commaai/neo/interface boards/gm/case.stl

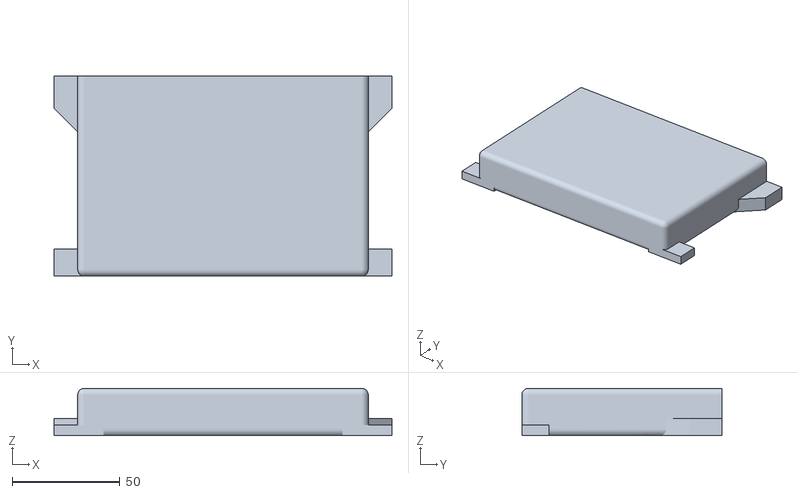
[picture p27: CAD file, 2019-02-15]
interface boards/gm/case.stl
157.0 x 93.0 x 22.0
