commaai/neo/pedal/case/pedal_connector.stl

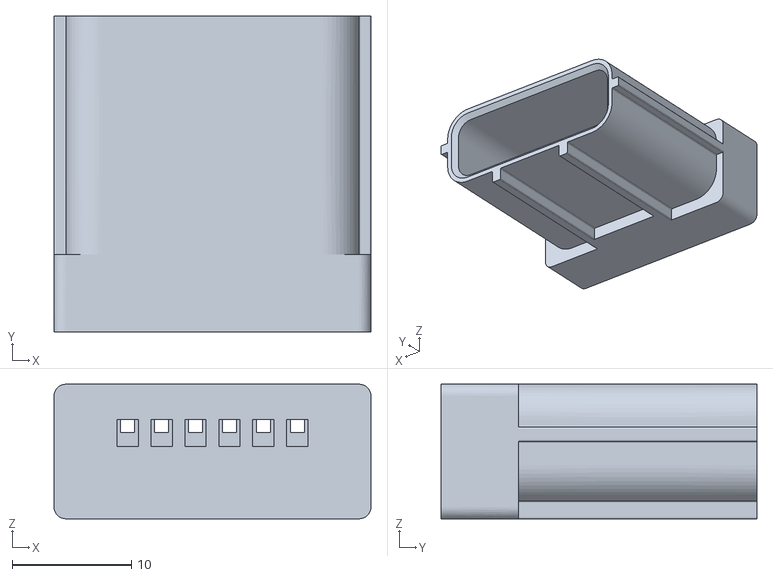
[picture p28: CAD file, 2018-03-29]
pedal/case/pedal_connector.stl
26.6 x 26.5 x 11.3
