commaai/neo/body/universal_C3_C3X_hat_frame.stl

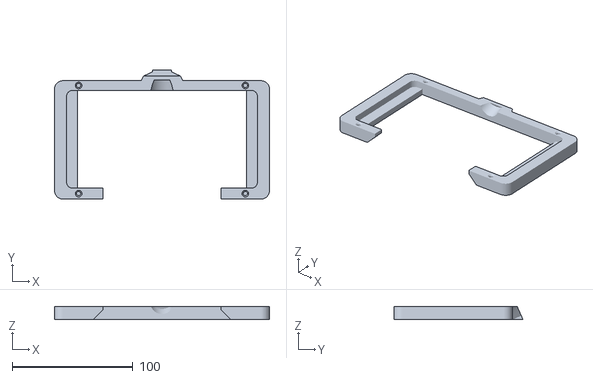
[picture p29: CAD file, 2023-12-14]
body/universal_C3_C3X_hat_frame.stl
178.0 x 106.9 x 11.0
