commaai/neo/case/comma2/comma2_mount.stl

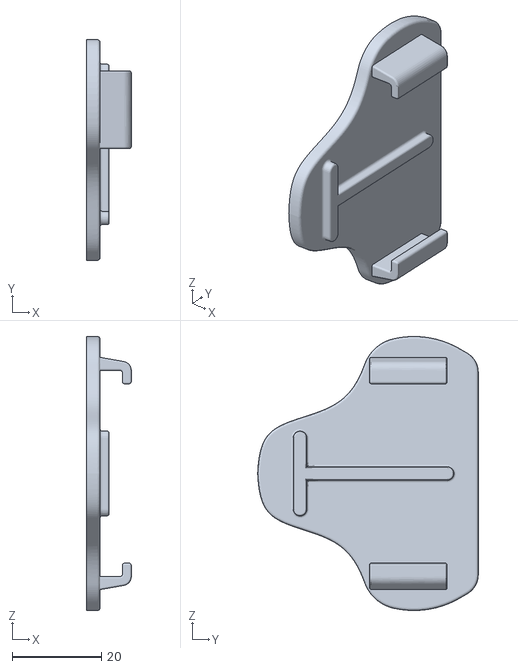
[picture p30: CAD file, 2020-01-23]
case/comma2/comma2_mount.stl
10.0 x 49.5 x 61.5
