commaai/neo/case/comma3/comma3_mount.stl

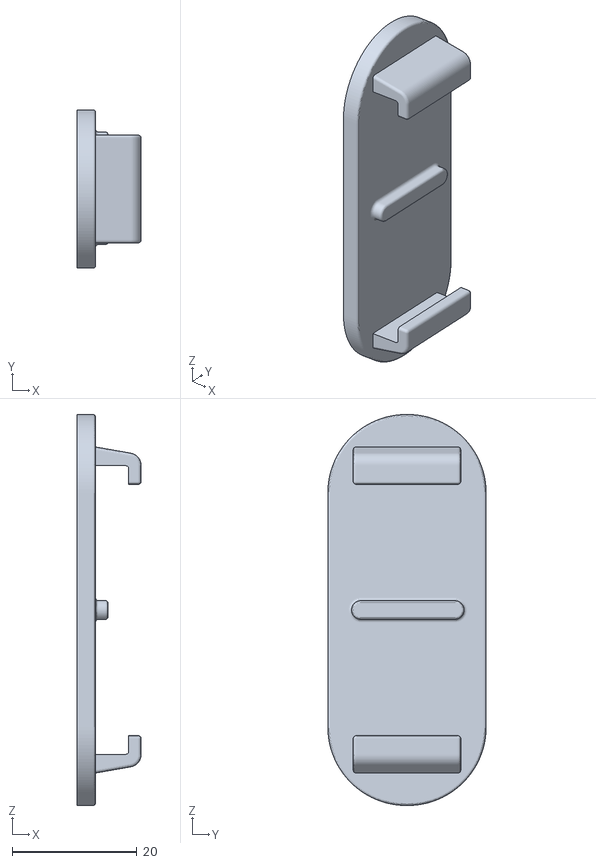
[picture p31: CAD file, 2021-10-15]
case/comma3/comma3_mount.stl
10.3 x 25.4 x 62.6
