commaai/neo/case/comma3X/3X_mount_8deg.stl

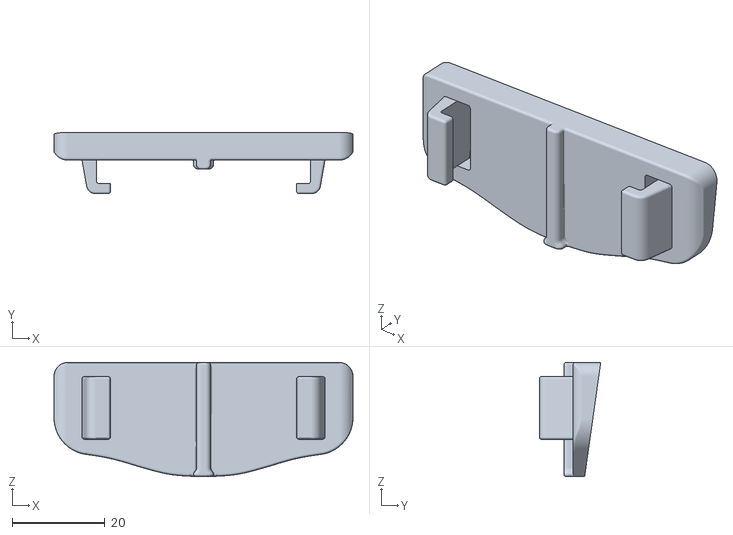
[picture p32: CAD file, 2023-07-31]
case/comma3X/3X_mount_8deg.stl
64.6 x 13.3 x 24.7
