commaai/neo/case/eon/30deg.stl

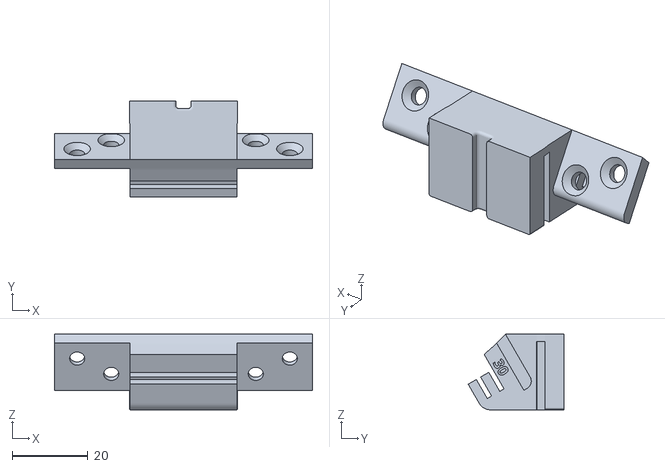
[picture p33: CAD file, 2018-02-07]
case/eon/30deg.stl
68.2 x 25.3 x 20.0
