commaai/neo/case/goproslide.stl

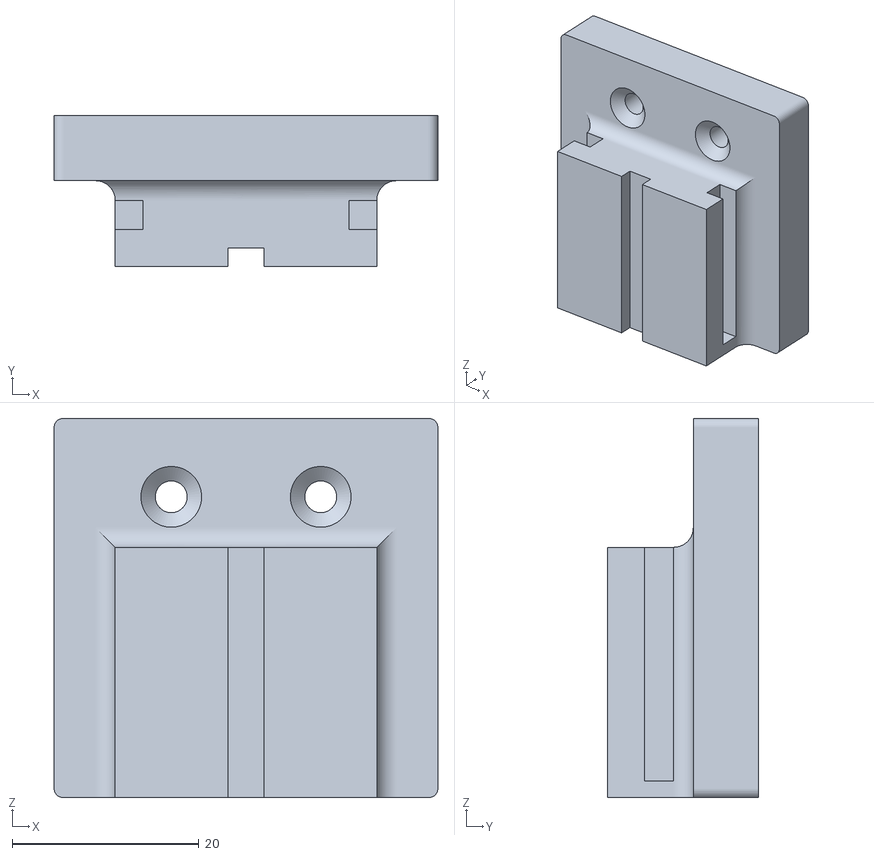
[picture p34: CAD file, 2017-01-27]
case/goproslide.stl
41.1 x 16.2 x 40.6
