commaai/neo/giraffe/fca/Giraffe_right.stl

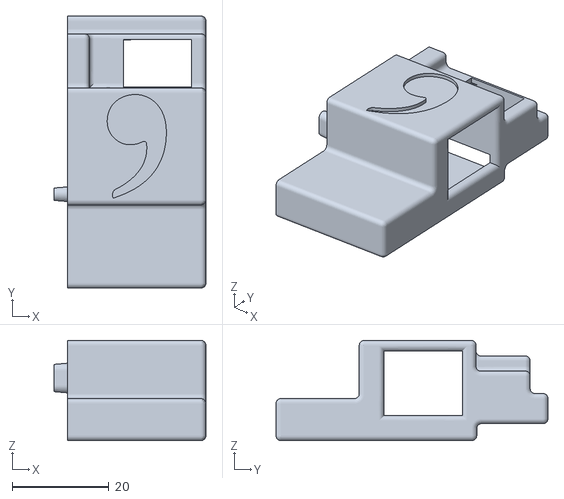
[picture p35: CAD file, 2019-02-05]
giraffe/fca/Giraffe_right.stl
31.4 x 56.2 x 20.7
