commaai/neo/giraffe/ford/mechanical/giraffe_ford_top.stl

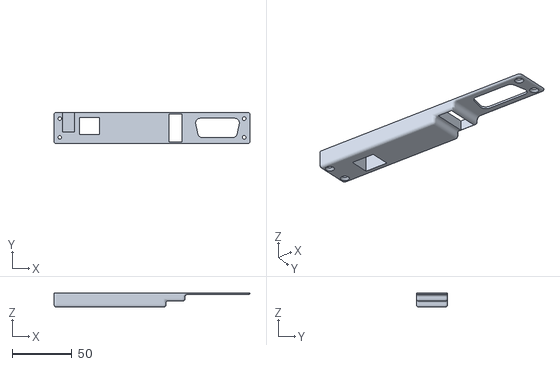
[picture p36: CAD file, 2018-09-11]
giraffe/ford/mechanical/giraffe_ford_top.stl
164.5 x 26.4 x 11.9
