commaai/neo/giraffe/honda/bosch/bosch_female_connector.stl

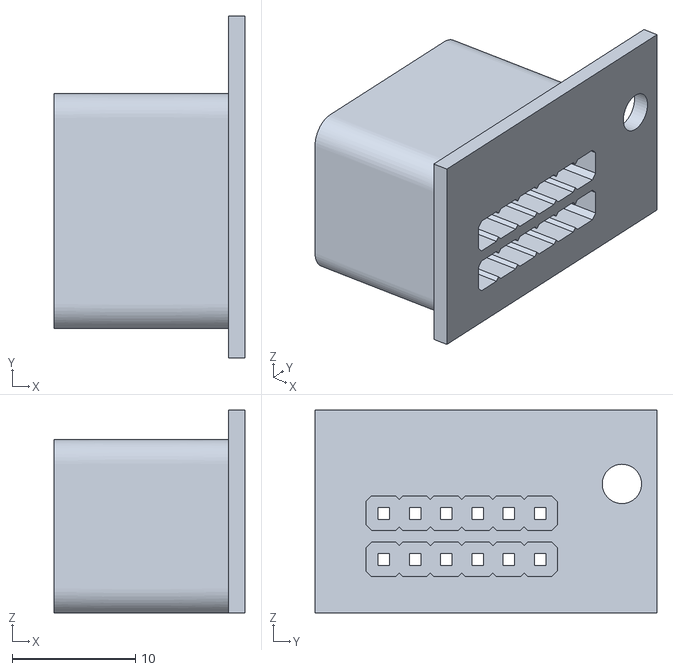
[picture p37: CAD file, 2018-08-07]
giraffe/honda/bosch/bosch_female_connector.stl
15.5 x 27.8 x 16.5
