commaai/neo/giraffe/subaru/PIP_left.stl

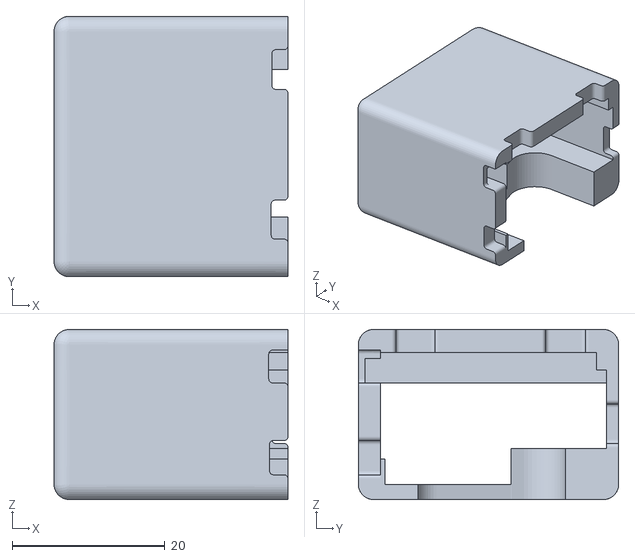
[picture p38: CAD file, 2019-04-23]
giraffe/subaru/PIP_left.stl
30.6 x 34.1 x 22.3
