commaai/neo/grey/antenna_mount_28deg.stl

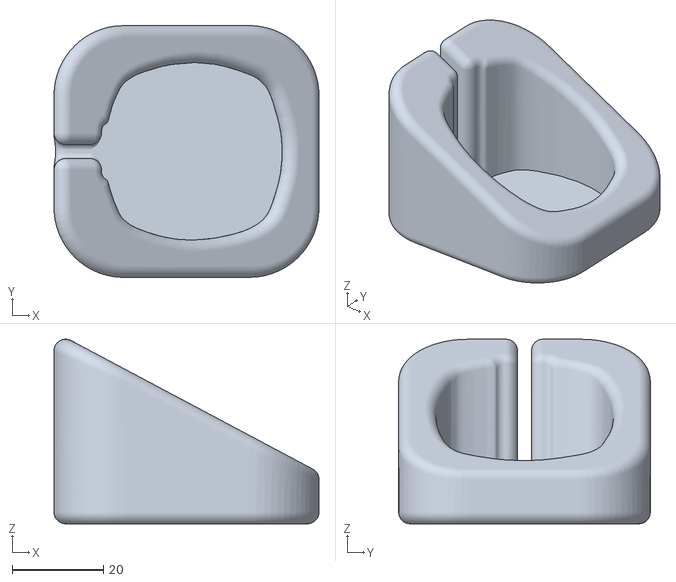
[picture p39: CAD file, 2018-09-11]
grey/antenna_mount_28deg.stl
58.0 x 55.1 x 40.4
