commaai/neo/interface boards/gm/connectors.stl

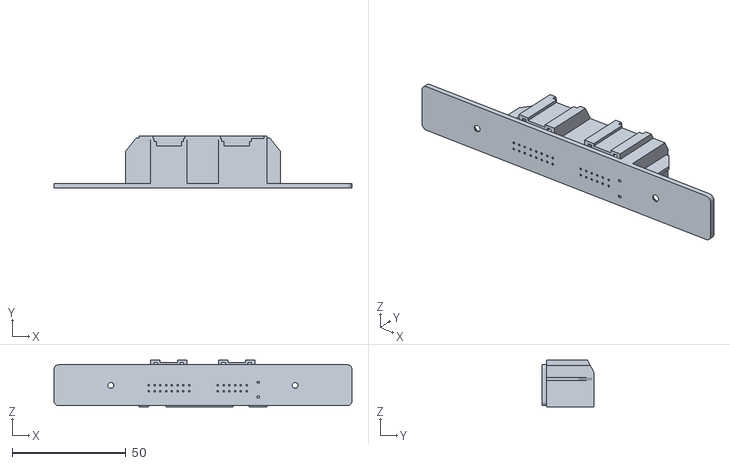
[picture p40: CAD file, 2019-02-15]
interface boards/gm/connectors.stl
131.0 x 23.0 x 20.5
