commaai/neo/pedal/case/comma.stl

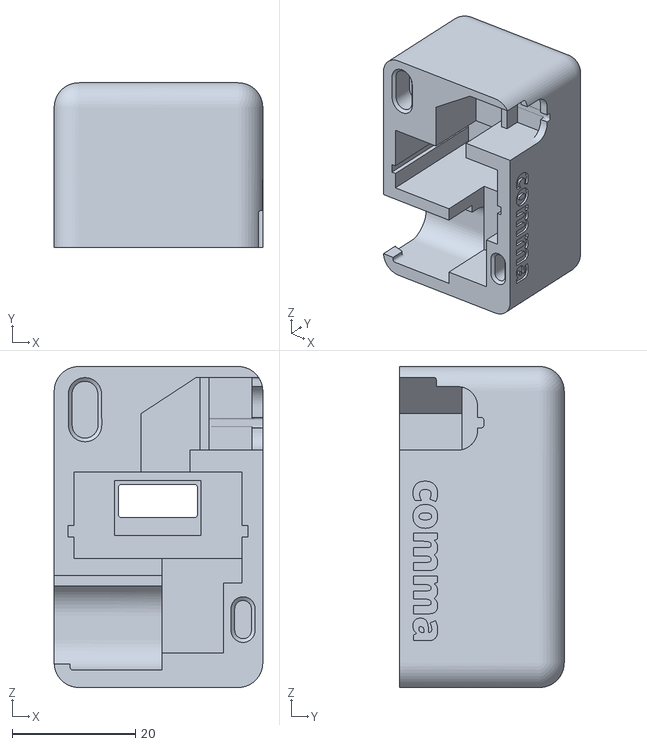
[picture p41: CAD file, 2018-03-29]
pedal/case/comma.stl
33.8 x 26.6 x 52.0
