commaai/neo/body/wheeled_stand.stl

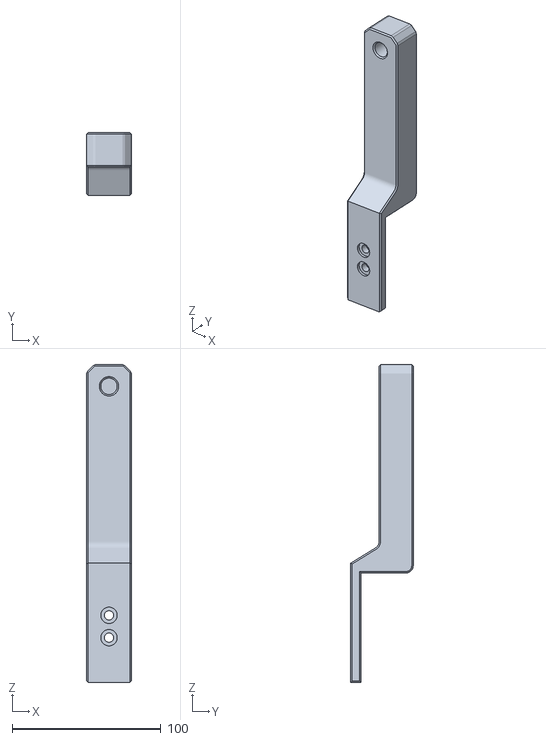
[picture p42: CAD file, 2023-12-14]
body/wheeled_stand.stl
30.0 x 42.0 x 213.5
