commaai/neo/case/cover.stl

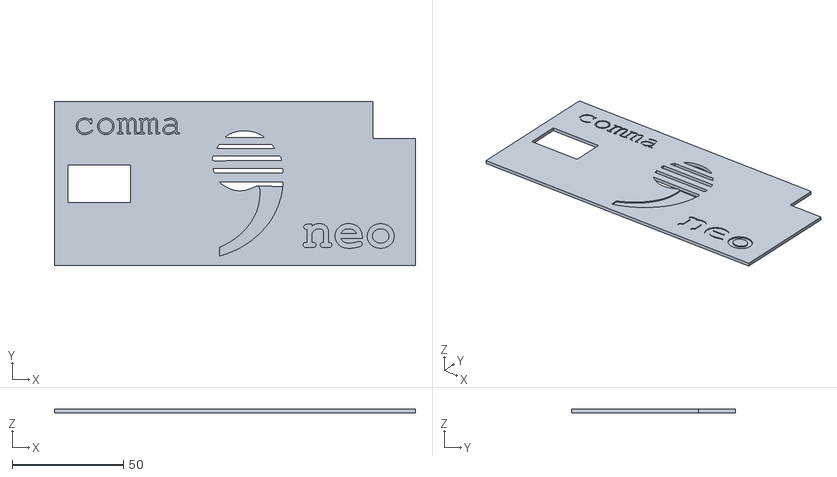
[picture p43: CAD file, 2016-11-30]
case/cover.stl
162.5 x 73.9 x 1.60
