commaai/neo/case/eon/24deg.stl

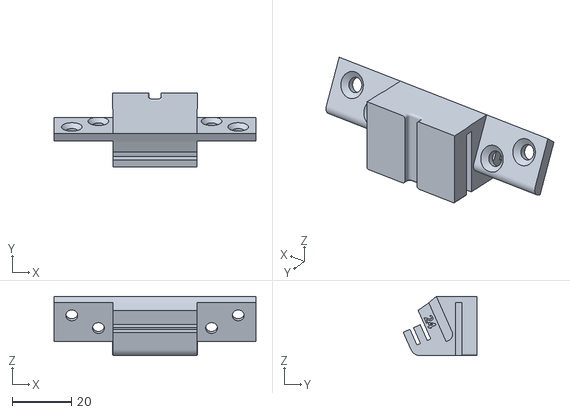
[picture p44: CAD file, 2018-02-07]
case/eon/24deg.stl
68.2 x 24.8 x 20.0
