commaai/neo/giraffe/ford/mechanical/giraffe_ford_bottom.stl

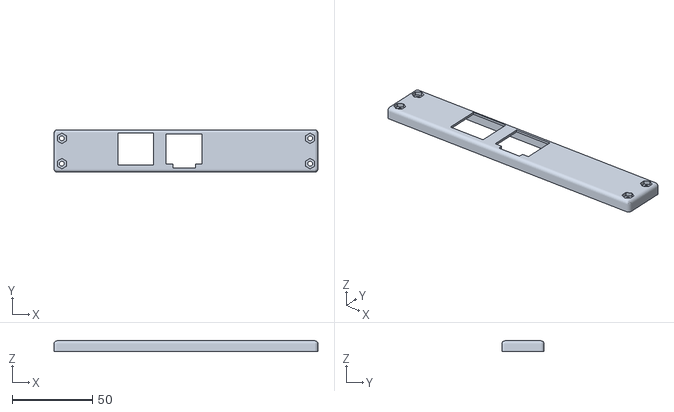
[picture p45: CAD file, 2018-09-11]
giraffe/ford/mechanical/giraffe_ford_bottom.stl
164.5 x 26.4 x 6.57
