commaai/neo/giraffe/honda/bosch/bosch_male.stl

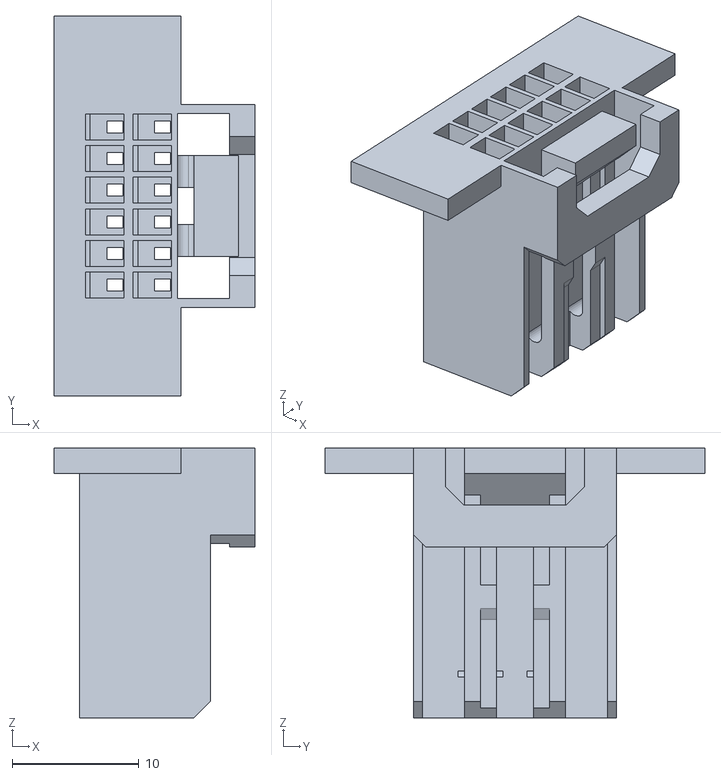
[picture p46: CAD file, 2018-08-07]
giraffe/honda/bosch/bosch_male.stl
15.9 x 30.0 x 21.3
