commaai/neo/grey/antenna_mount.stl

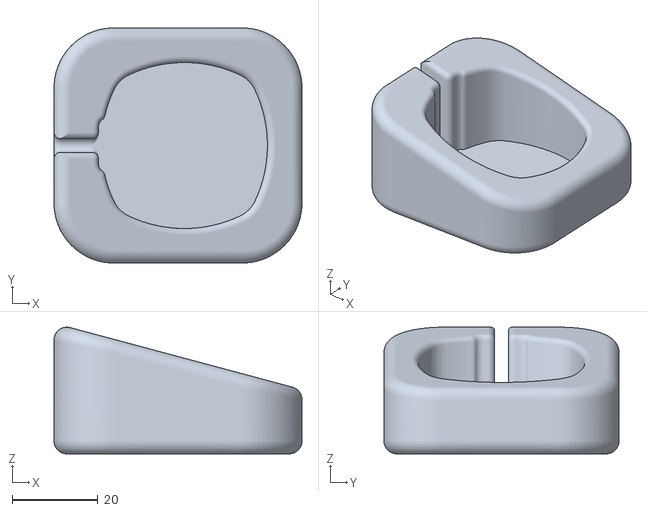
[picture p47: CAD file, 2018-03-01]
grey/antenna_mount.stl
58.0 x 55.0 x 29.6
