commaai/neo/pedal/case/pedal.stl

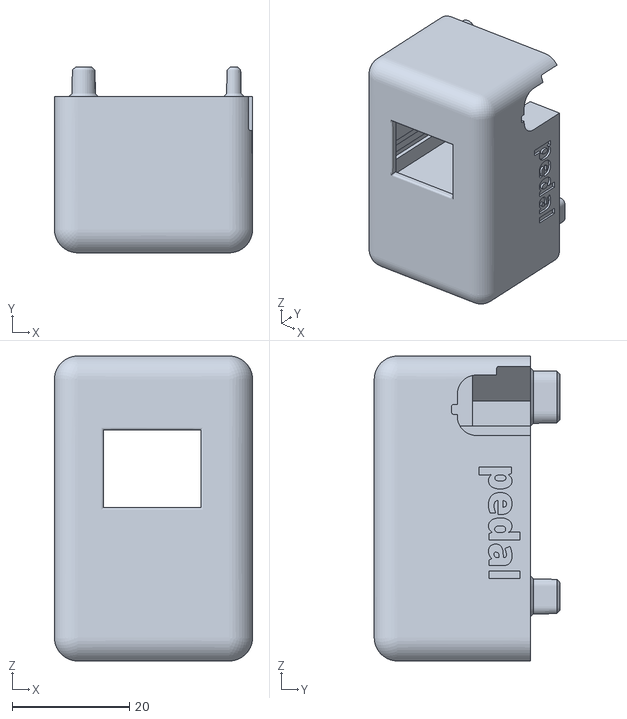
[picture p48: CAD file, 2018-03-29]
pedal/case/pedal.stl
33.8 x 31.7 x 52.0
