commaai/neo/body/C3_stand.stl

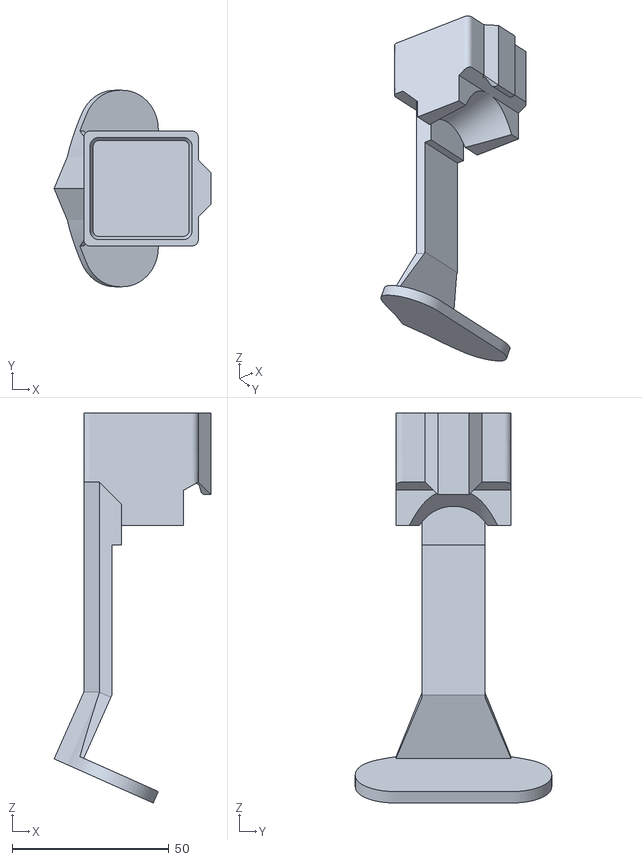
[picture p49: CAD file, 2022-05-08]
body/C3_stand.stl
50.0 x 62.6 x 124.2
