commaai/neo/case/mount.stl

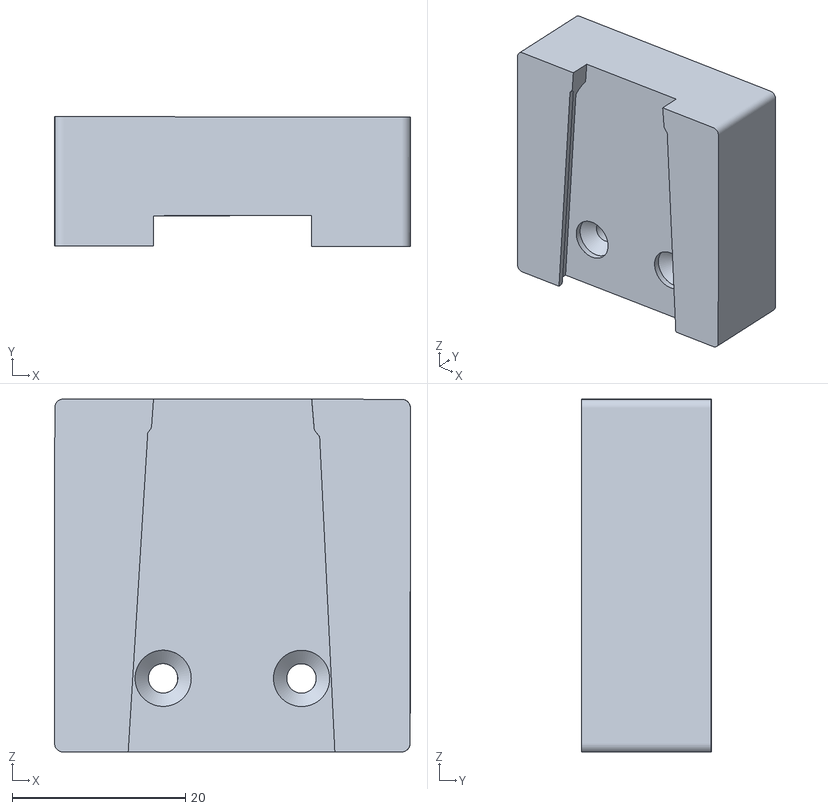
[picture p50: CAD file, 2016-11-30]
case/mount.stl
41.2 x 15.0 x 40.8
