commaai/neo/giraffe/honda/bosch/bosch_front.stl

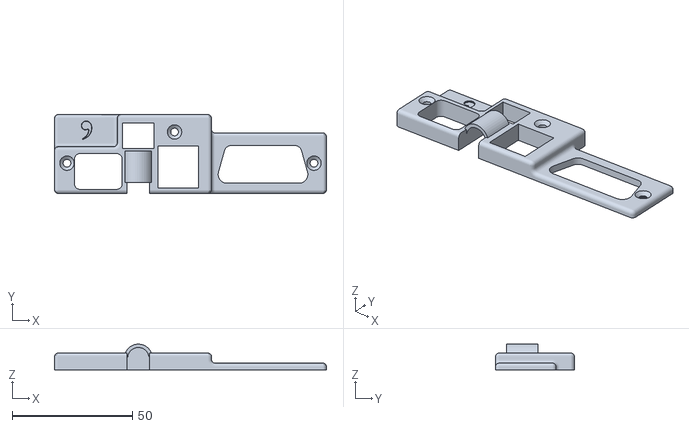
[picture p51: CAD file, 2018-08-07]
giraffe/honda/bosch/bosch_front.stl
113.0 x 32.7 x 10.7
