commaai/neo/case/bottom.stl

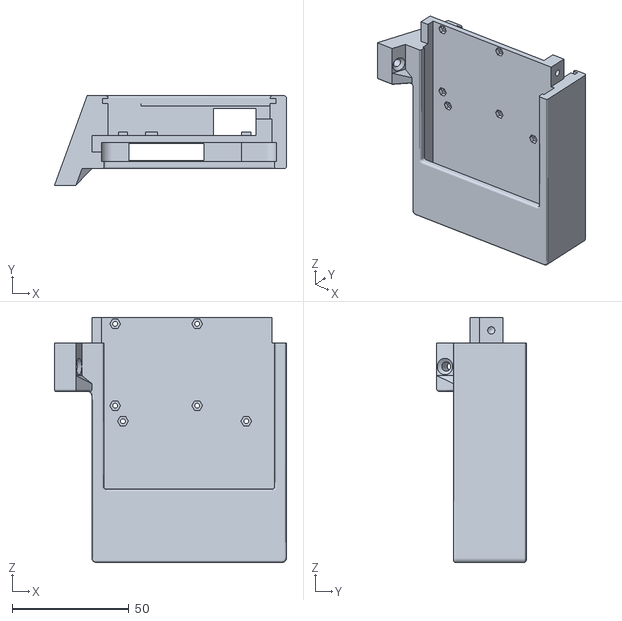
[picture p52: CAD file, 2016-11-30]
case/bottom.stl
99.3 x 38.3 x 104.9
