commaai/neo/case/top.stl

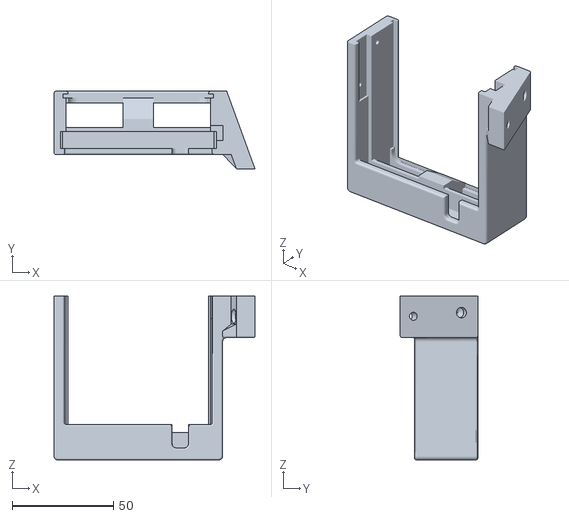
[picture p53: CAD file, 2016-11-30]
case/top.stl
99.3 x 38.3 x 81.0
