commaai/neo/car_harness/v3/GM_Harness.pdf

## TO CAR

## TO CAMERA

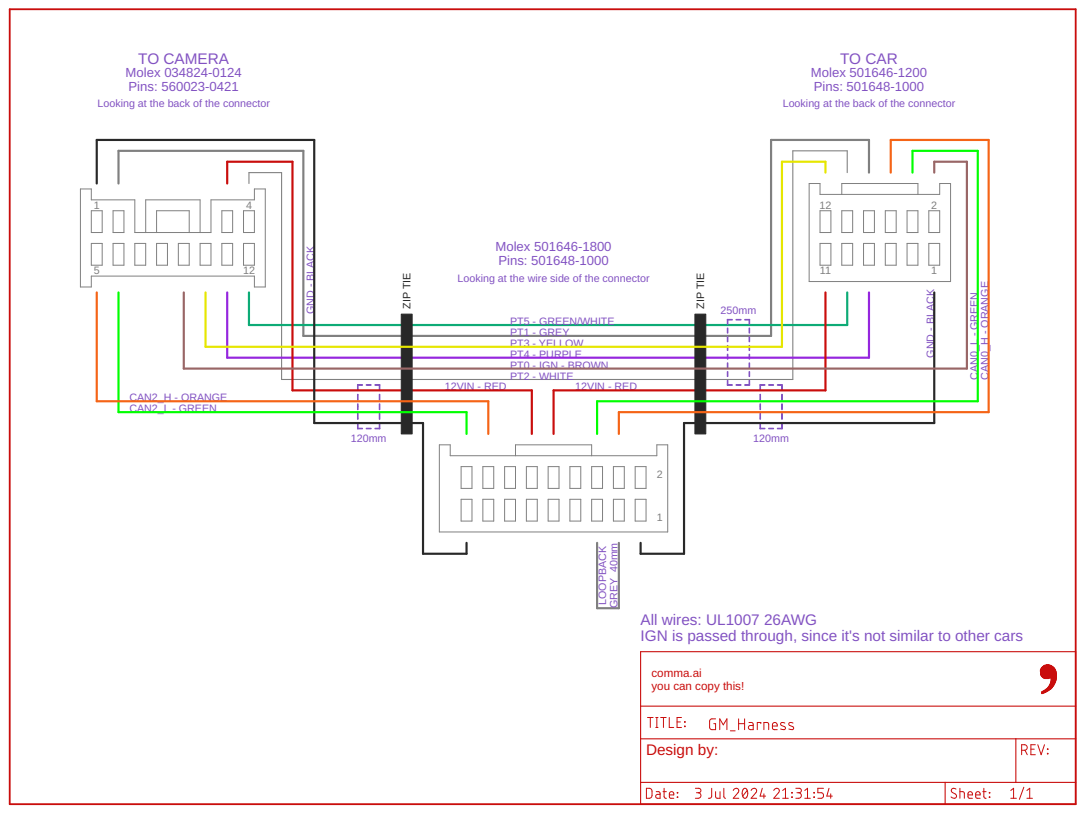
[picture p73: page 1]
Design by:; OPBACK GREY 40m; PT3 - YELLOW; CAN0_H - ORANGE; Molex 501646-1800 Pins: 501648-1000; PT1 - GREY; PT5 - GREEN/WHITE; 12VIN - RED; CAN2_H - ORANGE CAN2_L - GREEN; GND - BLACK; ZIP TIE

Molex 034824-0124
Pins: 560023-0421
Looking at the back of the connector

Looking at the back of the connector Molex 501646-1200
Pins: 501648-1000

Looking at the wire side of the connector

GND - BLACK CAN0_L - GREEN

PT4 - PURPLE
PT0 - IGN - BROWN
PT2 - WHITE

All wires: UL1007 26AWG
IGN is passed through, since it's not similar to other cars

comma.ai
you can copy this!
