commaai/neo/car_harness/v3/Honda_Bosch_A_Harness.pdf

## TO CAMERA

## TO CAR

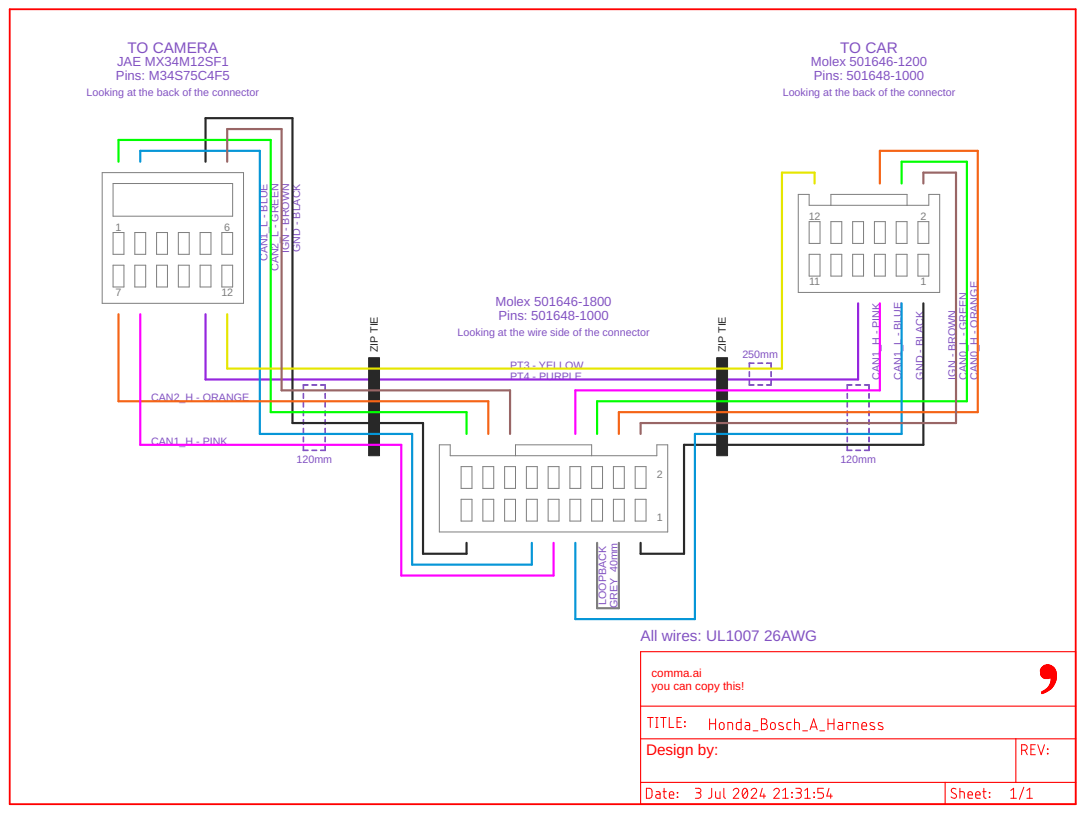
[picture p74: page 1]
Design by:; OPBACK GREY 40m; All wires: UL1007 26AWG; PT4 - PURPLE; PT3 - YELLOW; CAN2_H - ORANGE; CAN1_H - PINK; CAN1_L - BLUE; IGN - BRO; CAN1_L - BLUE CAN0_H - ORANGE; Molex 501646-1800 Pins: 501648-1000; ZIP TIE

JAE MX34M12SF1
Pins: M34S75C4F5
Looking at the back of the connector

Looking at the back of the connector Molex 501646-1200
Pins: 501648-1000

GND - BLACK CAN2_L - GREEN

GND - BLACK CAN0_L - GREEN

Looking at the wire side of the connector

comma.ai
you can copy this!
