commaai/neo/car_harness/v3/Honda_Bosch_B_Harness.pdf

## TO CAMERA

## TO CAR

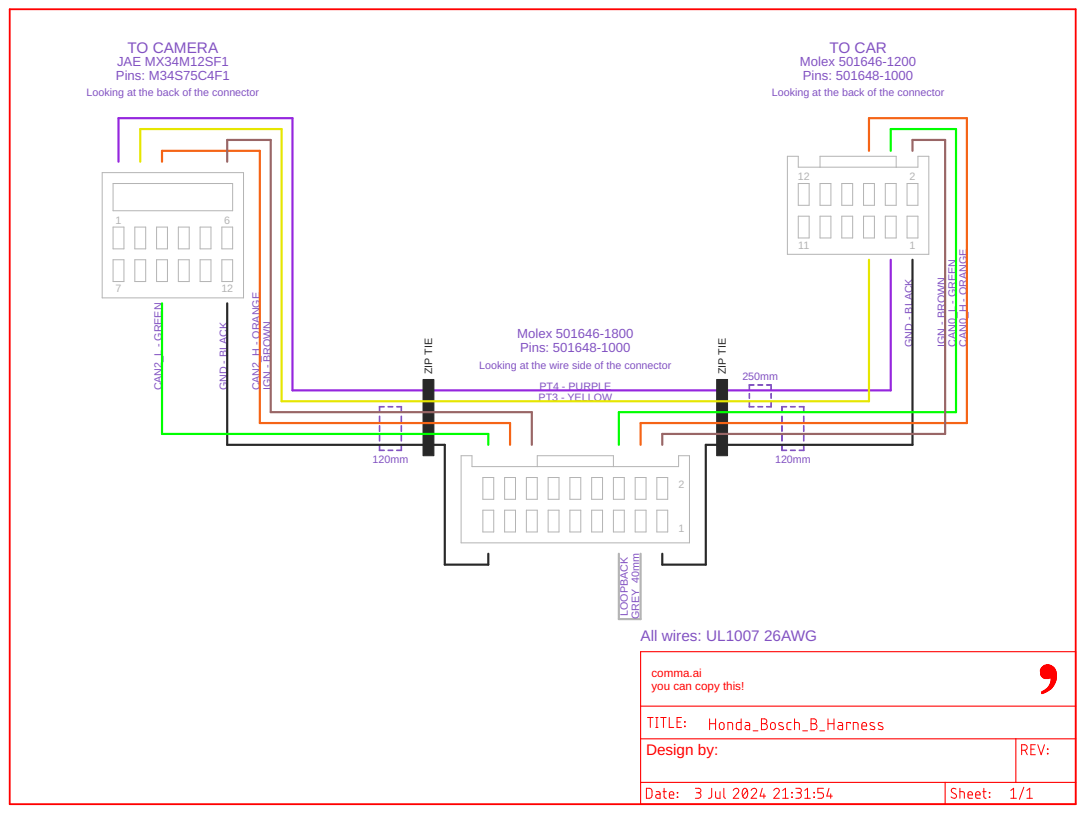
[picture p75: page 1]
Design by:; IGN - BRO; CAN2_L - GREEN; PT3 - YELLOW; PT4 - PURPLE; CAN0_H - ORANGE; Molex 501646-1800 Pins: 501648-1000; OPBACK GREY 40m; JAE MX34M12SF1 Pins: M34S75C4F1; Looking at the back of the connector; Looking at the back of the connector Molex 501646-1200; Pins: 501648-1000; All wires: UL1007 26AWG; ZIP TIE

GND - BLACK CAN0_L - GREEN

WN GND - BLACK CAN2_H - ORANGE

Looking at the wire side of the connector

comma.ai
you can copy this!
