commaai/neo/car_harness/v3/Honda_Nidec_Harness.pdf

## TO CAMERA

## TO CAR

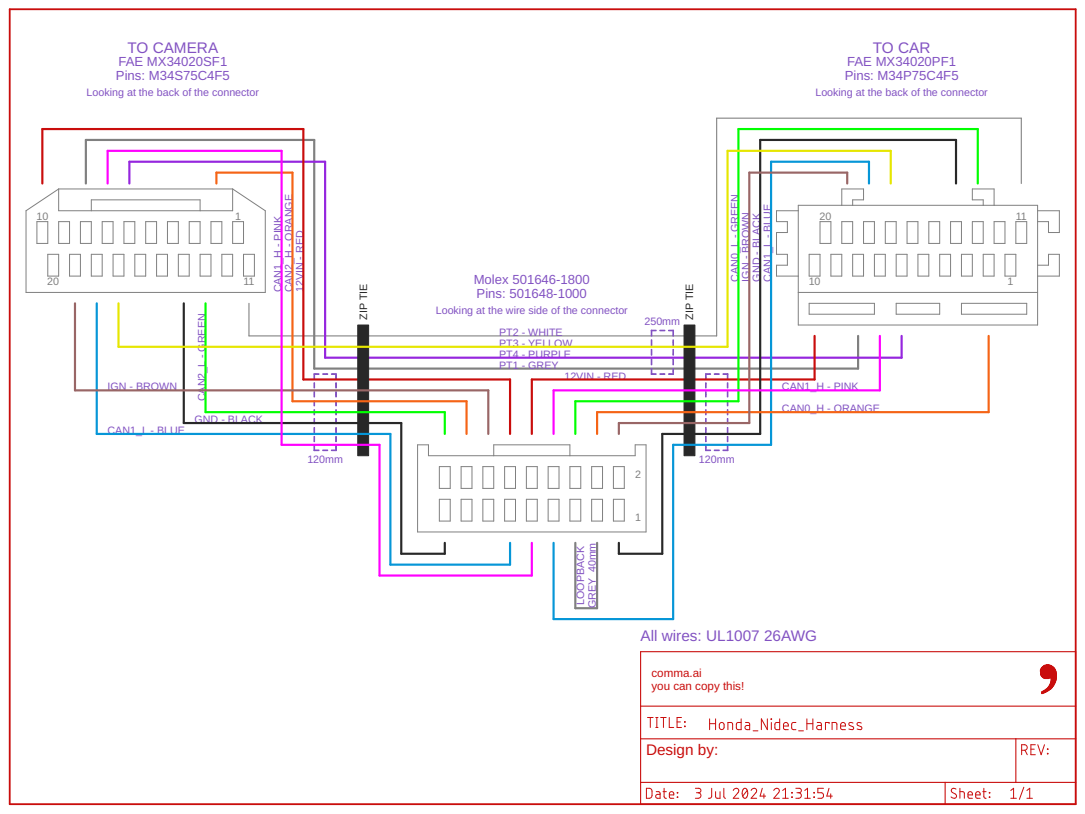
[picture p77: page 1]
Design by:; All wires: UL1007 26AWG; OPBACK GREY 40m; PT4 - PURPLE; PT3 - YELLOW; PT1 - GREY; PT2 - WHITE; Molex 501646-1800 Pins: 501648-1000; FAE MX34020SF1 Pins: M34S75C4F5; Looking at the back of the connector; Looking at the back of the connector FAE MX34020PF1; Pins: M34P75C4F5; CAN1_L - BLUE; CAN2_H - ORANGE CAN1_H - PINK; IGN - BROWN; CAN1_L - BLUE CAN0_H - ORANGE; CAN1_H - PINK; IGN - BRO; 12VIN - RED; ZIP TIE

GND - BLACK CAN0_L - GREEN

Looking at the wire side of the connector

GND - BLACK CAN²_L ⁻ GREEN

comma.ai
you can copy this!
