commaai/neo/car_harness/v3/Hyundai_A_Harness.pdf

TO CAMERA | TO CAR

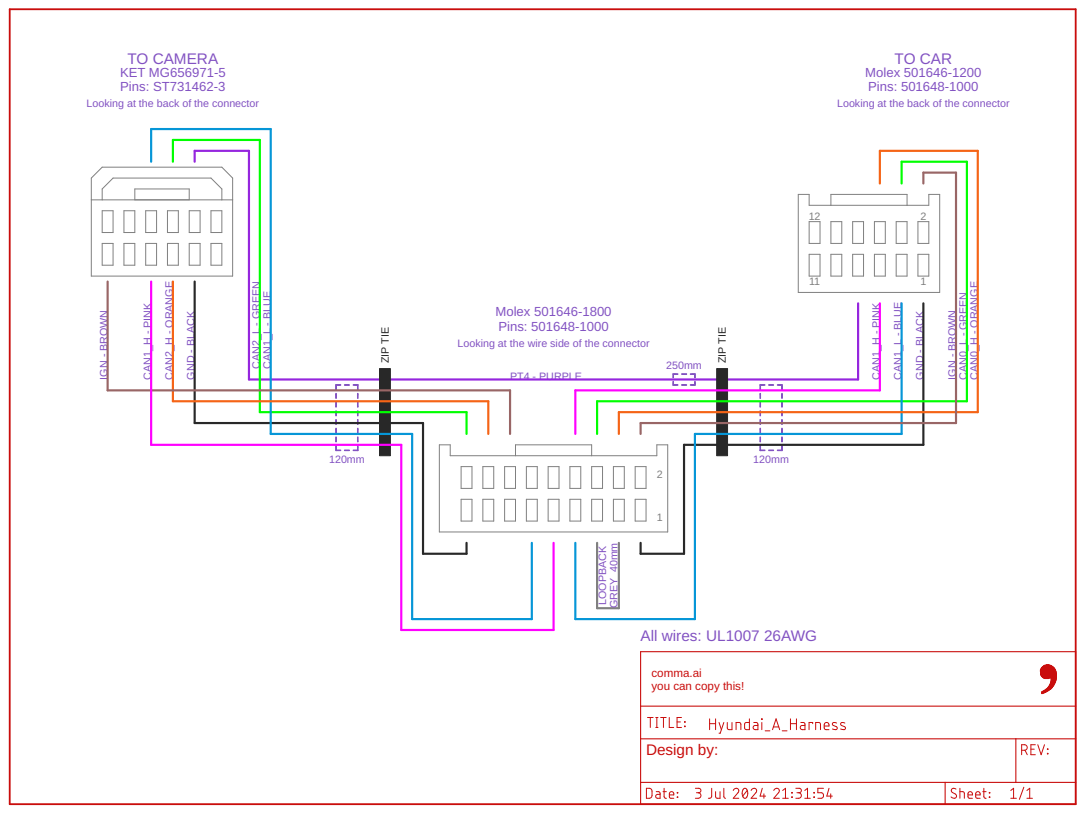
[picture p78: page 1]
Design by:; OPBACK GREY 40m; All wires: UL1007 26AWG; CAN1_L - BLUE CAN0_H - ORANGE; CAN1_H - PINK; IGN - BRO; Molex 501646-1800; Pins: 501648-1000; CAN1_L - BLUE; CAN2_L - GREEN; CAN2_H - ORANGE; PT4 - PURPLE; ZIP TIE

KET MG656971-5
Pins: ST731462-3
Looking at the back of the connector

Looking at the back of the connector Molex 501646-1200
Pins: 501648-1000

GND - BLACK CAN0_L - GREEN

CAN1_H - PINK GND - BLACK

Looking at the wire side of the connector

comma.ai
you can copy this!
