commaai/neo/car_harness/v3/Hyundai_C_Harness.pdf

TO CAMERA | TO CAR

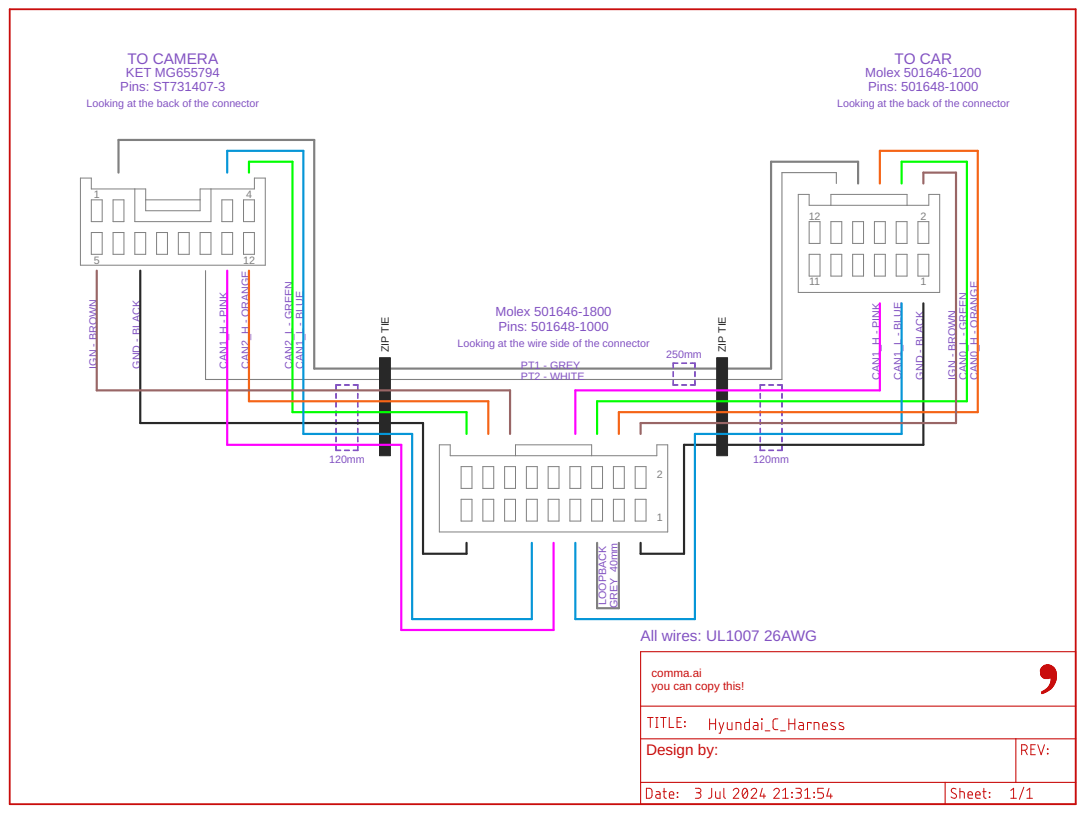
[picture p79: page 1]
Design by:; OPBACK GREY 40m; All wires: UL1007 26AWG; CAN1_L - BLUE CAN0_H - ORANGE; CAN1_H - PINK; IGN - BRO; Molex 501646-1800; Pins: 501648-1000; CAN1_L - BLUE; GND - BLACK; CAN2_L - GREEN; CAN2_H - ORANGE; PT1 - GREY; PT2 - WHITE; ZIP TIE

KET MG655794
Pins: ST731407-3
Looking at the back of the connector

Looking at the back of the connector Molex 501646-1200
Pins: 501648-1000

GND - BLACK CAN0_L - GREEN

Looking at the wire side of the connector

comma.ai
you can copy this!
