commaai/neo/car_harness/v3/Hyundai_J_Harness.pdf

TO CAMERA | TO CAR

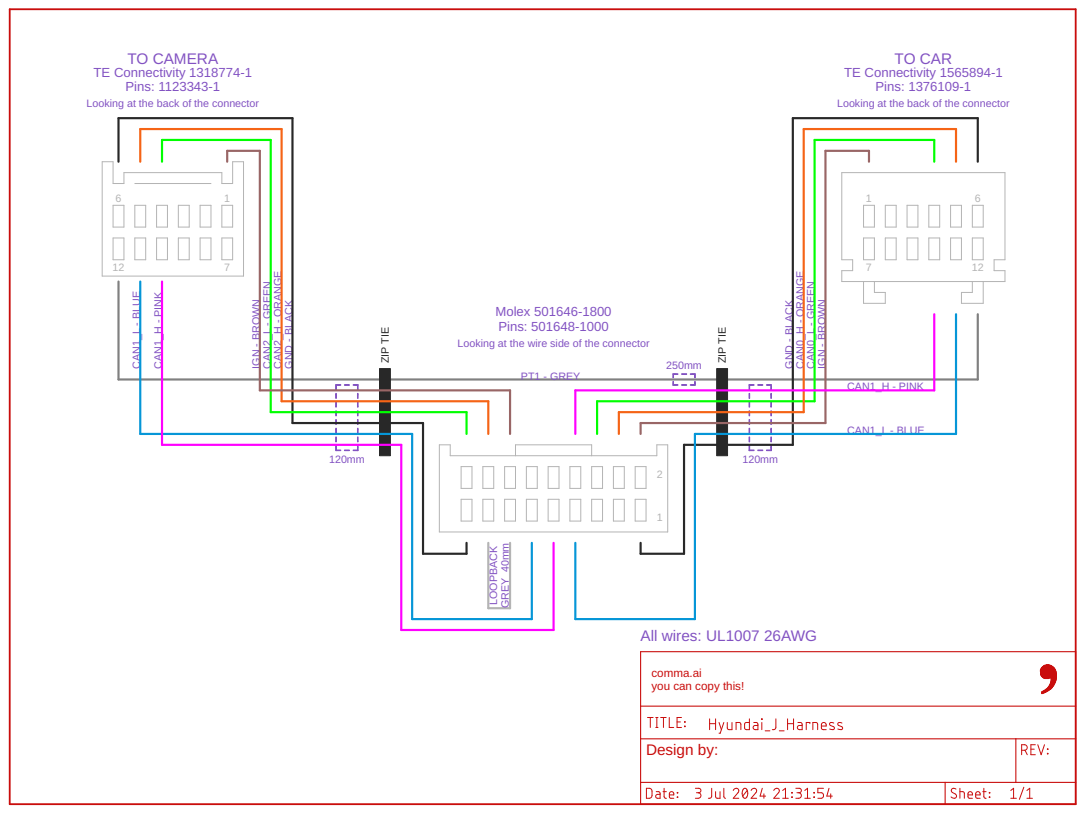
[picture p80: page 1]
Design by:; OPBACK GREY 40m; All wires: UL1007 26AWG; CAN1_L - BLUE; CAN0_H - ORANGE CAN1_H - PINK; IGN - BRO; Molex 501646-1800 Pins: 501648-1000; CAN1_L - BLUE CAN1_H - PINK; GND - BLACK; CAN2_L - GREEN; CAN2_H - ORANGE; PT1 - GREY; TE Connectivity 1318774-1 Pins: 1123343-1; TE Connectivity 1565894-1 Pins: 1376109-1; ZIP TIE

Looking at the back of the connector

GND - BLACK CAN0_L - GREEN

Looking at the wire side of the connector

comma.ai
you can copy this!
