commaai/neo/car_harness/v3/Mazda_Harness.pdf

## TO CAR

## TO CAMERA

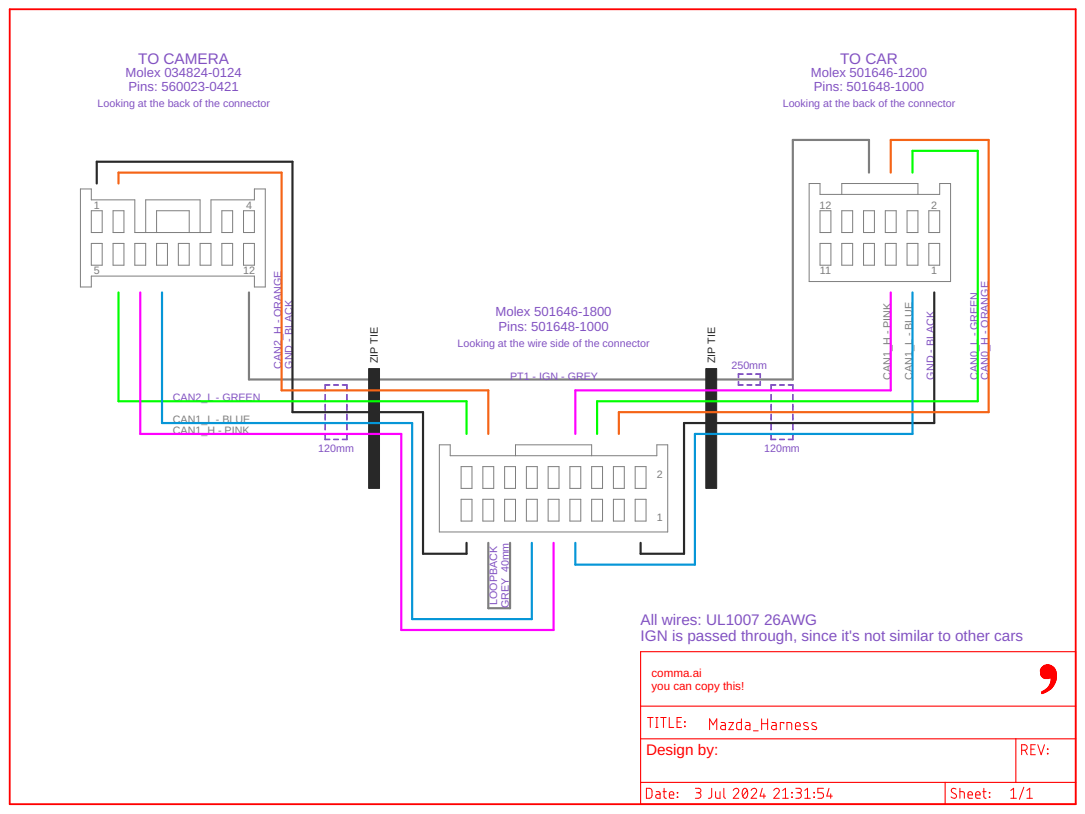
[picture p82: page 1]
CAN1_H - PINK; CAN1_L - BLUE; CAN¹_H ⁻ PINK; CAN¹_L ⁻ BLUE; Design by:; OPBACK GREY 40m; CAN0_H - ORANGE; Molex 501646-1800 Pins: 501648-1000; PT1 - IGN - GREY; CAN2_H - ORANGE; CAN2_L - GREEN; GND - BLACK; ZIP TIE

Molex 034824-0124
Pins: 560023-0421
Looking at the back of the connector

Looking at the back of the connector Molex 501646-1200
Pins: 501648-1000

GND - BLACK CAN0_L - GREEN

Looking at the wire side of the connector

All wires: UL1007 26AWG
IGN is passed through, since it's not similar to other cars

comma.ai
you can copy this!
