commaai/neo/car_harness/v3/Nissan_A_Harness.pdf

## TO ADAS UNIT

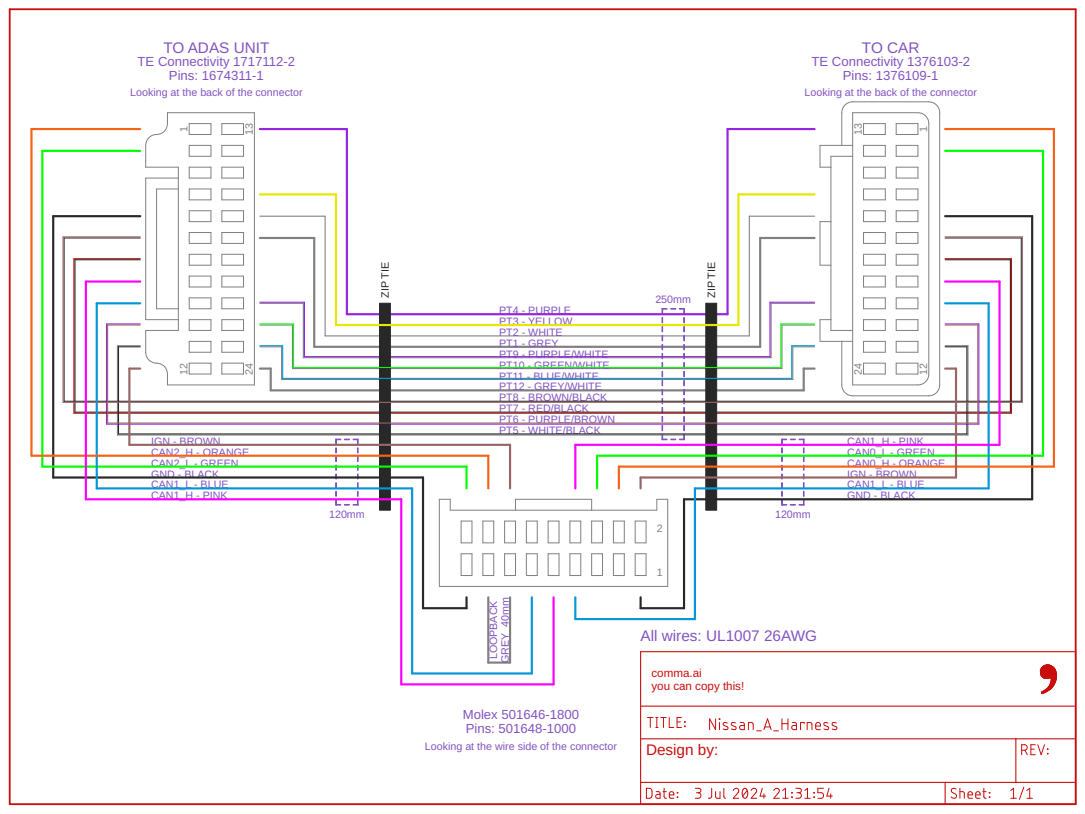
[picture p83: page 1]
Design by:; OPBACK GREY 40m; All wires: UL1007 26AWG; Molex 501646-1800 Pins: 501648-1000; PT4 - PURPLE; TE Connectivity 1717112-2 Pins: 1674311-1; Looking at the back of the connector; TO CAR; PT3 - YELLOW PT2 - WHITE PT1 - GREY PT9 - PURPLE/WHITE PT10 - GREEN/WHITE PT11 - BLUE/WHITE PT12 - GREY/WHITE PT8 - BROWN/BLACK; GND - BLACK; CAN0_L - GREEN; CAN1_L - BLUE; CAN0_H - ORANGE; CAN1_H - PINK; IGN - BROWN; CAN1_L - BLUE CAN1_H - PINK; CAN2_L - GREEN; CAN2_H - ORANGE; ZIP TIE

Looking at the back of the connector TE Connectivity 1376103-2
Pins: 1376109-1

PT7 - RED/BLACK
PT6 - PURPLE/BROWN
PT5 - WHITE/BLACK

comma.ai
you can copy this!

Looking at the wire side of the connector
