commaai/neo/car_harness/v3/Subaru_A_Harness.pdf

## TO CAMERA

## TO CAR

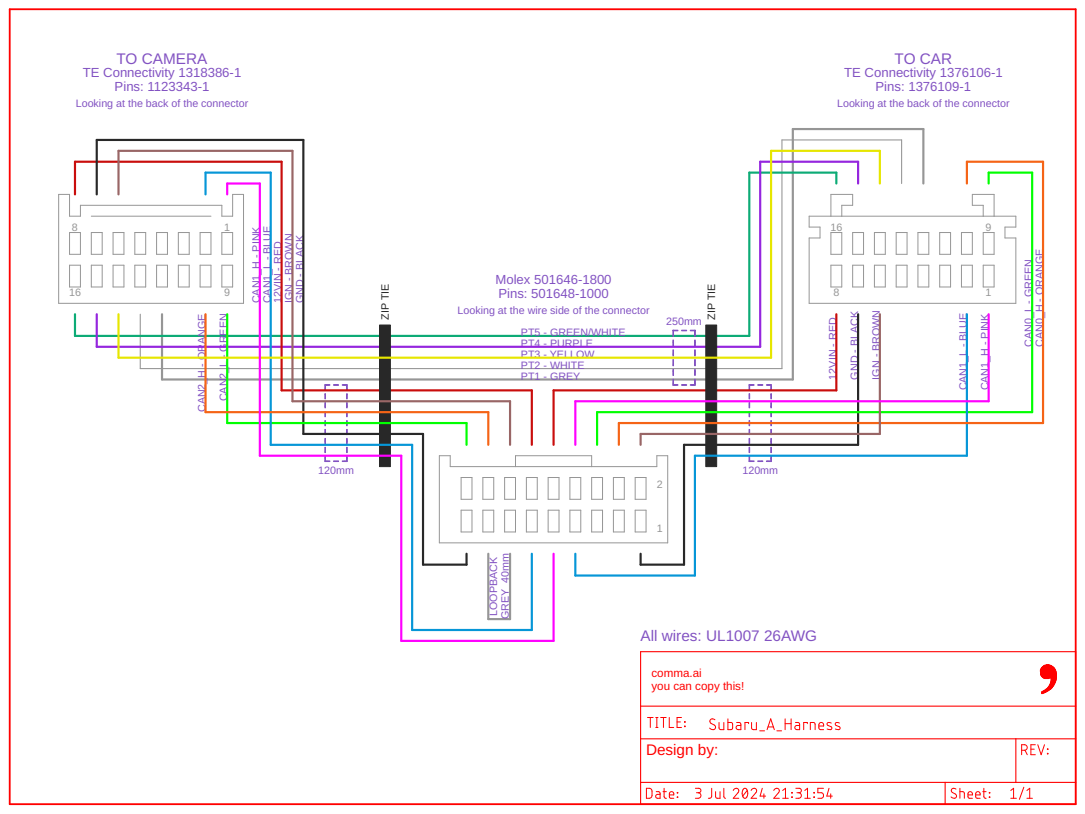
[picture p84: page 1]
Design by:; All wires: UL1007 26AWG; OPBACK GREY 40m; TE Connectivity 1318386-1 Pins: 1123343-1; Molex 501646-1800 Pins: 501648-1000; PT5 - GREEN/WHITE CAN²_H ⁻ ORANGE; CAN¹_H ⁻ PINK; IGN - BRO; CAN2_L - GREEN; CAN1_L - BLUE 12VIN - RED; CAN1_H - PINK; CAN1_L - BLUE; 12VIN - RED; CAN0_L - GREEN; CAN0_H - ORANGE; ZIP TIE

Looking at the back of the connector TE Connectivity 1376106-1
Pins: 1376109-1

Looking at the back of the connector

WN GND - BLACK

Looking at the wire side of the connector

PT4 - PURPLE
PT3 - YELLOW
PT2 - WHITE
PT1 - GREY

comma.ai
you can copy this!
