commaai/neo/car_harness/v3/Subaru_D_Harness.pdf

## TO CAMERA

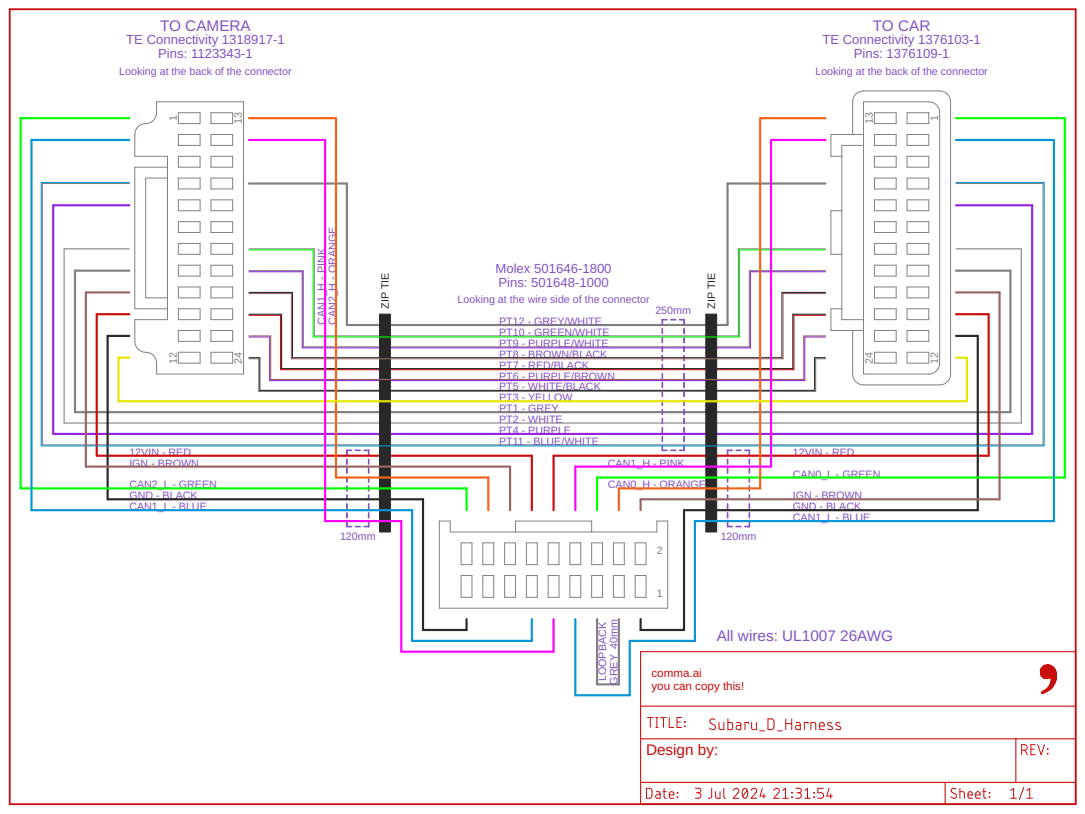
[picture p87: page 1]
Design by:; OPBACK GREY 40m; All wires: UL1007 26AWG; Molex 501646-1800 Pins: 501648-1000; TE Connectivity 1318917-1 Pins: 1123343-1; Looking at the back of the connector; TO CAR; PT9 - PURPLE/WHITE; PT10 - GREEN/WHITE; PT8 - BROWN/BLACK; GND - BLACK; CAN0_L - GREEN; CAN1_L - BLUE; CAN1_H - PINK; IGN - BROWN; CAN2_H - ORANGE; PT12 - GREY/WHITE; ZIP TIE

Looking at the back of the connector TE Connectivity 1376103-1
Pins: 1376109-1

Looking at the wire side of the connector

PT7 - RED/BLACK
PT6 - PURPLE/BROWN
PT5 - WHITE/BLACK
PT3 - YELLOW
PT1 - GREY
PT2 - WHITE
PT4 - PURPLE
PT11 - BLUE/WHITE

12VIN - RED | | 12VIN - RED

CAN2_L - GREEN
GND - BLACK

CAN0_H - ORANGE

comma.ai
you can copy this!
