commaai/neo/car_harness/v3/Template_Harness.pdf

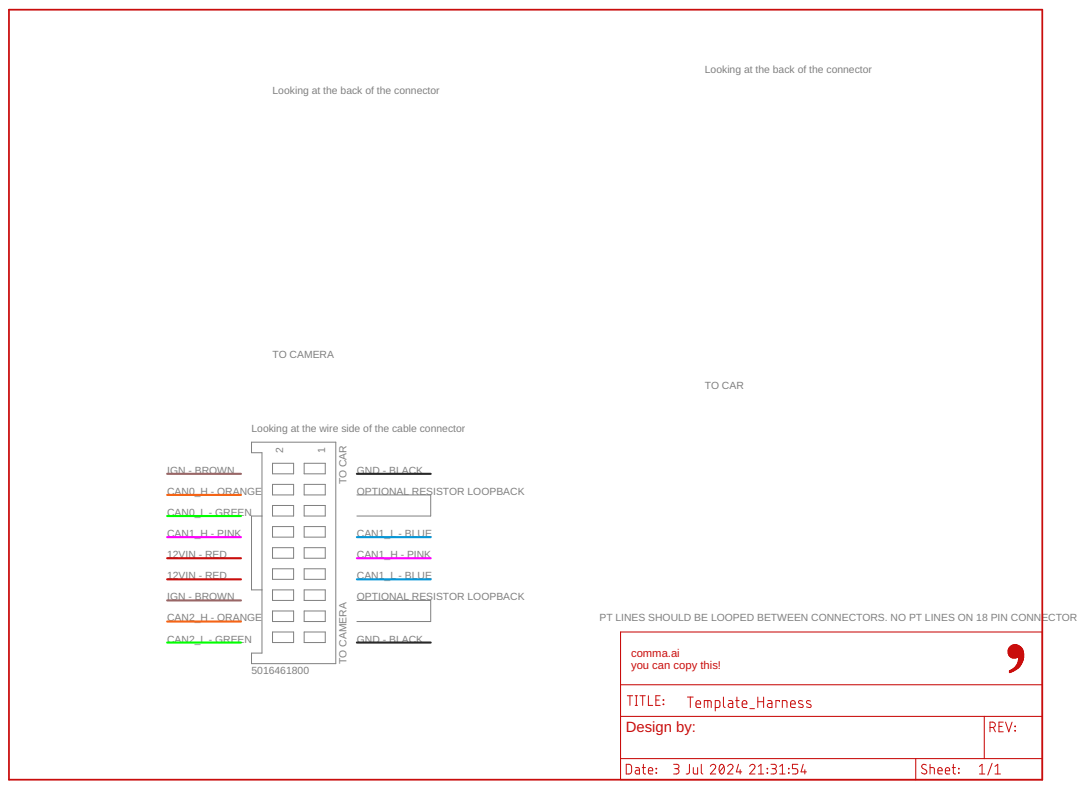
[picture p88: page 1]
Looking at the back of the connector; TO CAMERA; TO CAR; GND - BLACK; IGN - BROWN; CAN1_L - BLUE; CAN0_L - GREEN; CAN2_L - GREEN; CAN0_H - ORANGE; CAN2_H - ORANGE; CAN1_H - PINK; 12VIN - RED; Design by:

Looking at the wire side of the cable connector

MERA TO CAR OPTIONAL RESISTOR LOOPBACK
GND - BLACK

CAN1_L - BLUE
OPTIONAL RESISTOR LOOPBACK

PT LINES SHOULD BE LOOPED BETWEEN CONNECTORS. NO PT LINES ON 18 PIN CONNECTOR

comma.ai
you can copy this!
