commaai/neo/car_harness/v3/Tesla_AP2+.pdf

# LATERAL CONTROL HARNESS CONNECTOR

## Intercepting the Chassis bus

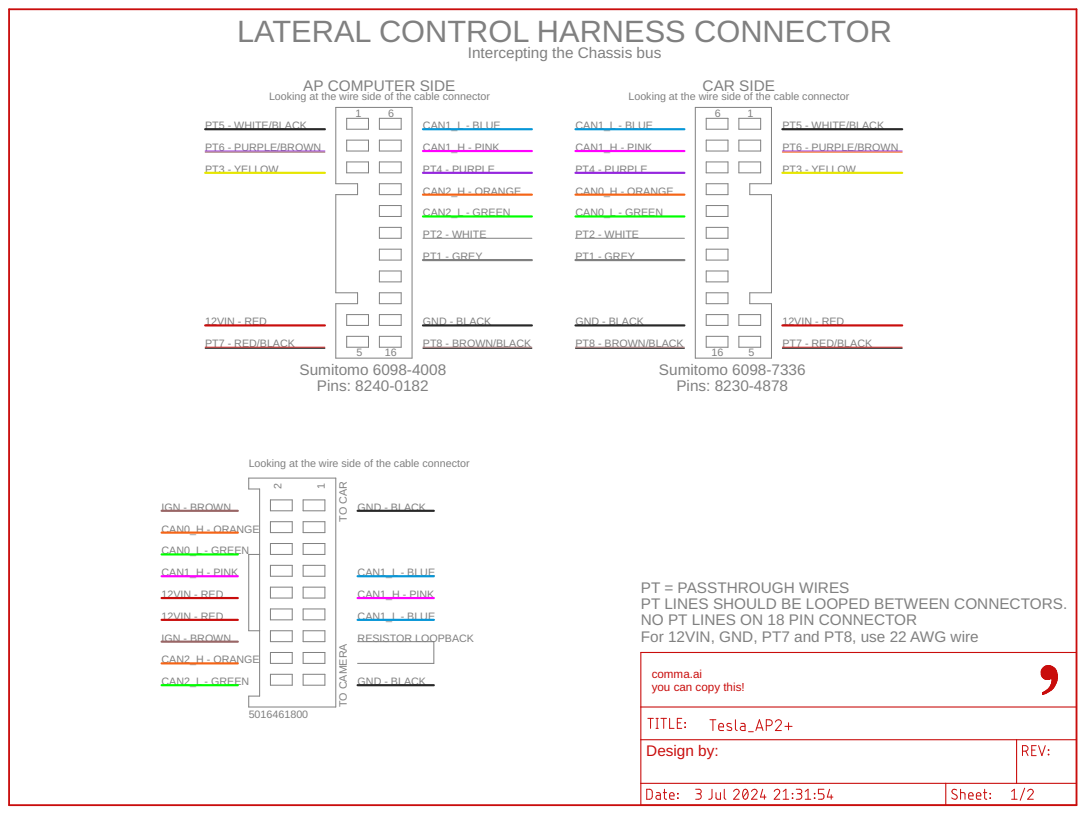
[picture p89: page 1]
Sumitomo 6098-4008 Pins: 8240-0182; Sumitomo 6098-7336 Pins: 8230-4878; 12VIN - RED; GND - BLACK; CAN1_H - PINK; CAN1_L - BLUE; CAN2_H - ORANGE; CAN2_L - GREEN; CAN0_L - GREEN; CAN0_H - ORANGE; PT3 - YELLOW; PT4 - PURPLE; PT1 - GREY; PT2 - WHITE; PT5 - WHITE/BLACK; PT6 - PURPLE/BROWN; PT7 - RED/BLACK; PT8 - BROWN/BLACK; IGN - BROWN; RESISTOR LOOPBACK; Design by:

Looking at the wire side of the cable connector AP COMPUTER SIDE

Looking at the wire side of the cable connector CAR SIDE

Looking at the wire side of the cable connector

MERA TO CAR
GND - BLACK

PT = PASSTHROUGH WIRES
PT LINES SHOULD BE LOOPED BETWEEN CONNECTORS. NO PT LINES ON 18 PIN CONNECTOR
For 12VIN, GND, PT7 and PT8, use 22 AWG wire

comma.ai
you can copy this!

# LONGITUDINAL CONTROL HARNESS CONNECTOR

## Intercepting the Powertrain bus

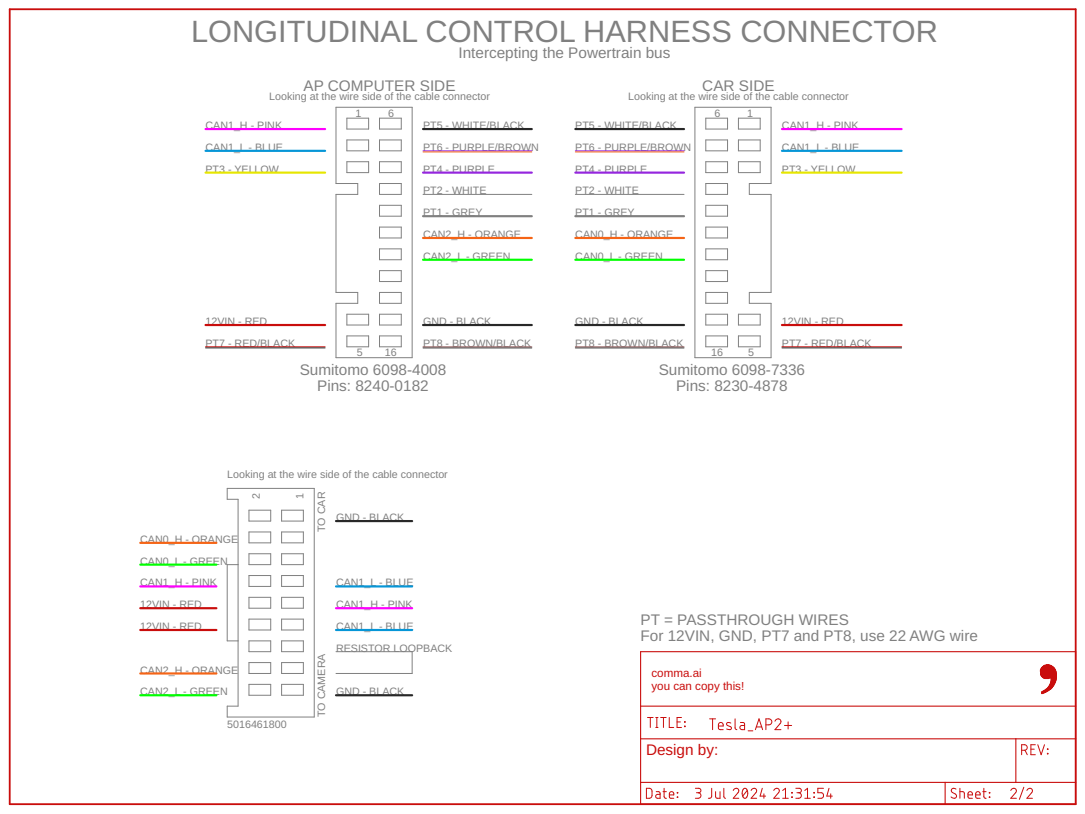
[picture p90: page 2]
Sumitomo 6098-4008 Pins: 8240-0182; Sumitomo 6098-7336 Pins: 8230-4878; 12VIN - RED; GND - BLACK; PT3 - YELLOW; PT4 - PURPLE; PT7 - RED/BLACK; PT8 - BROWN/BLACK; PT1 - GREY; PT2 - WHITE; CAN0_L - GREEN; CAN2_H - ORANGE; CAN0_H - ORANGE; CAN2_L - GREEN; CAN1_H - PINK; CAN1_L - BLUE; PT5 - WHITE/BLACK; PT6 - PURPLE/BROWN; 1 CAN1_L - BLUE; RESISTOR LOOPBACK; Design by:

Looking at the wire side of the cable connector AP COMPUTER SIDE

Looking at the wire side of the cable connector CAR SIDE

Looking at the wire side of the cable connector

MERA TO CAR
GND - BLACK

PT = PASSTHROUGH WIRES
For 12VIN, GND, PT7 and PT8, use 22 AWG wire

comma.ai
you can copy this!
