commaai/neo/car_harness/v3/Toyota_A_Harness.pdf

## TO CAR

## TO CAMERA

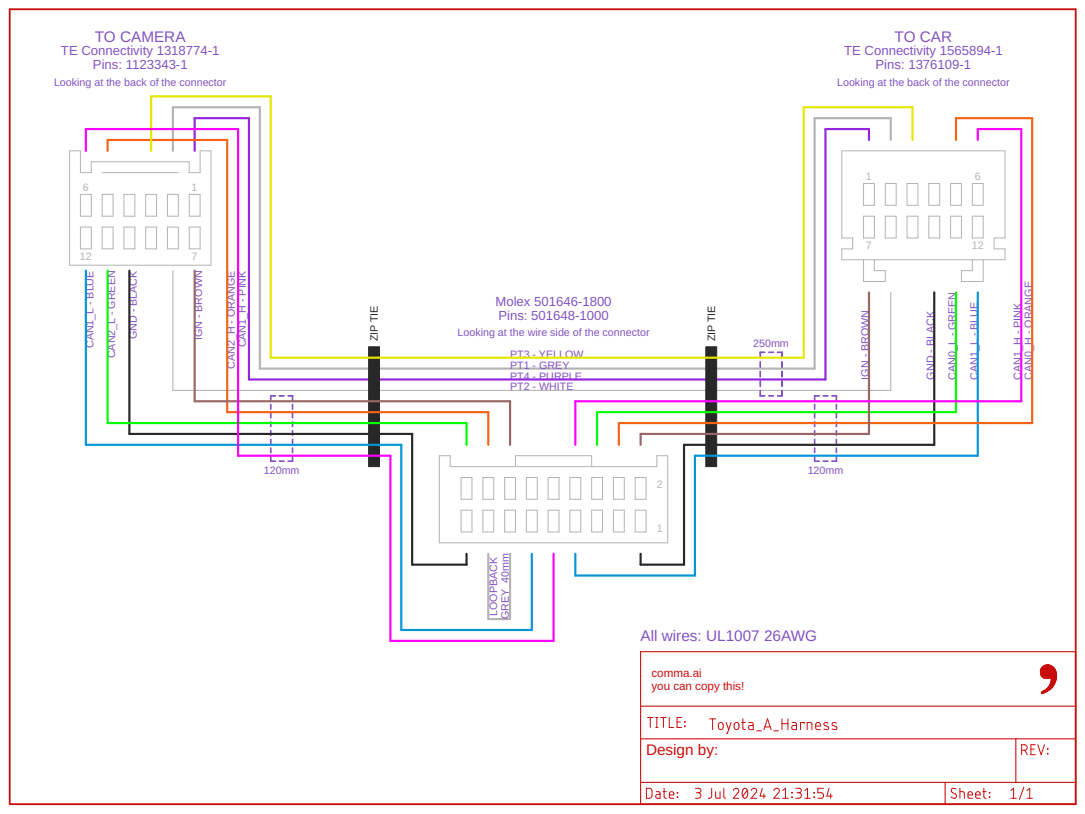
[picture p91: page 1]
Design by:; PT4 - PURPLE; PT3 - YELLOW; CAN2_H - ORANGE CAN1_H - PINK; IGN - BRO; CAN1_L - BLUE; Molex 501646-1800 Pins: 501648-1000; PT1 - GREY; PT2 - WHITE; OPBACK GREY 40m; TE Connectivity 1318774-1 Pins: 1123343-1; All wires: UL1007 26AWG; ZIP TIE

Looking at the back of the connector TE Connectivity 1565894-1
Pins: 1376109-1

Looking at the back of the connector

WN GND - BLACK CAN2_L - GREEN

CAN1_L - BLUE CAN0_H - ORANGE CAN1_H - PINK

GND - BLACK CAN0_L - GREEN

Looking at the wire side of the connector

comma.ai
you can copy this!
