commaai/neo/car_harness/v3/Toyota_B_Harness.pdf

## TO CAMERA

## TO CAR

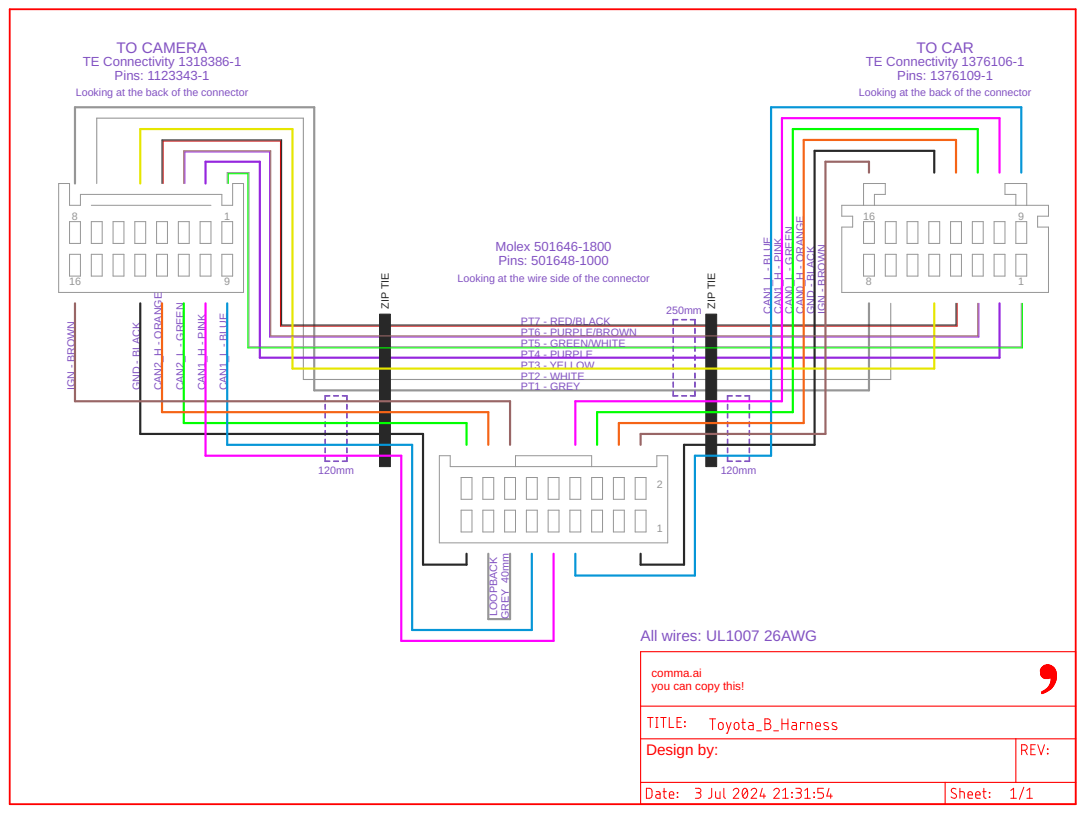
[picture p92: page 1]
Design by:; All wires: UL1007 26AWG; OPBACK GREY 40m; TE Connectivity 1318386-1 Pins: 1123343-1; Molex 501646-1800 Pins: 501648-1000; PT5 - GREEN/WHITE CAN²_H ⁻ ORANGE; CAN¹_H ⁻ PINK; IGN - BRO; CAN1_L - BLUE; CAN1_H - PINK; CAN0_H - ORANGE; PT6 - PURPLE/BROWN; PT7 - RED/BLACK; ZIP TIE

Looking at the back of the connector TE Connectivity 1376106-1
Pins: 1376109-1

Looking at the back of the connector

WN GND - BLACK CAN1_L - BLUE CAN0_L - GREEN

Looking at the wire side of the connector

WN GND - BLACK CAN2_L - GREEN

PT4 - PURPLE
PT3 - YELLOW
PT2 - WHITE
PT1 - GREY

comma.ai
you can copy this!
