commaai/neo/car_harness/v3/VW_Harness.pdf

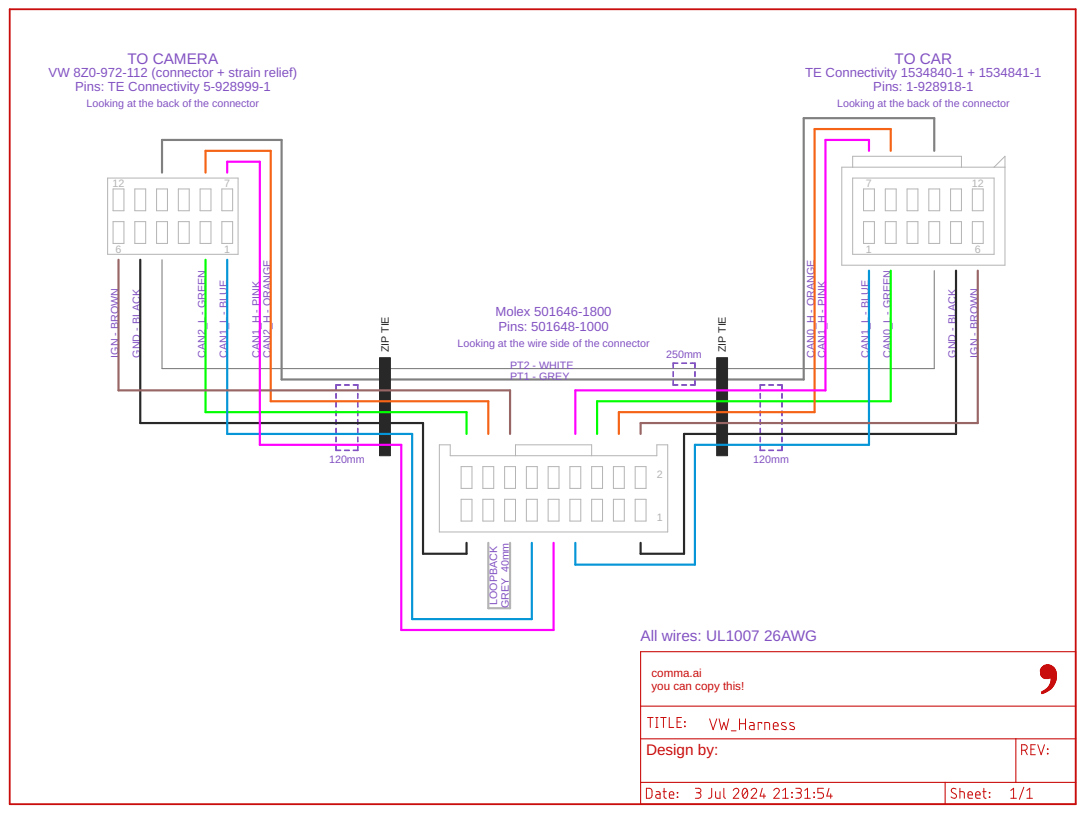
[picture p93: page 1]
Design by:; TO CAMERA; TO CAR; OPBACK GREY 40m; All wires: UL1007 26AWG; GND - BLACK; CAN0_L - GREEN; IGN - BRO; Molex 501646-1800 Pins: 501648-1000; CAN1_L - BLUE CAN1_H - PINK; CAN2_L - GREEN; CAN2_H - ORANGE; Pins: 1-928918-1; PT1 - GREY; PT2 - WHITE; ZIP TIE

VW 8Z0-972-112 (connector + strain relief)
Pins: TE Connectivity 5-928999-1
Looking at the back of the connector

Looking at the back of the connector TE Connectivity 1534840-1 + 1534841-1

CAN1_L - BLUE CAN0_H - ORANGE CAN1_H - PINK

Looking at the wire side of the connector

comma.ai
you can copy this!
