commaai/neo/giraffe/fca/fca_giraffe.sch.pdf

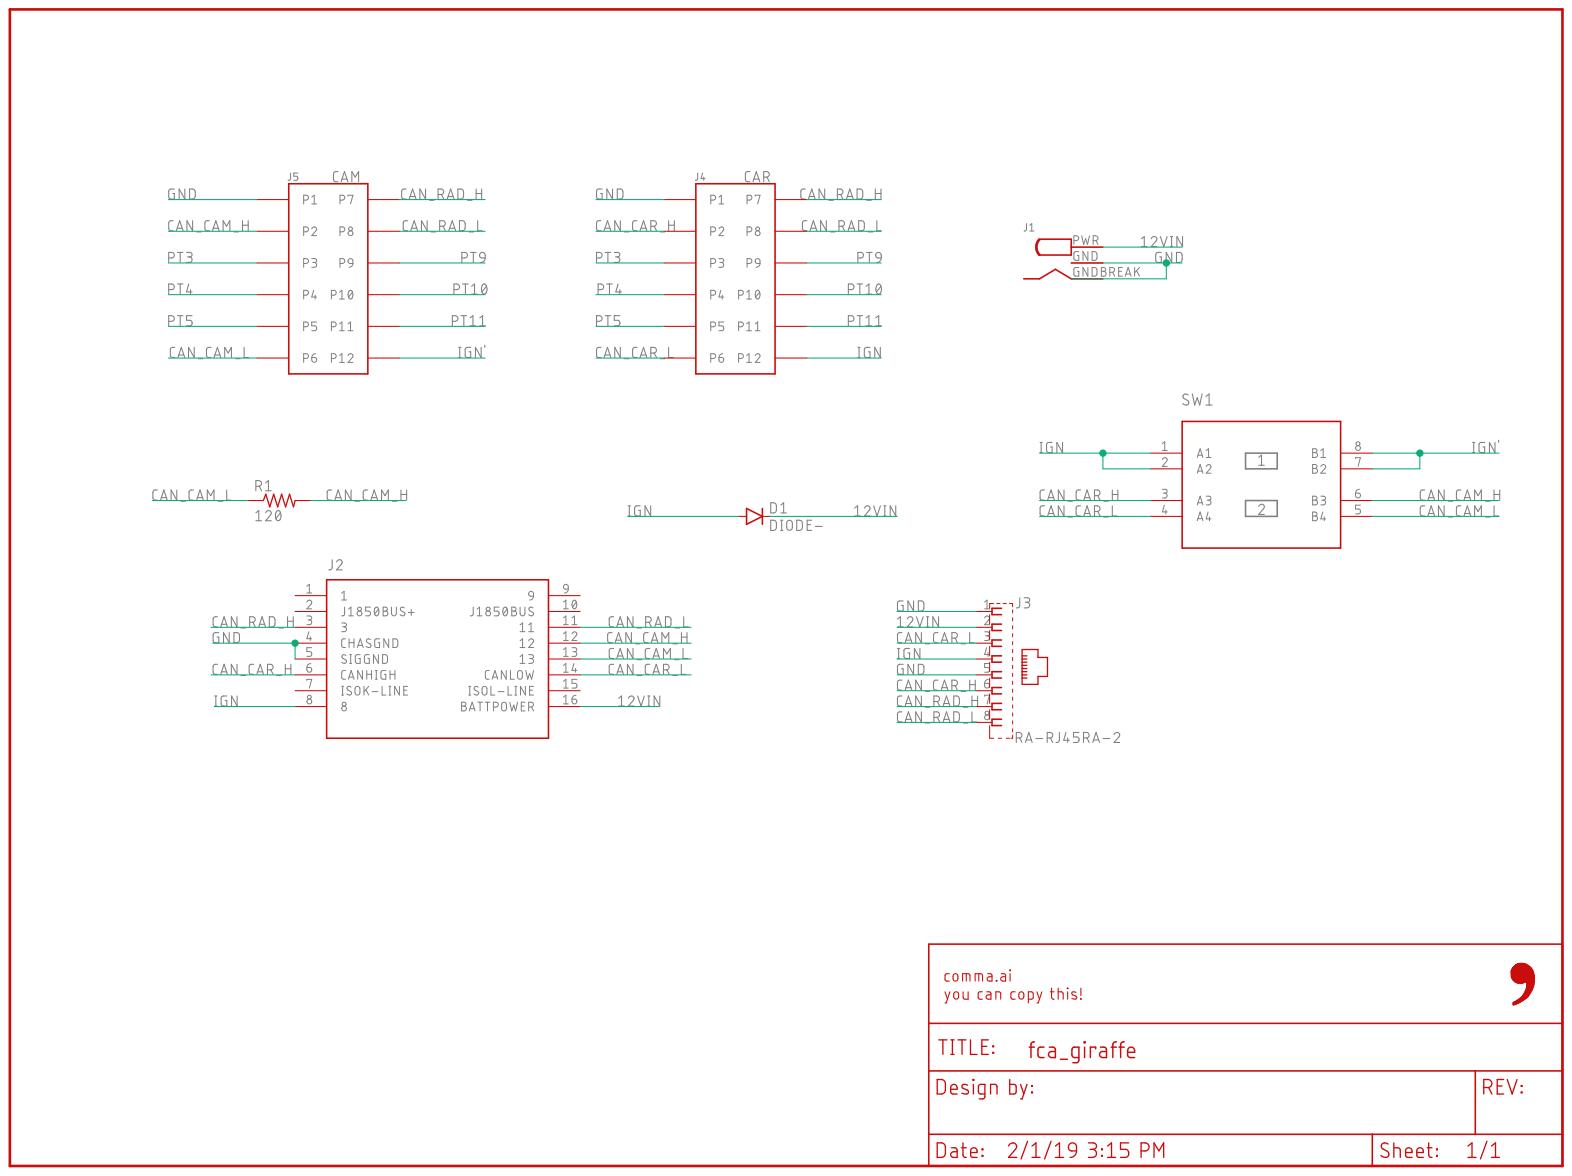
[picture p97: page 1]
