commaai/neo/giraffe/toyota/giraffe12.sch.pdf

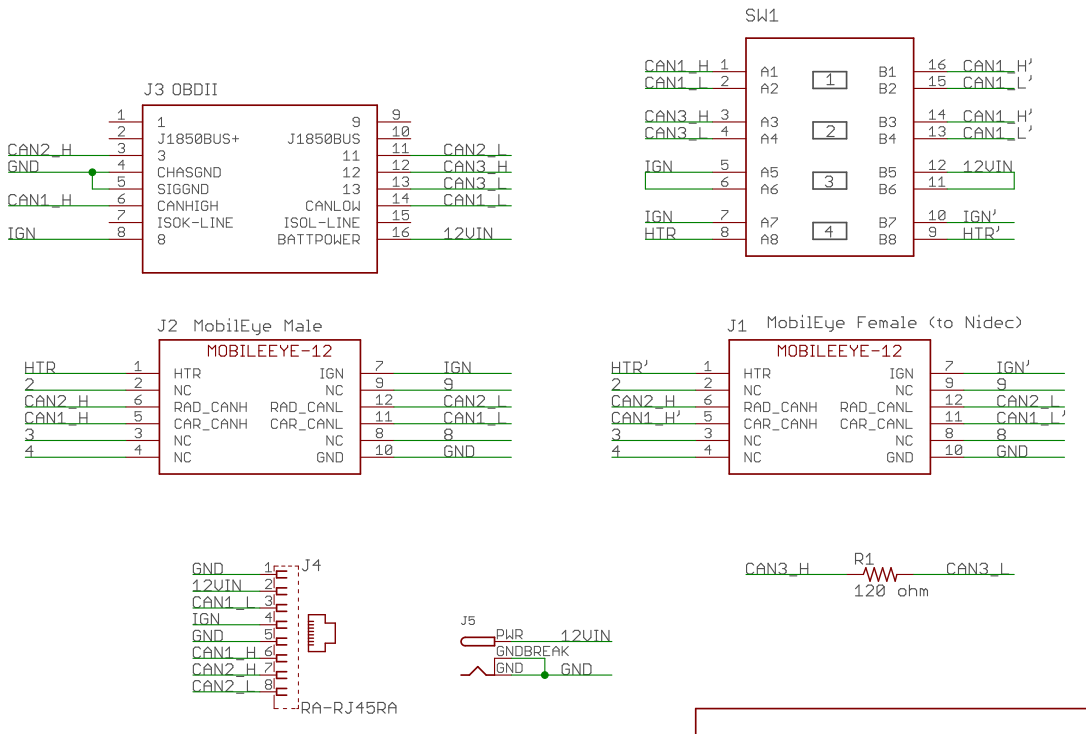
[picture p98: page 1]
