commaai/neo/giraffe/subaru/comma_access_point.sch.pdf

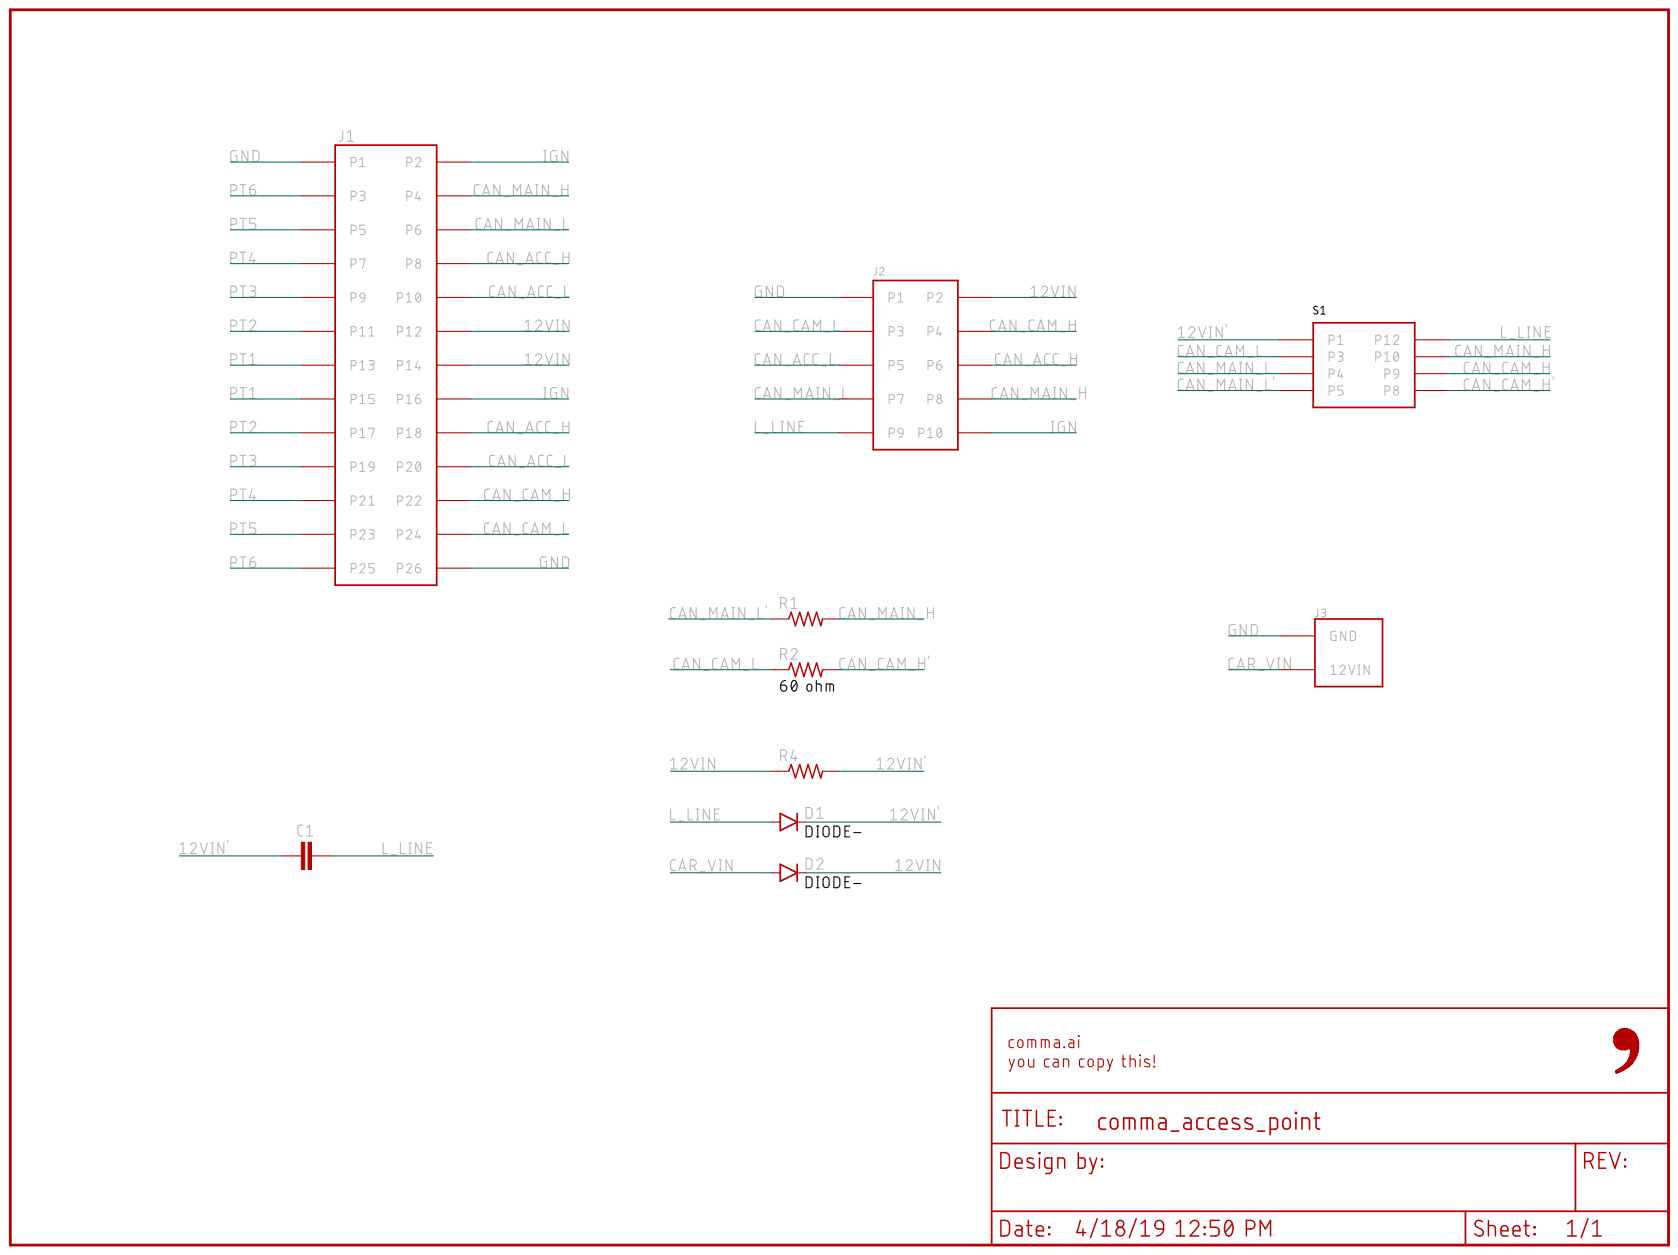
[picture p99: page 1]
