commaai/neo/giraffe/subaru/panda_interface_point.sch.pdf

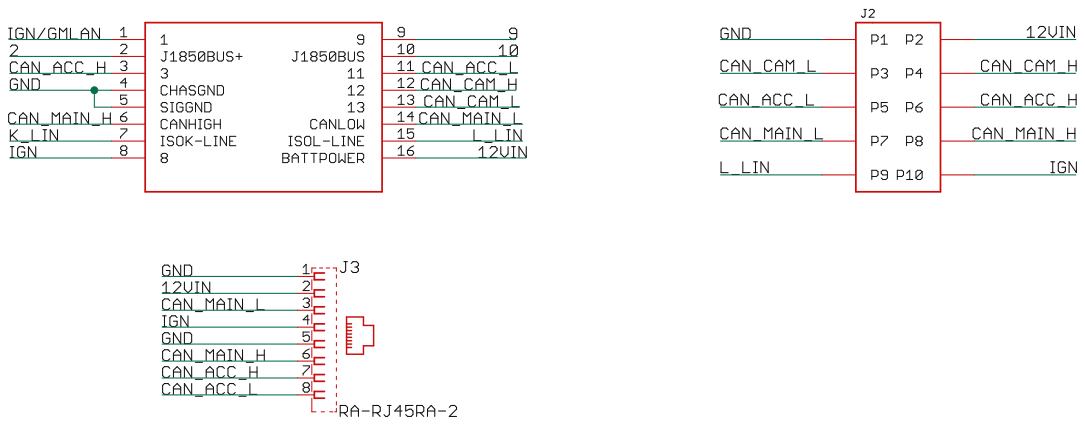
[picture p100: page 1]
