commaai/neo/giraffe/subaru/Subaru_Car_Harness.sch.pdf

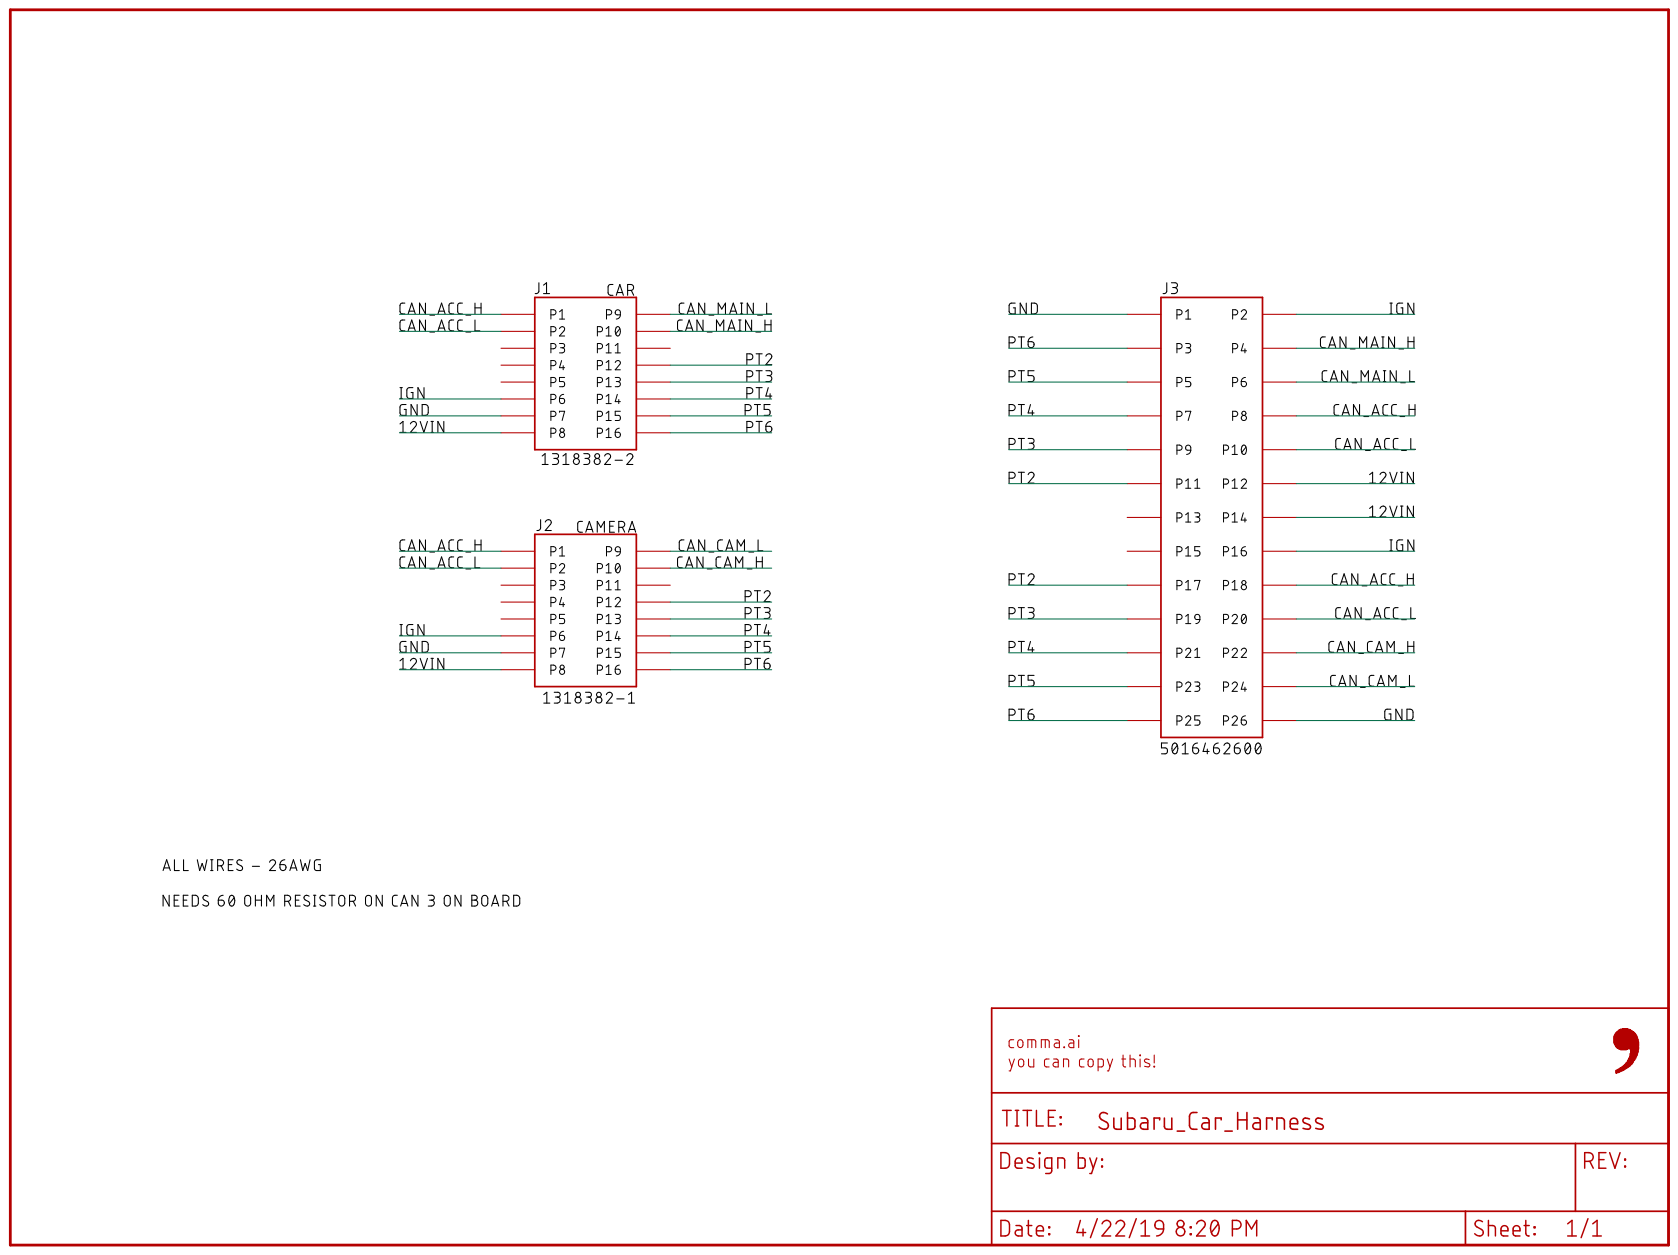
[picture p101: page 1]
