commaai/neo/giraffe/subaru/Ten_Pin_Harness.sch.pdf

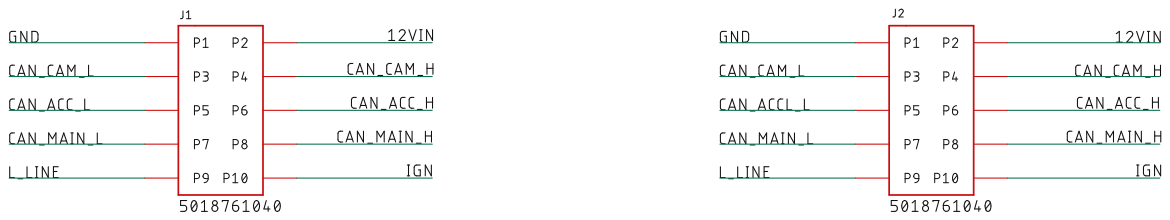
[picture p102: page 1]
