commaai/neo/giraffe/hyundai/Hyundai_Giraffe.sch.pdf

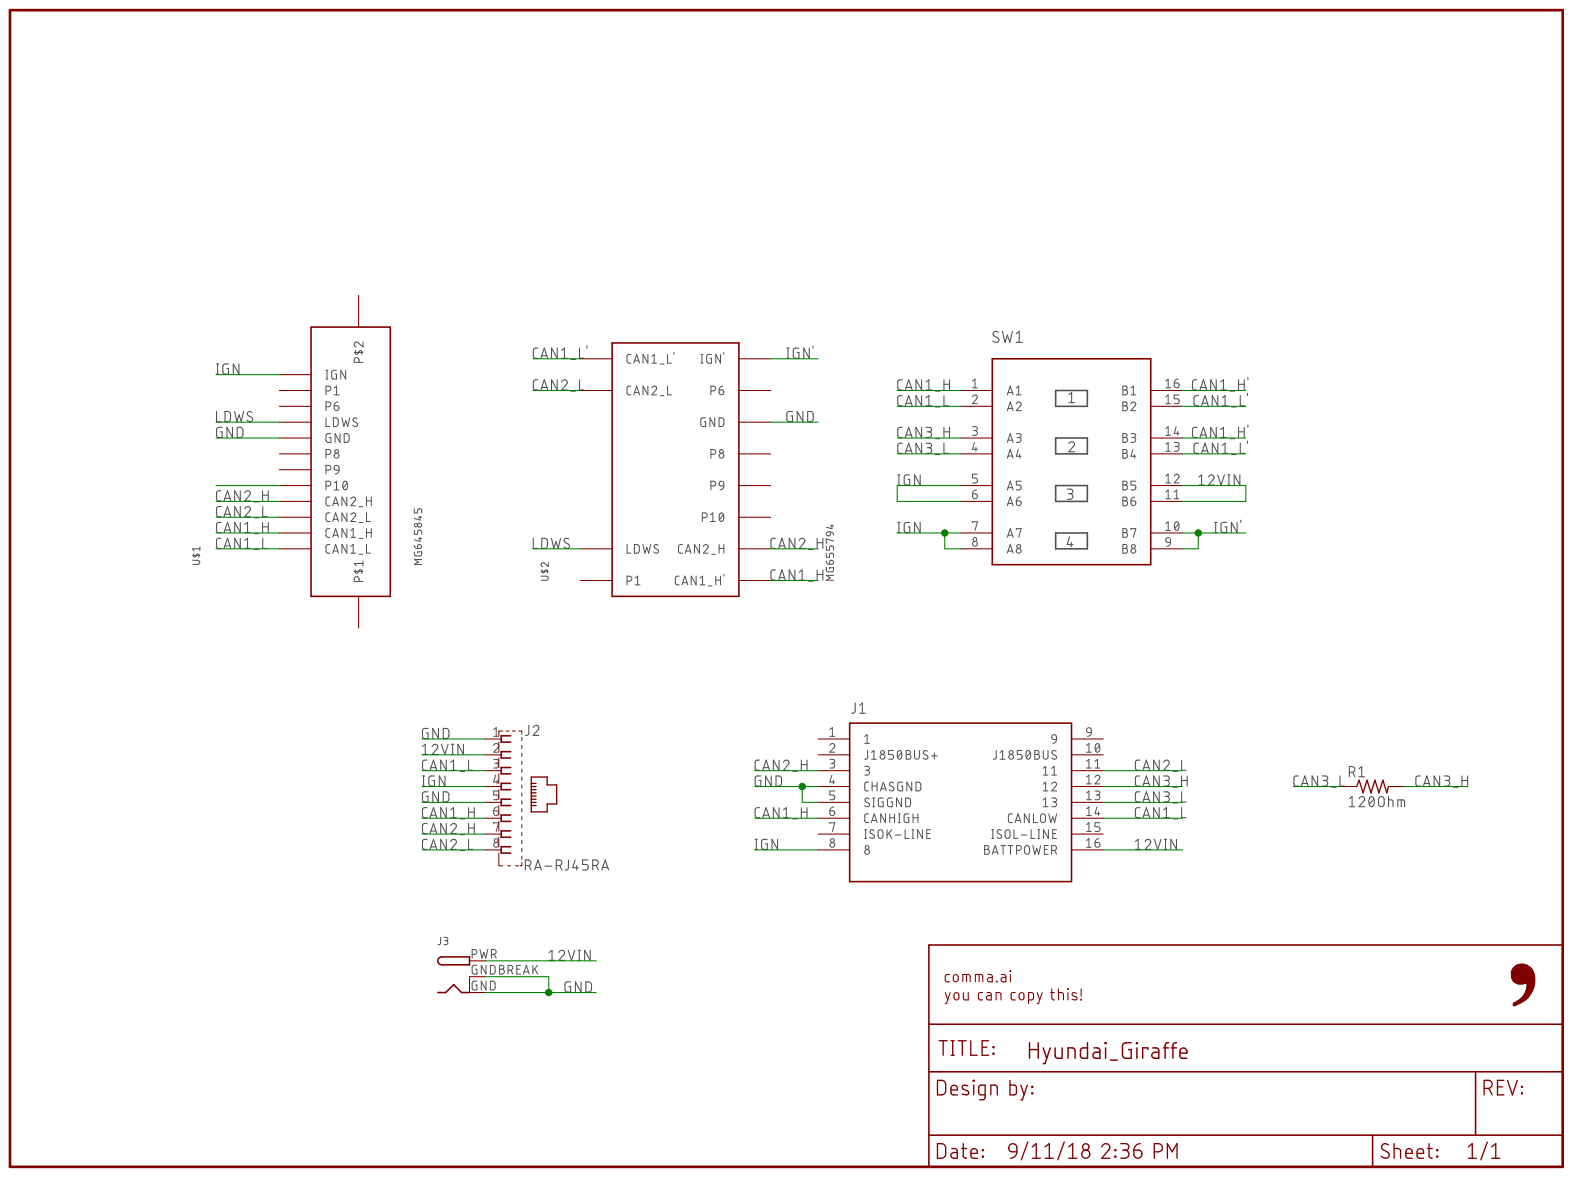
[picture p103: page 1]
