commaai/neo/giraffe/ford/ford_giraffe.sch.pdf

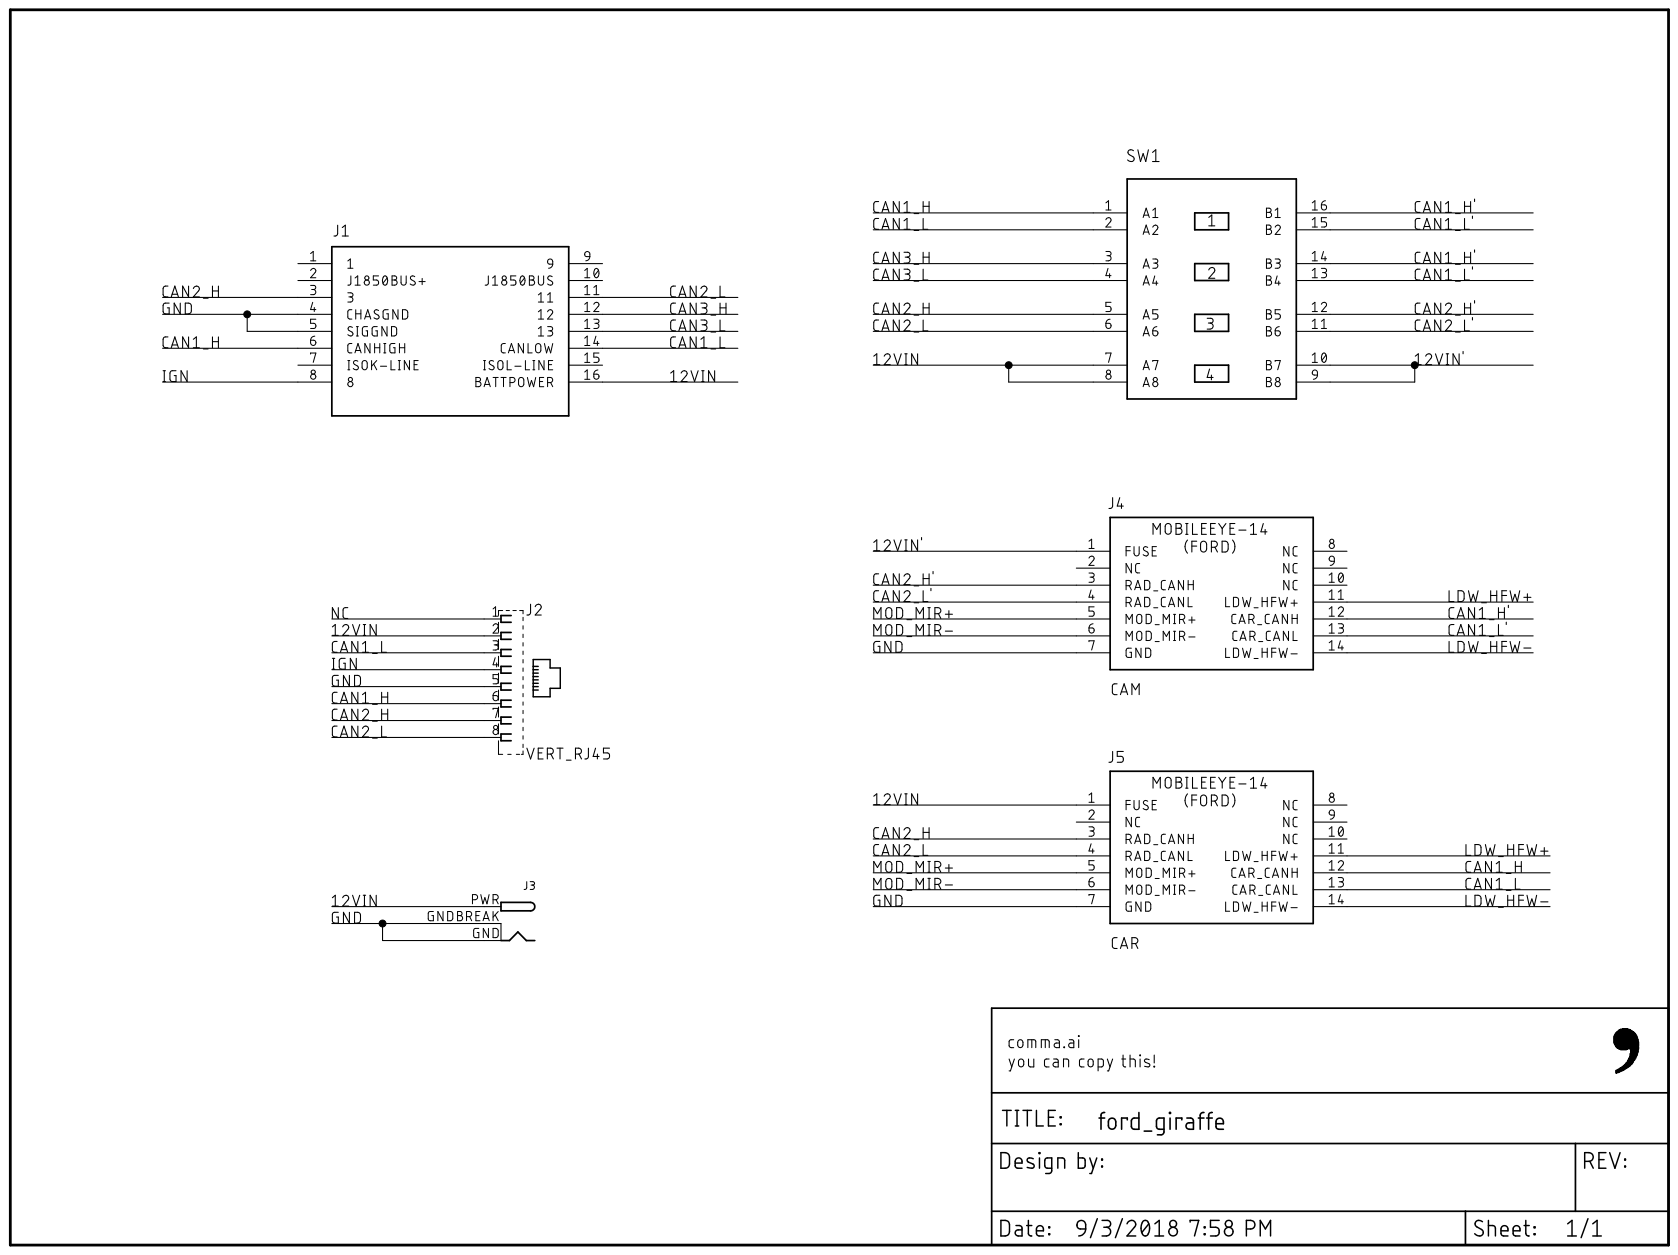
[picture p104: page 1]
