commaai/neo/pedal/board/interceptor.sch.pdf

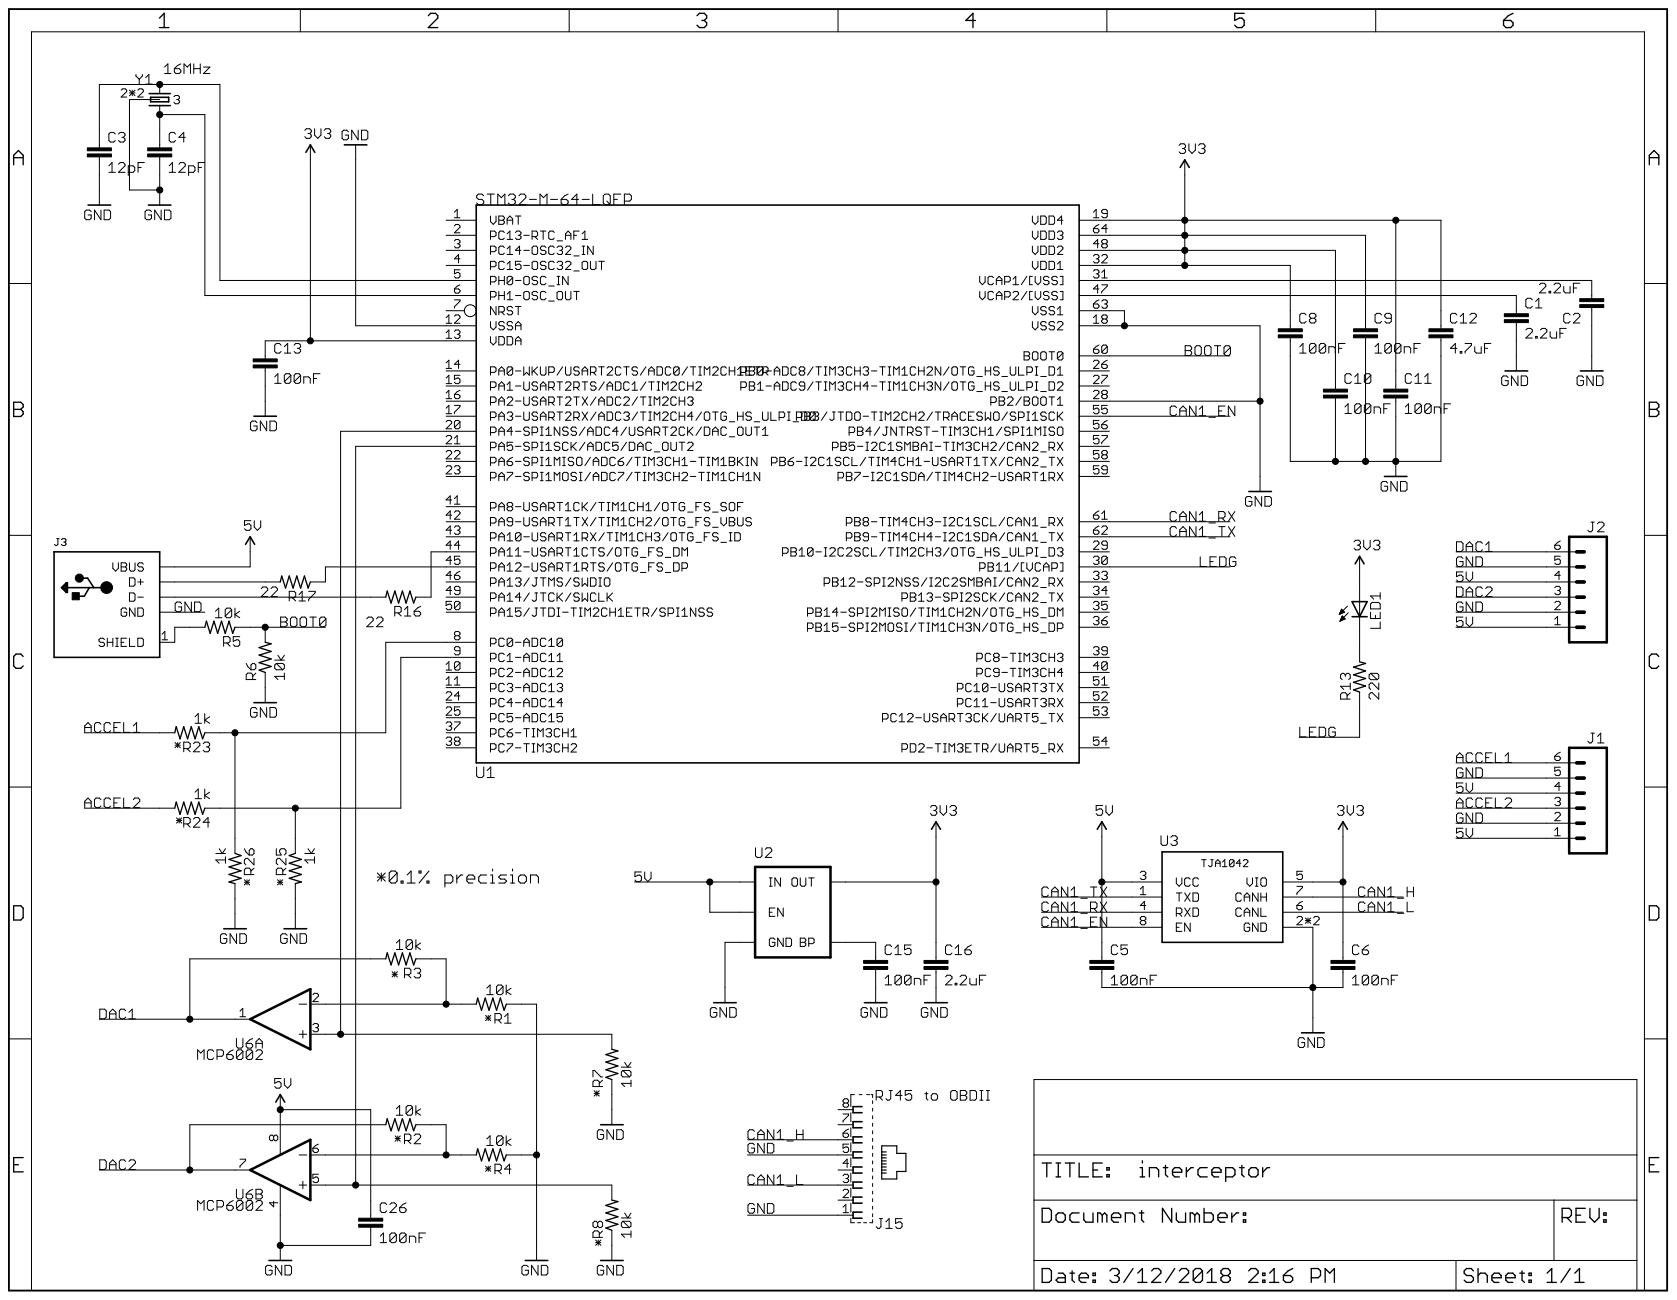
[picture p105: page 1]
