commaai/neo/giraffe/honda/nidec_inverted/giraffe20_inverted.sch.pdf

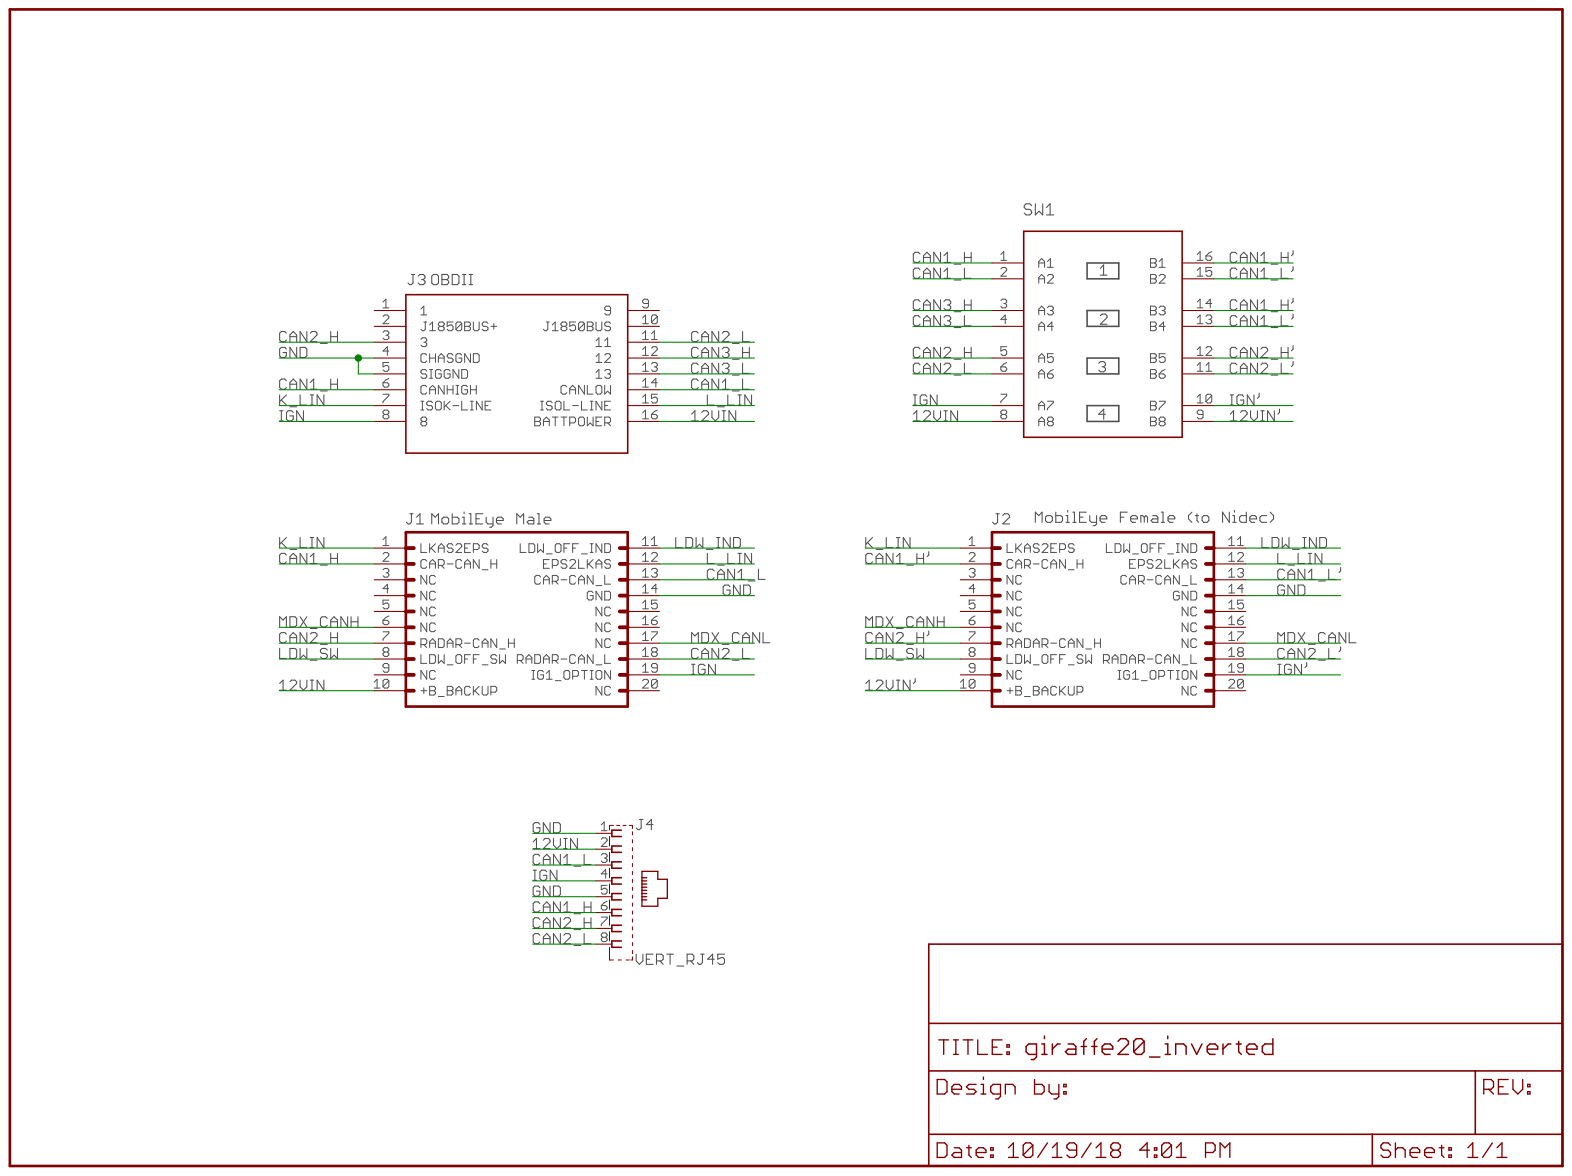
[picture p106: page 1]
