commaai/neo/giraffe/honda/bosch/giraffe_bosch_comma.sch.pdf

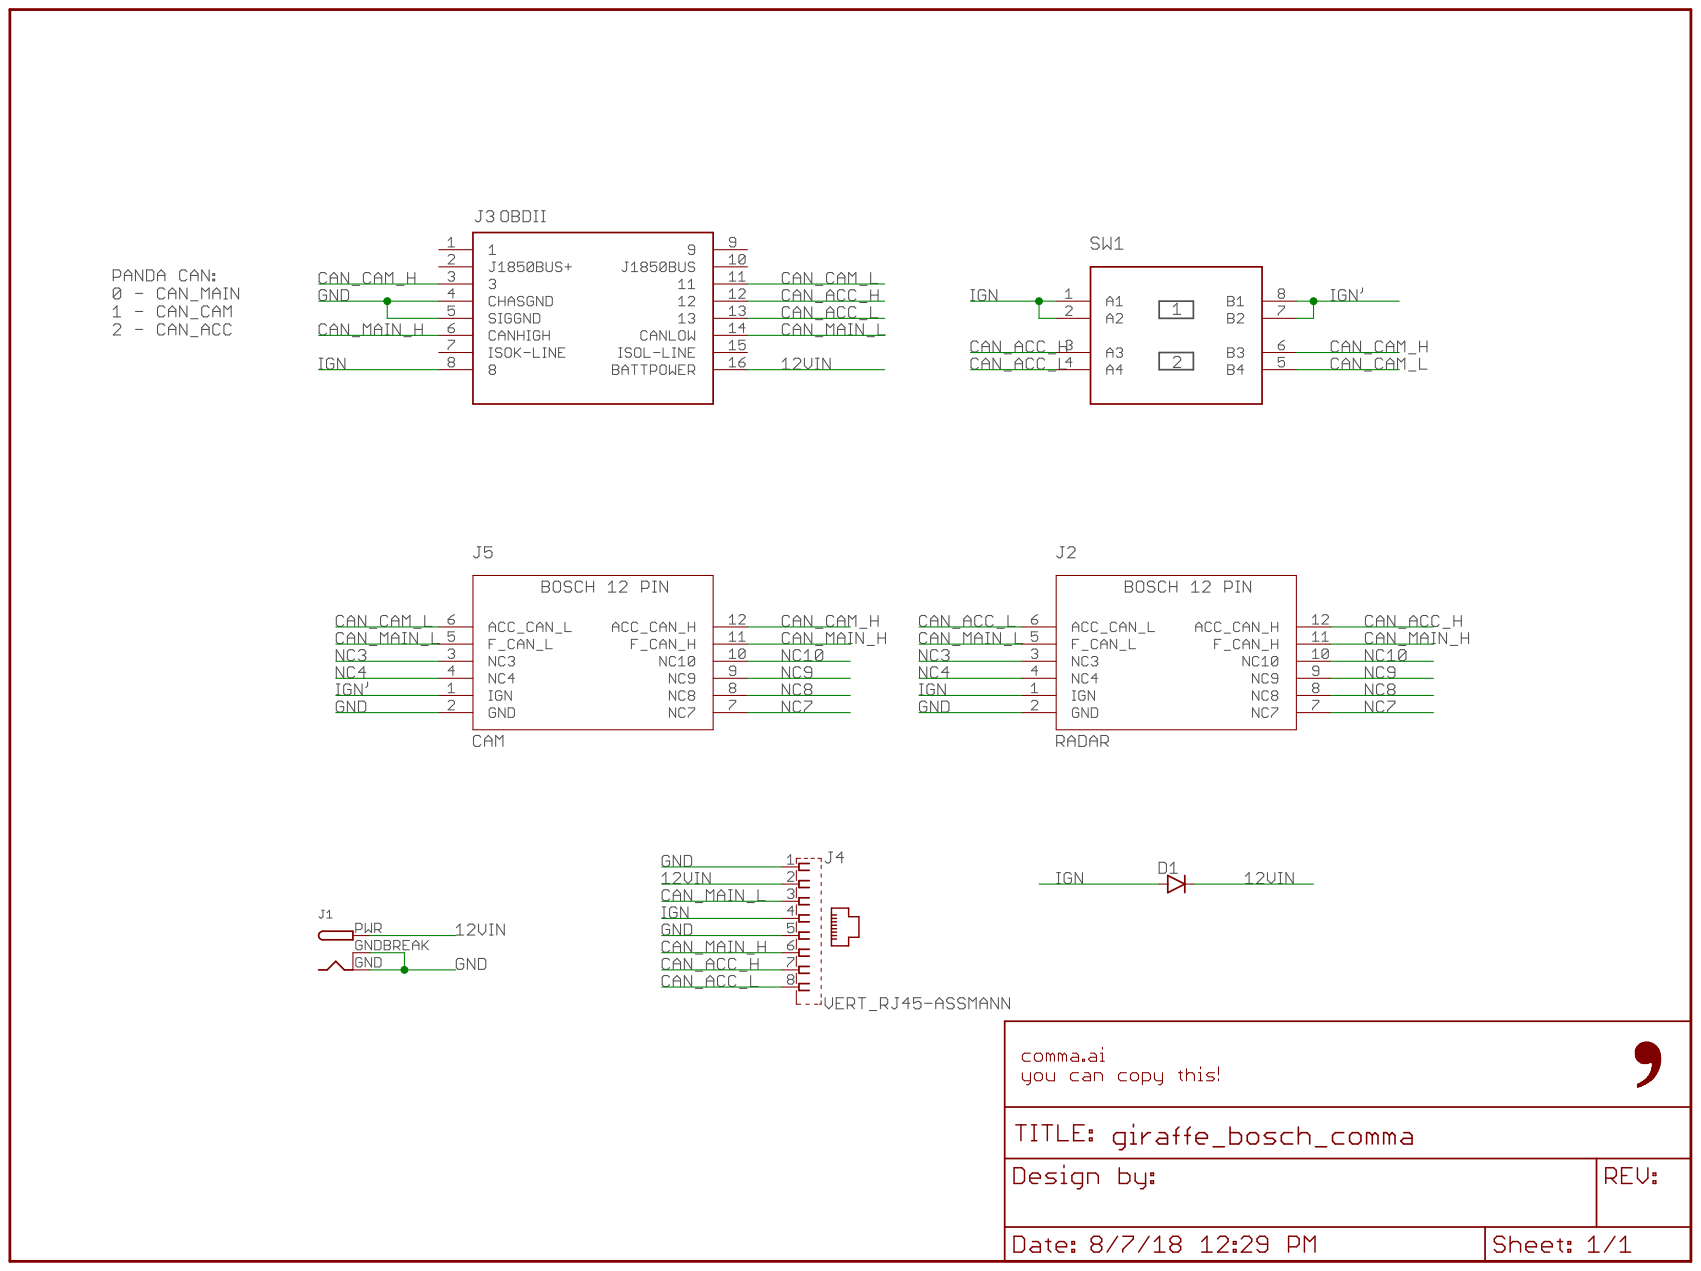
[picture p107: page 1]
