commaai/neo/car_harness/v1/J533_Harness.pdf

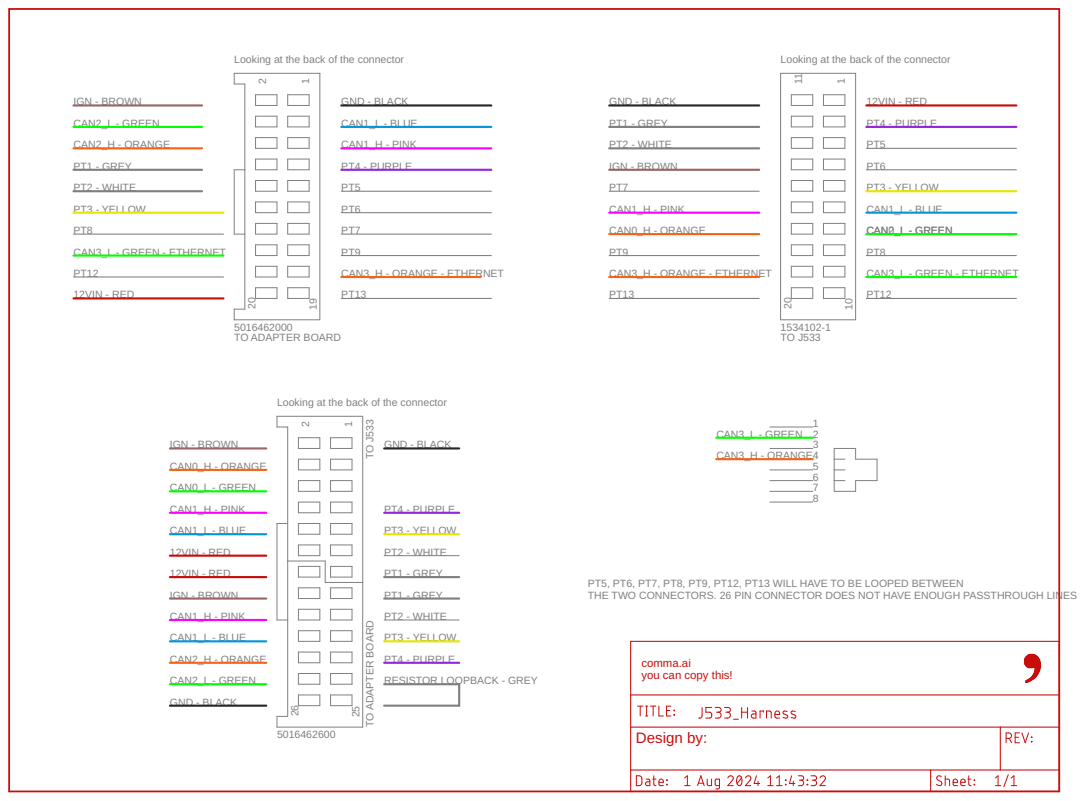
[picture p108: page 1]
GND - BLACK; PT4 - PURPLE; PT3 - YELLOW; 26 PT4 - PURPLE; IGN - BROWN; CAN1_L - BLUE; CAN0_L - GREEN; CAN2_L - GREEN; CAN0_H - ORANGE; CAN2_H - ORANGE; CAN1_H - PINK; PT1 - GREY; PT2 - WHITE; ADAPTER BO; ARD TO J533; 12VIN - RED; Looking at the back of the connector; CAN3_H - ORANGE - ETHERNET; CAN3_L - GREEN - ETHERNET; CAN3_L - GREEN; CAN3_H - ORANGE; Design by:

20 TO ADAPTER BOARD

Looking at the back of the connector

PT5, PT6, PT7, PT8, PT9, PT12, PT13 WILL HAVE TO BE LOOPED BETWEEN
THE TWO CONNECTORS. 26 PIN CONNECTOR DOES NOT HAVE ENOUGH PASSTHROUGH LINES

comma.ai
you can copy this!

RESISTOR LOOPBACK - GREY
