commaai/neo/car_harness/v1/RAM_Harness.sch.pdf

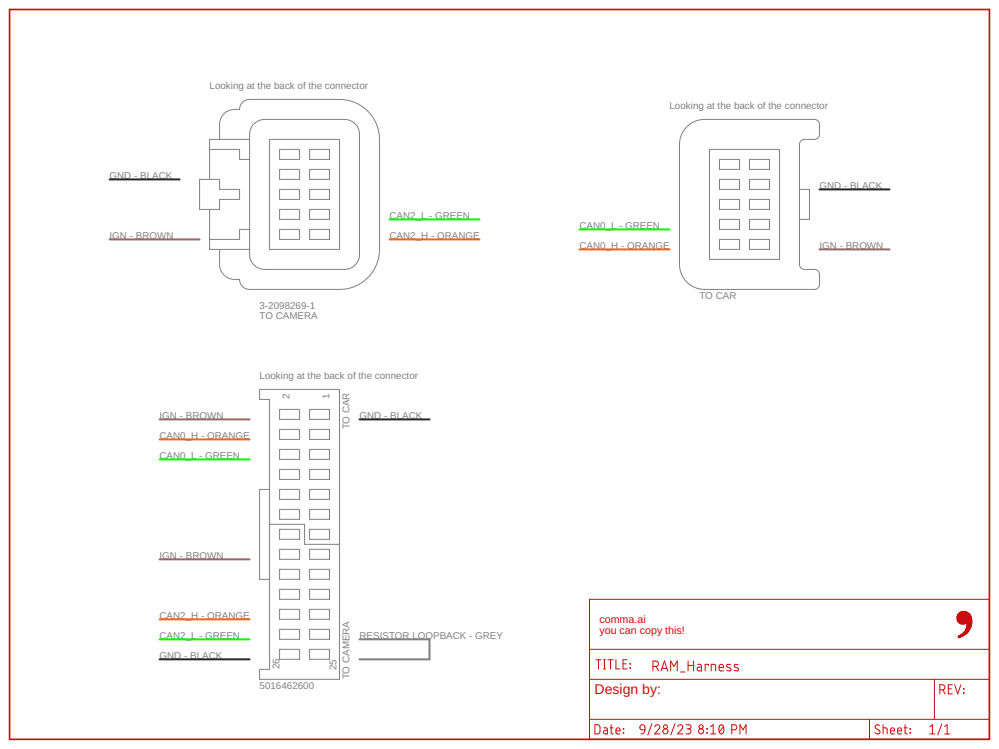
[picture p109: page 1]

Looking at the back of the connector

comma.ai
you can copy this!
