commaai/neo/car_harness/v1/open_pinout.sch.pdf

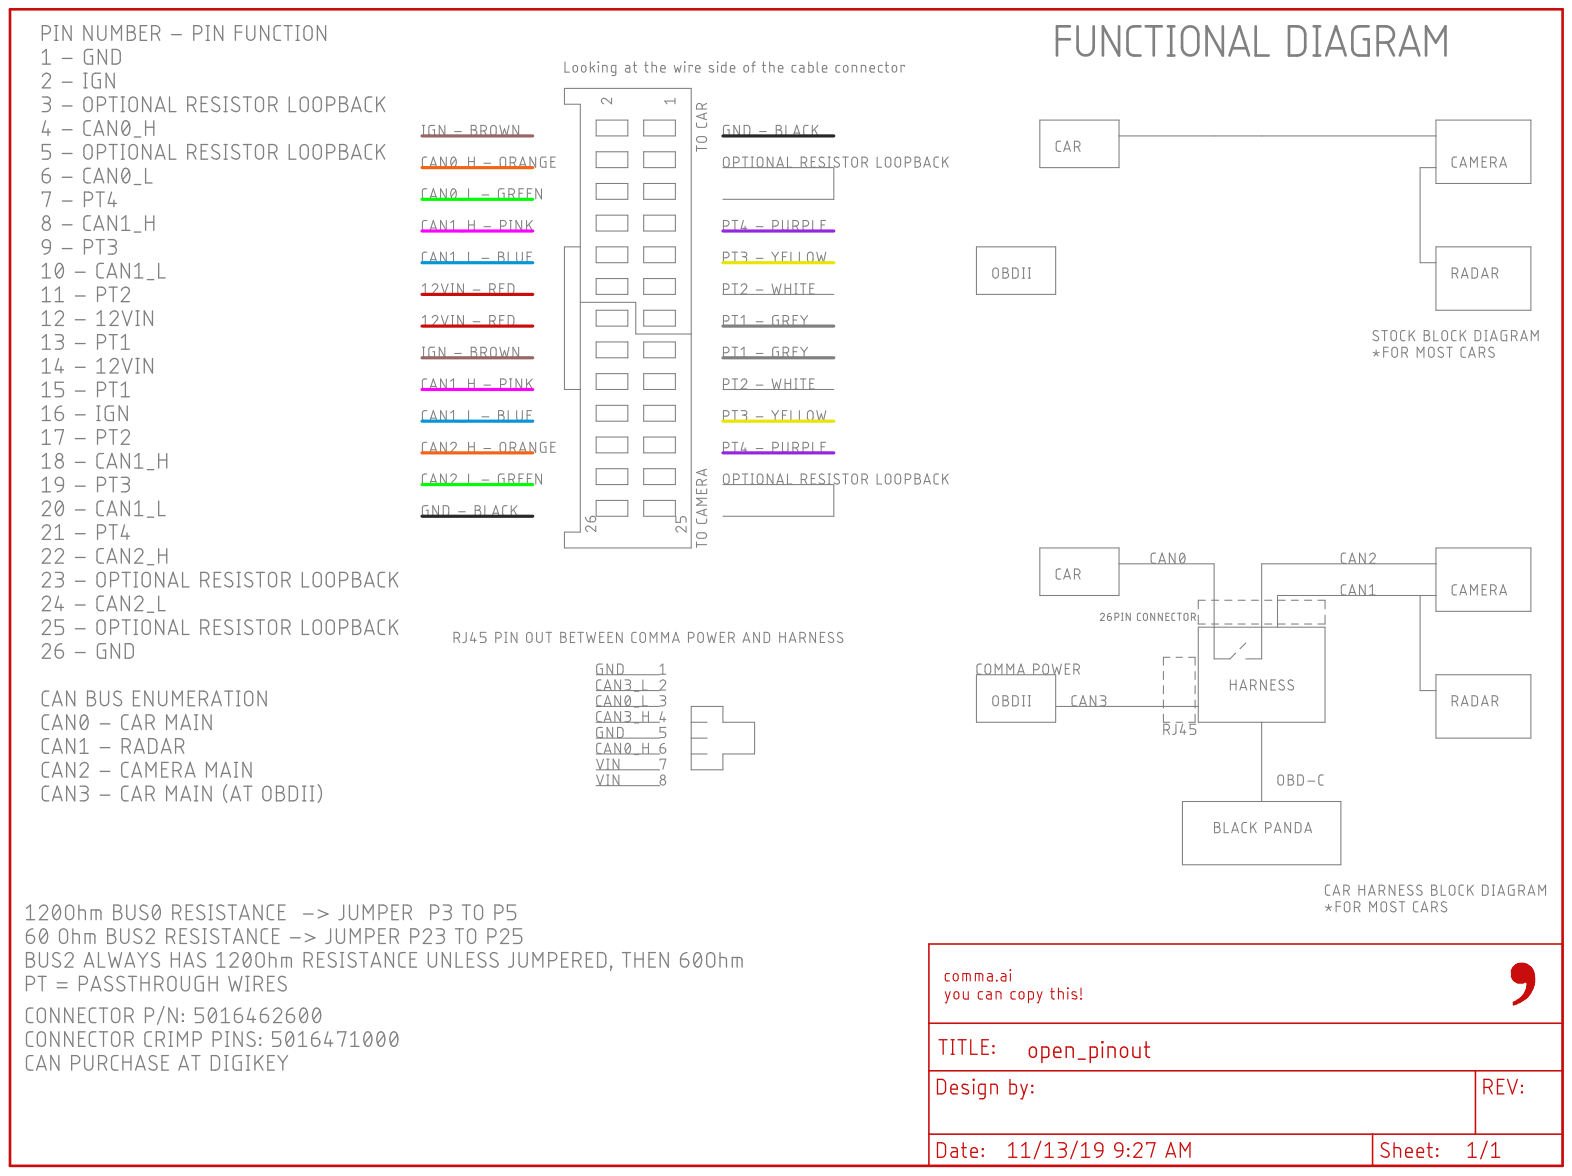
[picture p110: page 1]
