commaai/neo/car_harness/v1/Subaru_D_Harness.sch.pdf

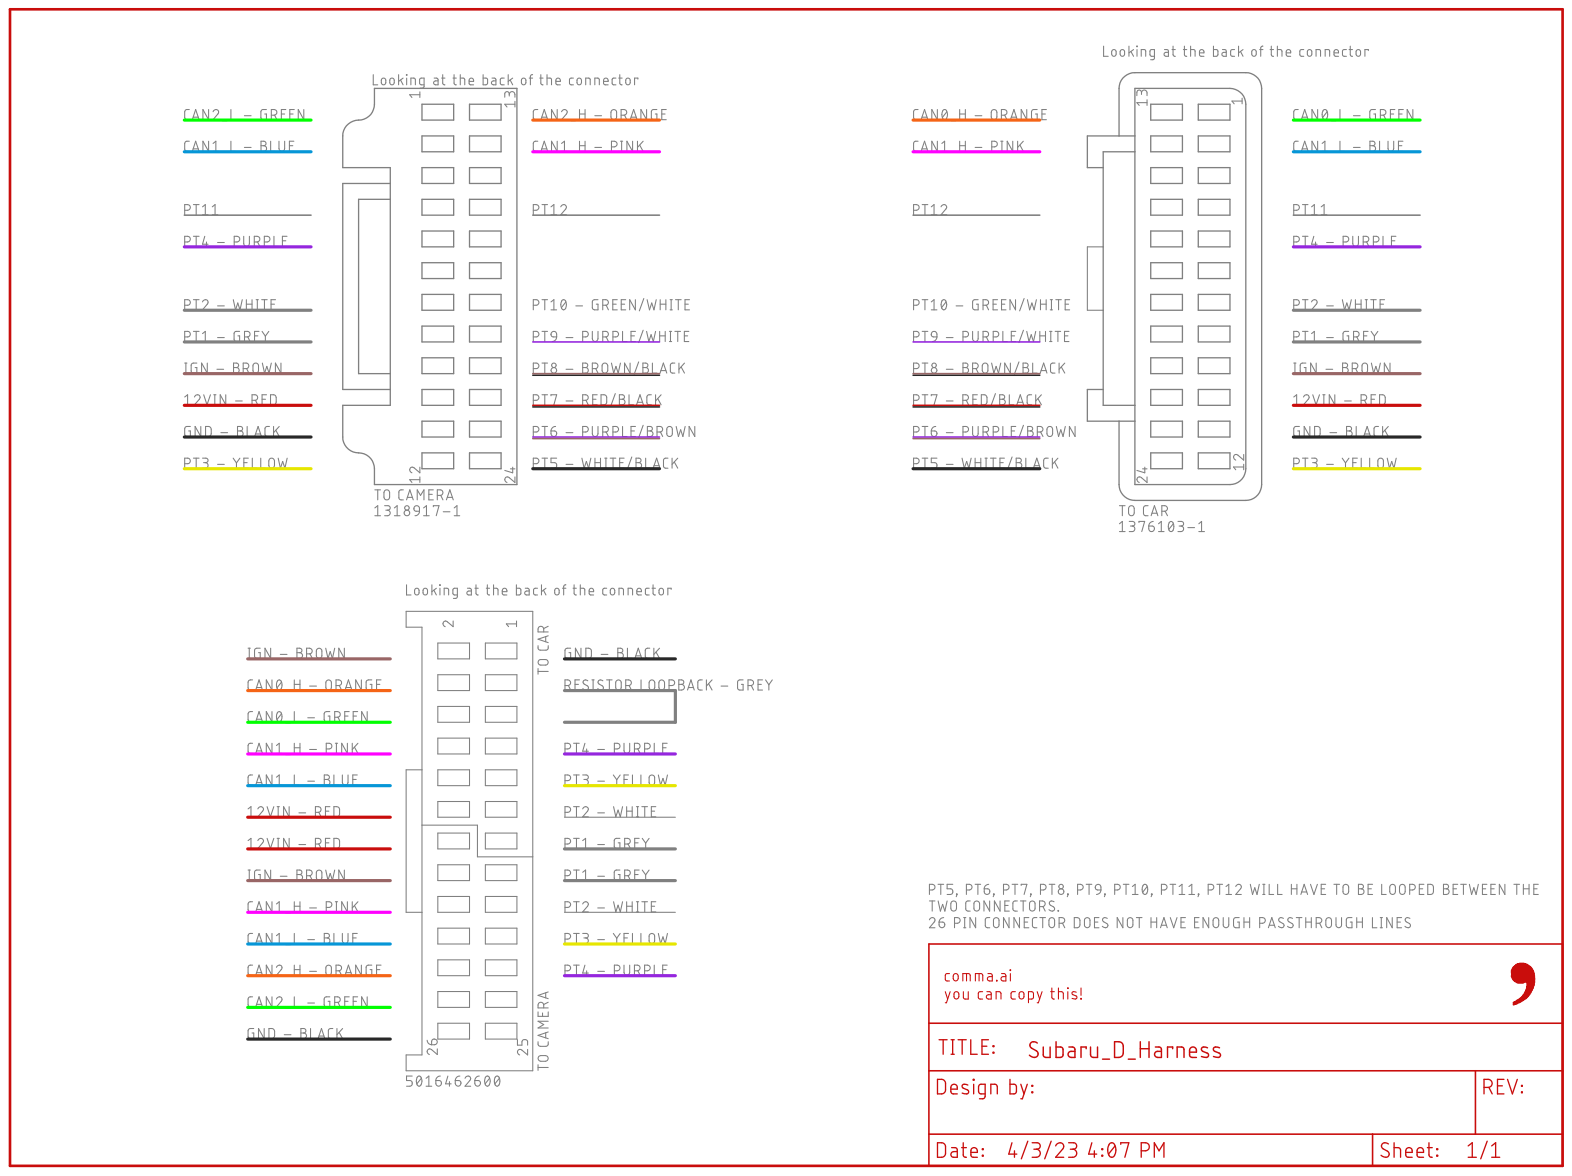
[picture p111: page 1]
