commaai/neo/car_harness/v1/Toyota_B_Harness.sch.pdf

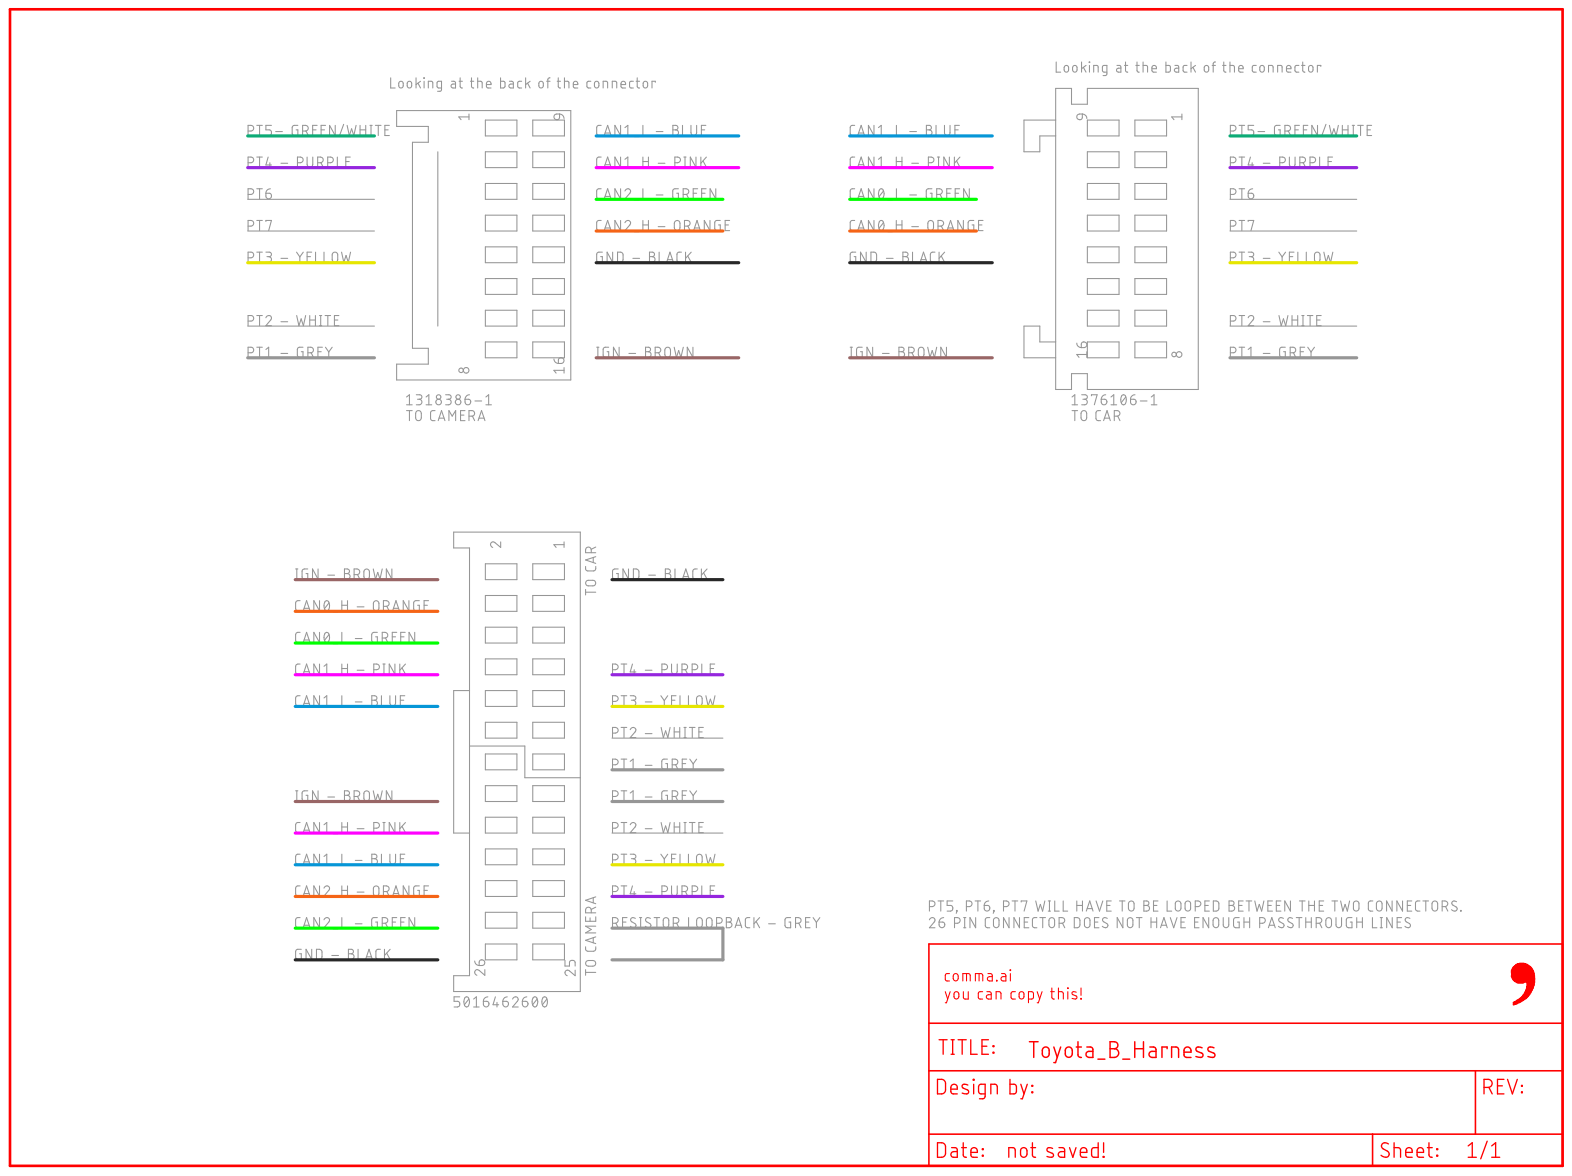
[picture p112: page 1]
