commaai/neo/car_harness/v1/Toyota_A_Harness.sch.pdf

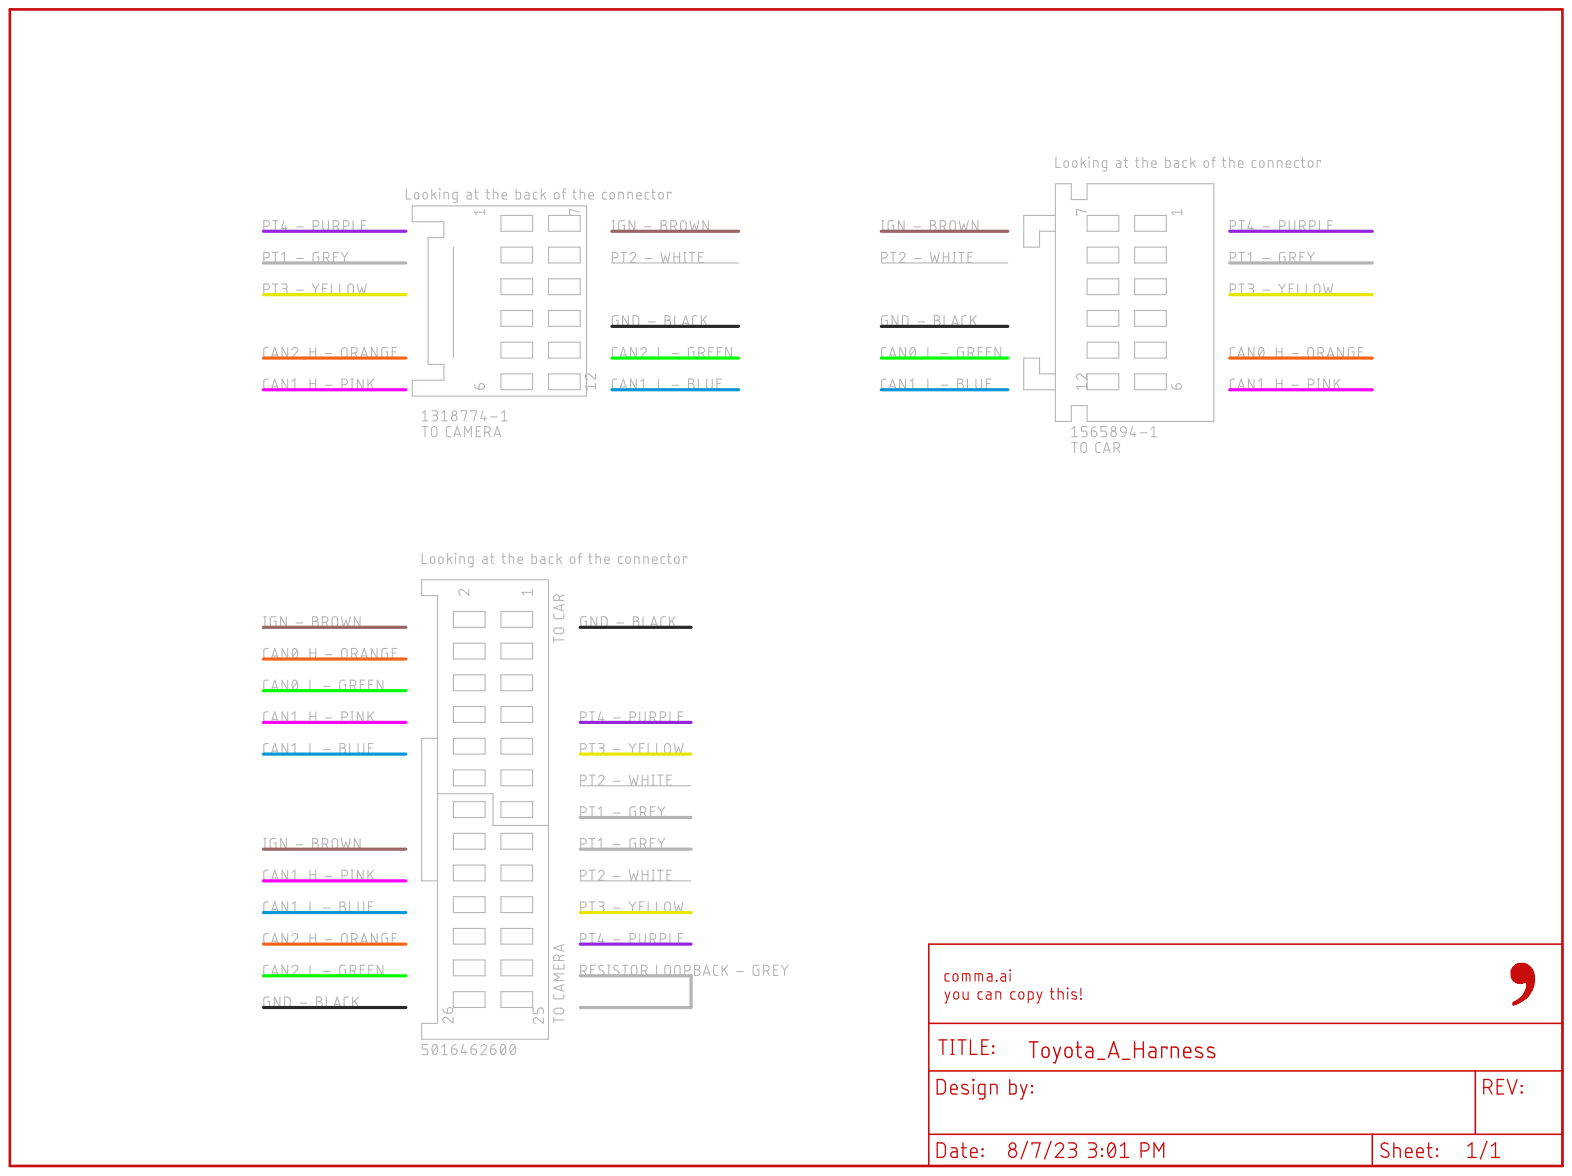
[picture p113: page 1]
