commaai/neo/car_harness/v1/Ford_Q4_Harness.sch.pdf

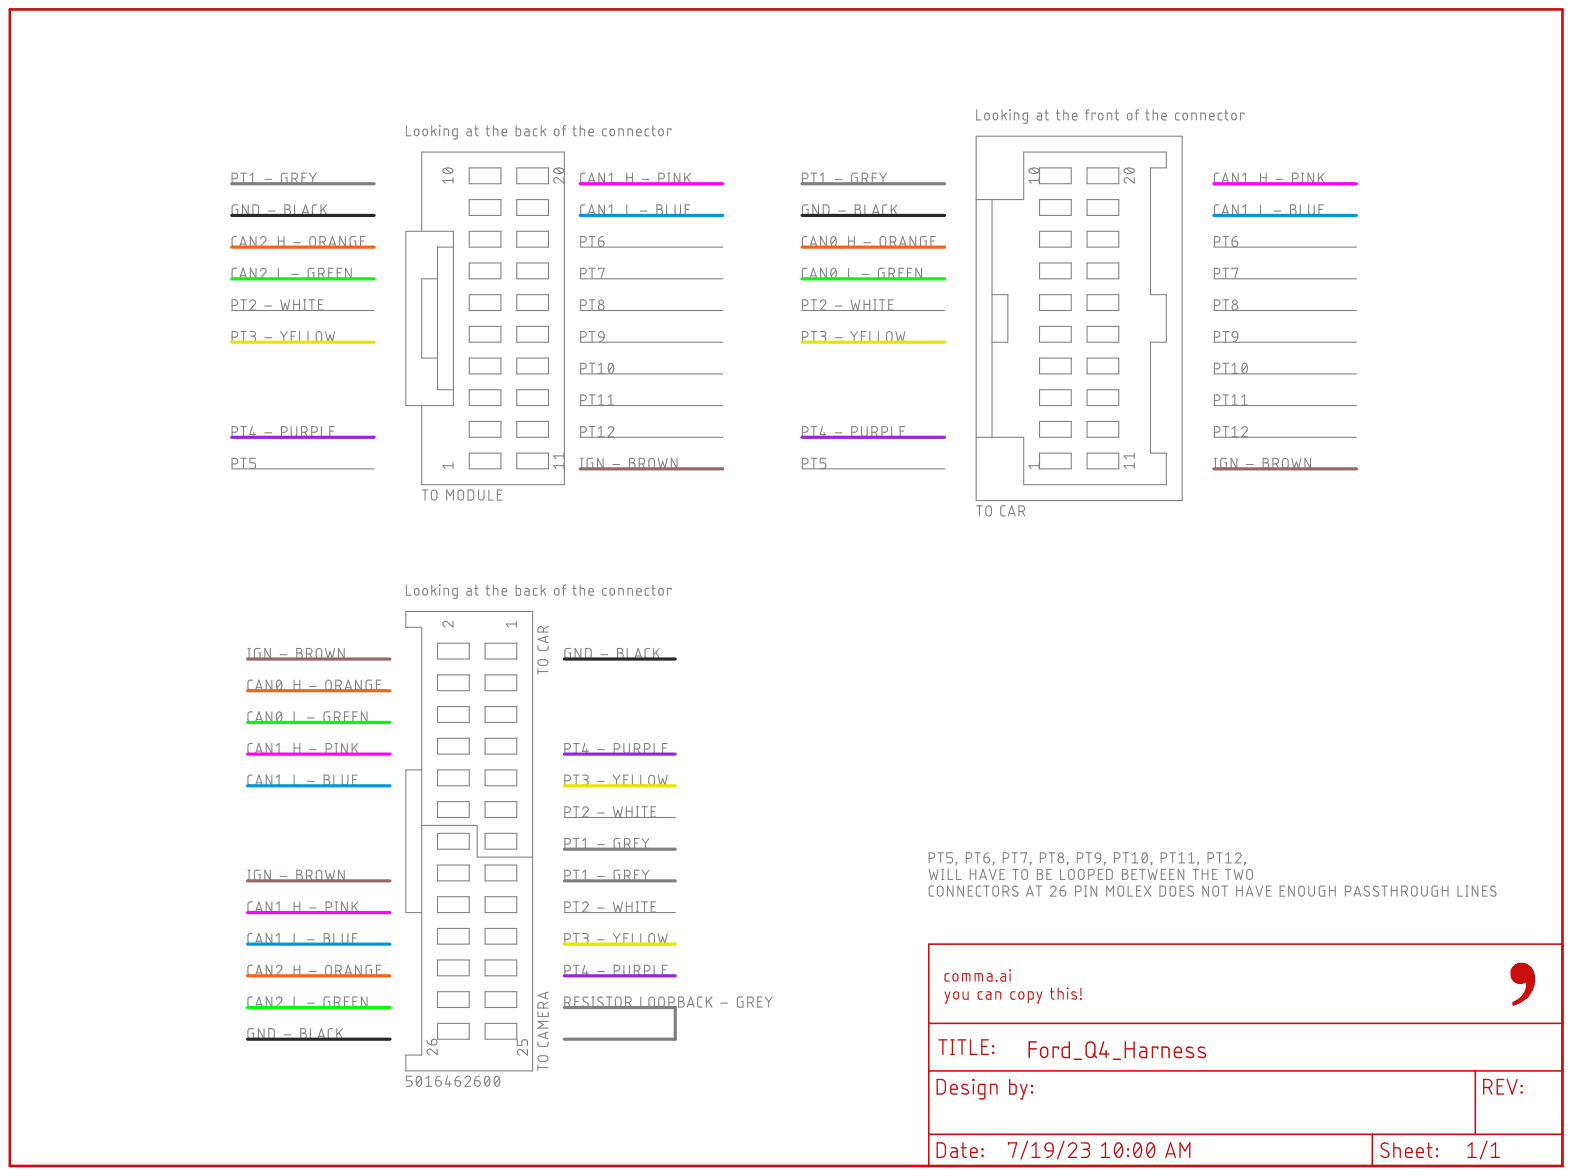
[picture p114: page 1]
