commaai/neo/car_harness/v1/Mazda_Harness.sch.pdf

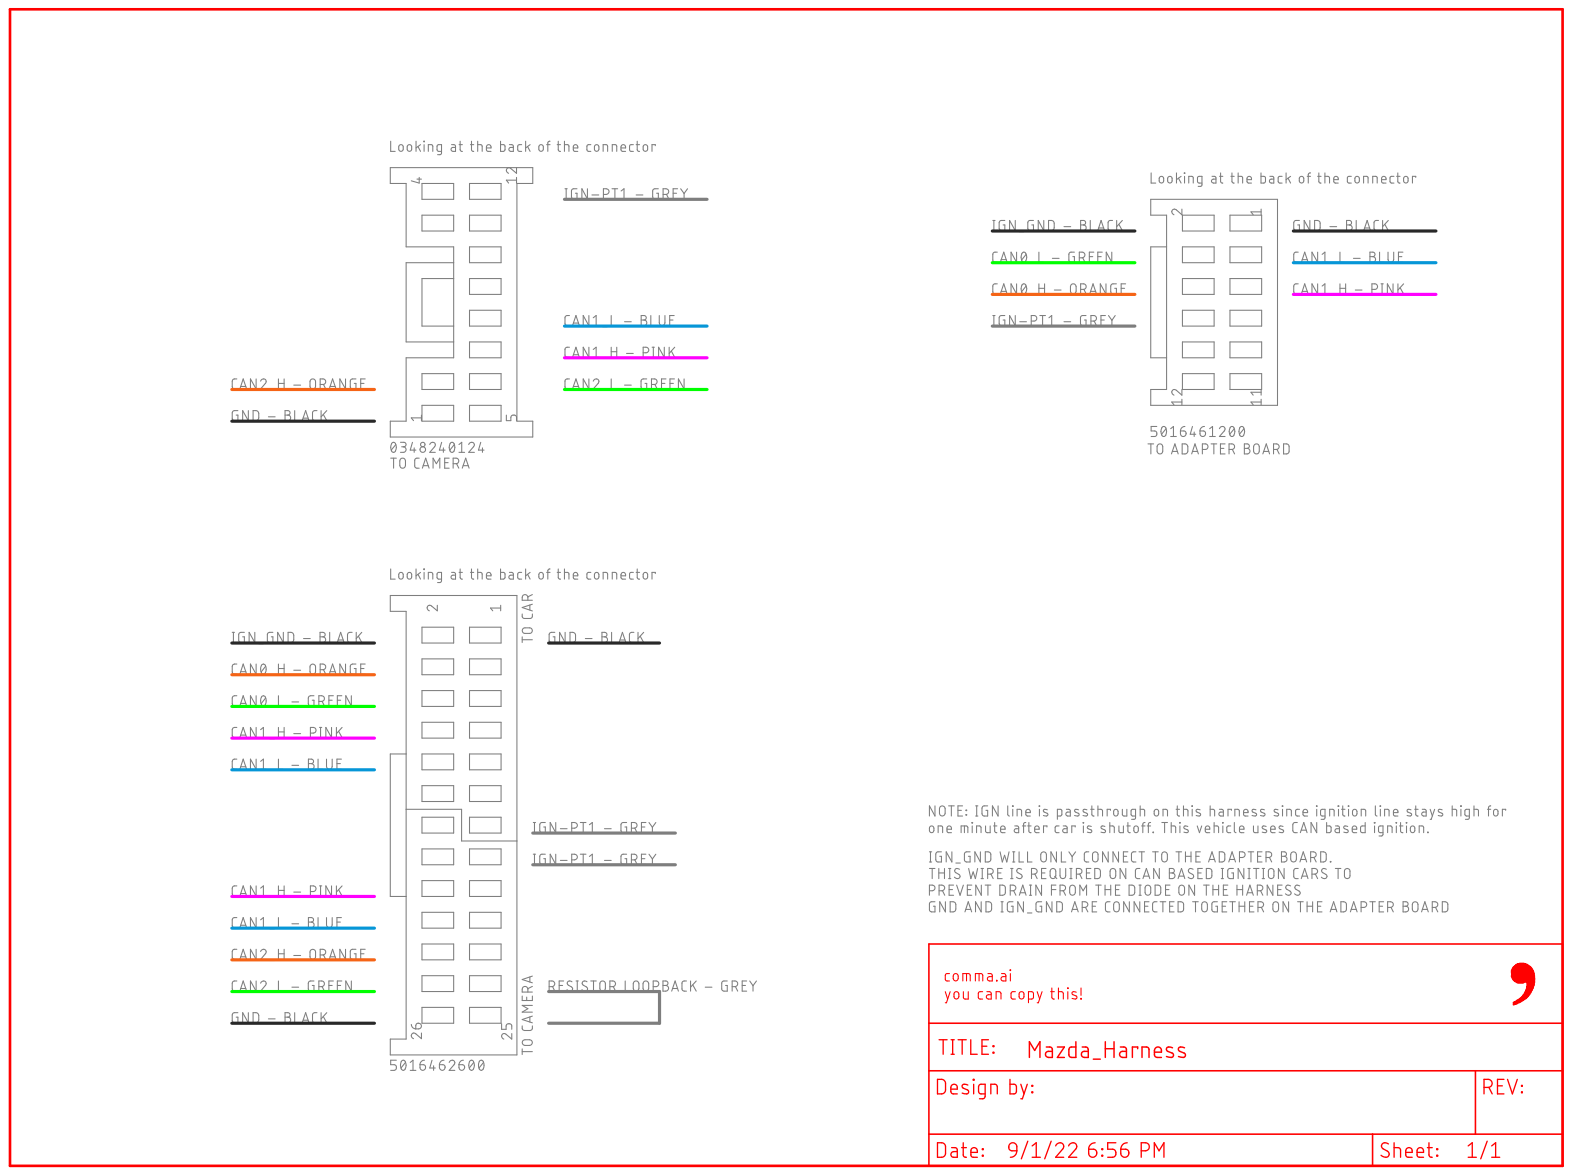
[picture p115: page 1]
