commaai/neo/car_harness/v1/Subaru_A_Harness.sch.pdf

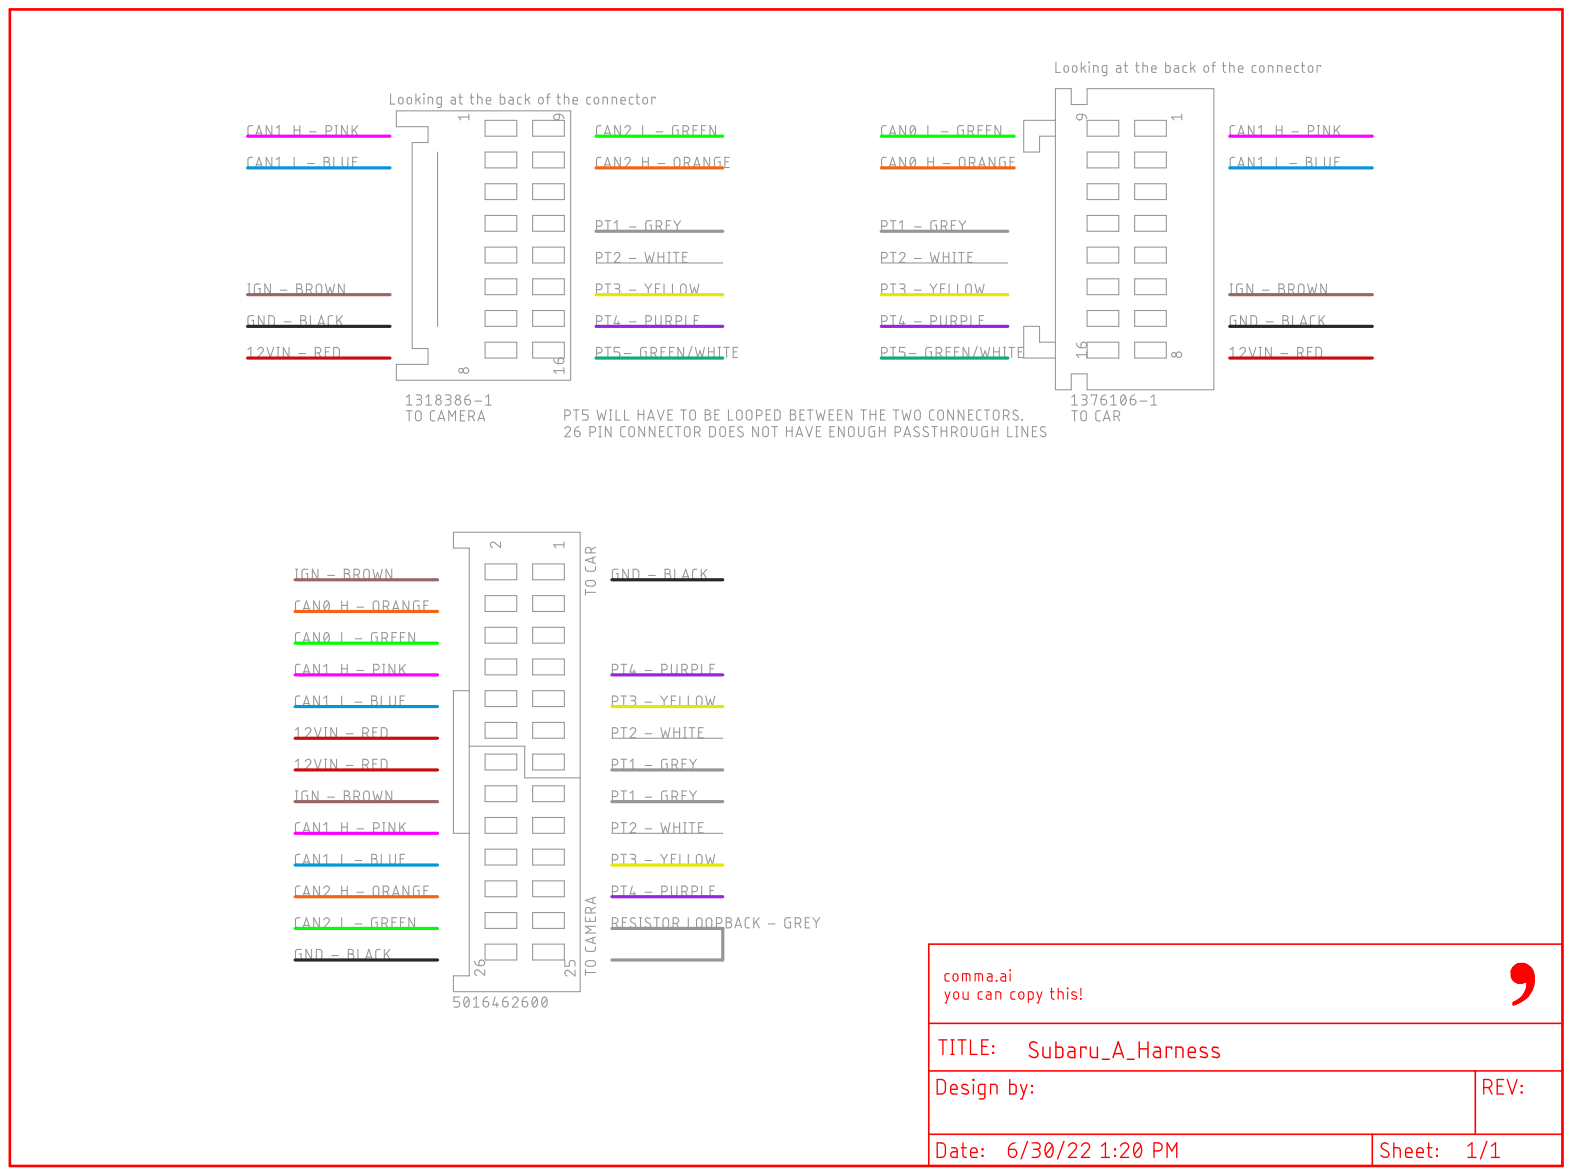
[picture p116: page 1]
