commaai/neo/car_harness/v1/Subaru_B_Harness.sch.pdf

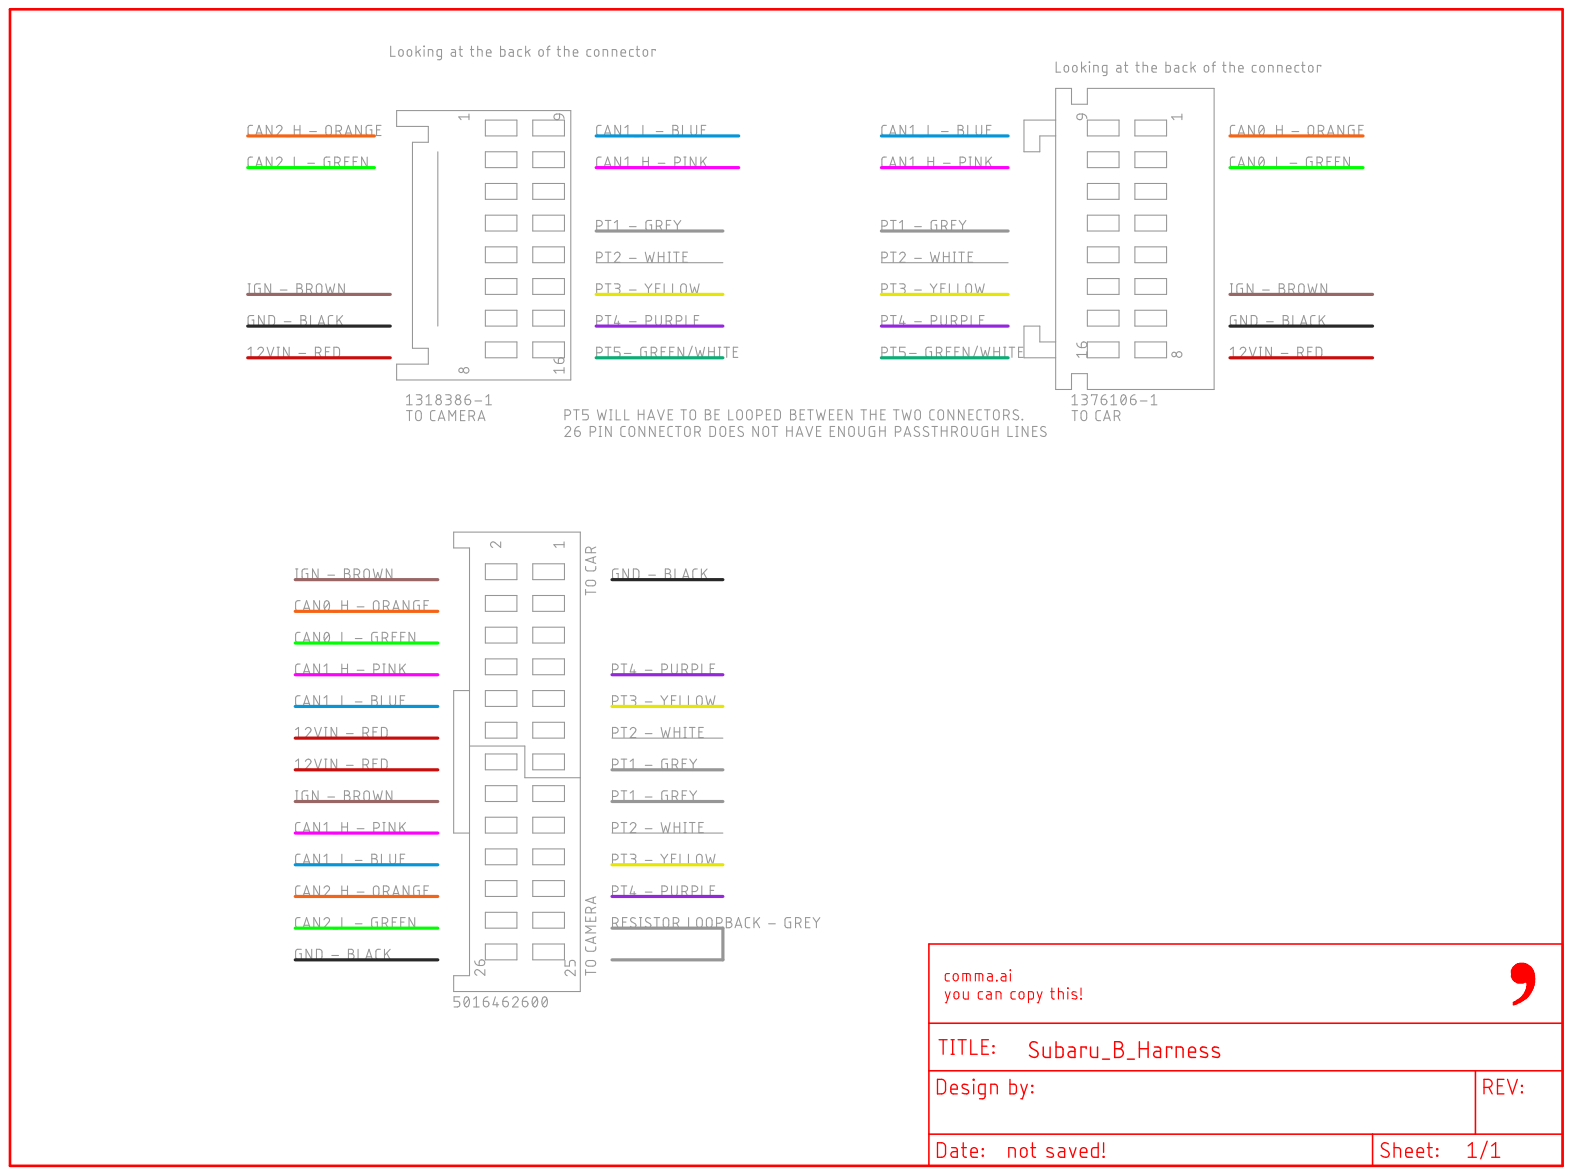
[picture p117: page 1]
