commaai/neo/car_harness/v1/Subaru_C_Harness.sch.pdf

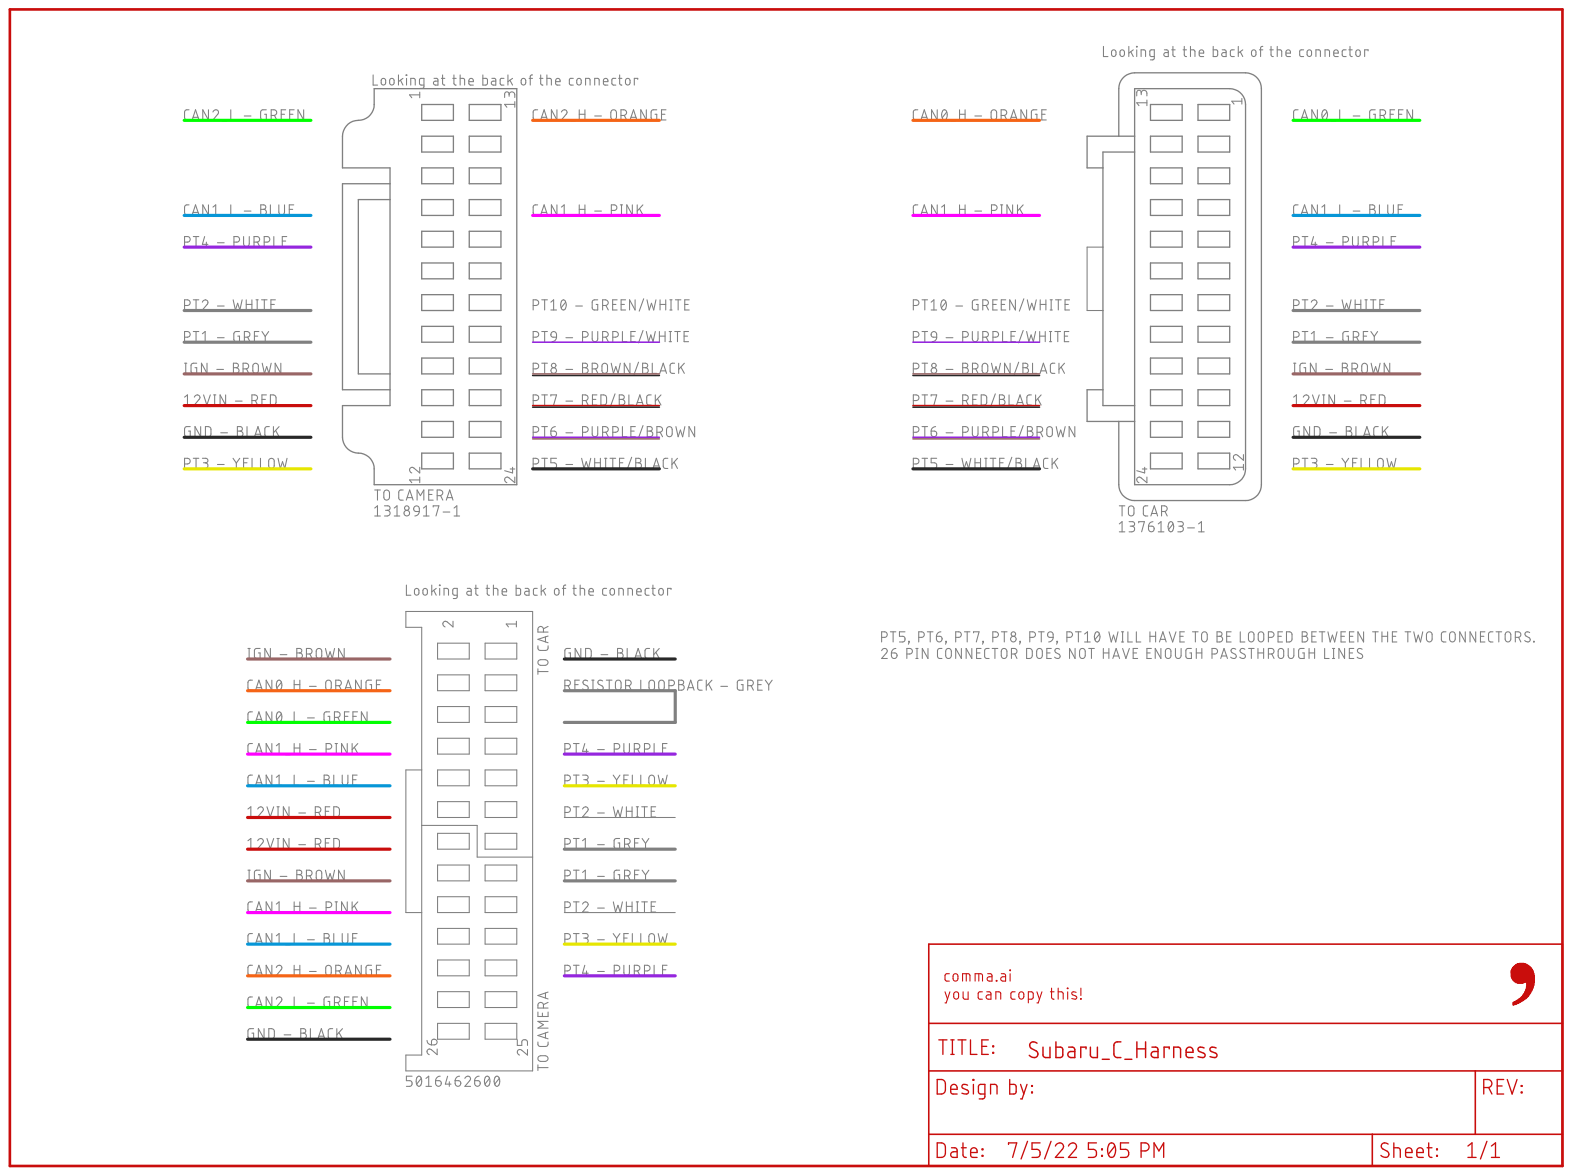
[picture p118: page 1]
