commaai/neo/car_harness/v1/Ford_Q3_Harness.sch.pdf

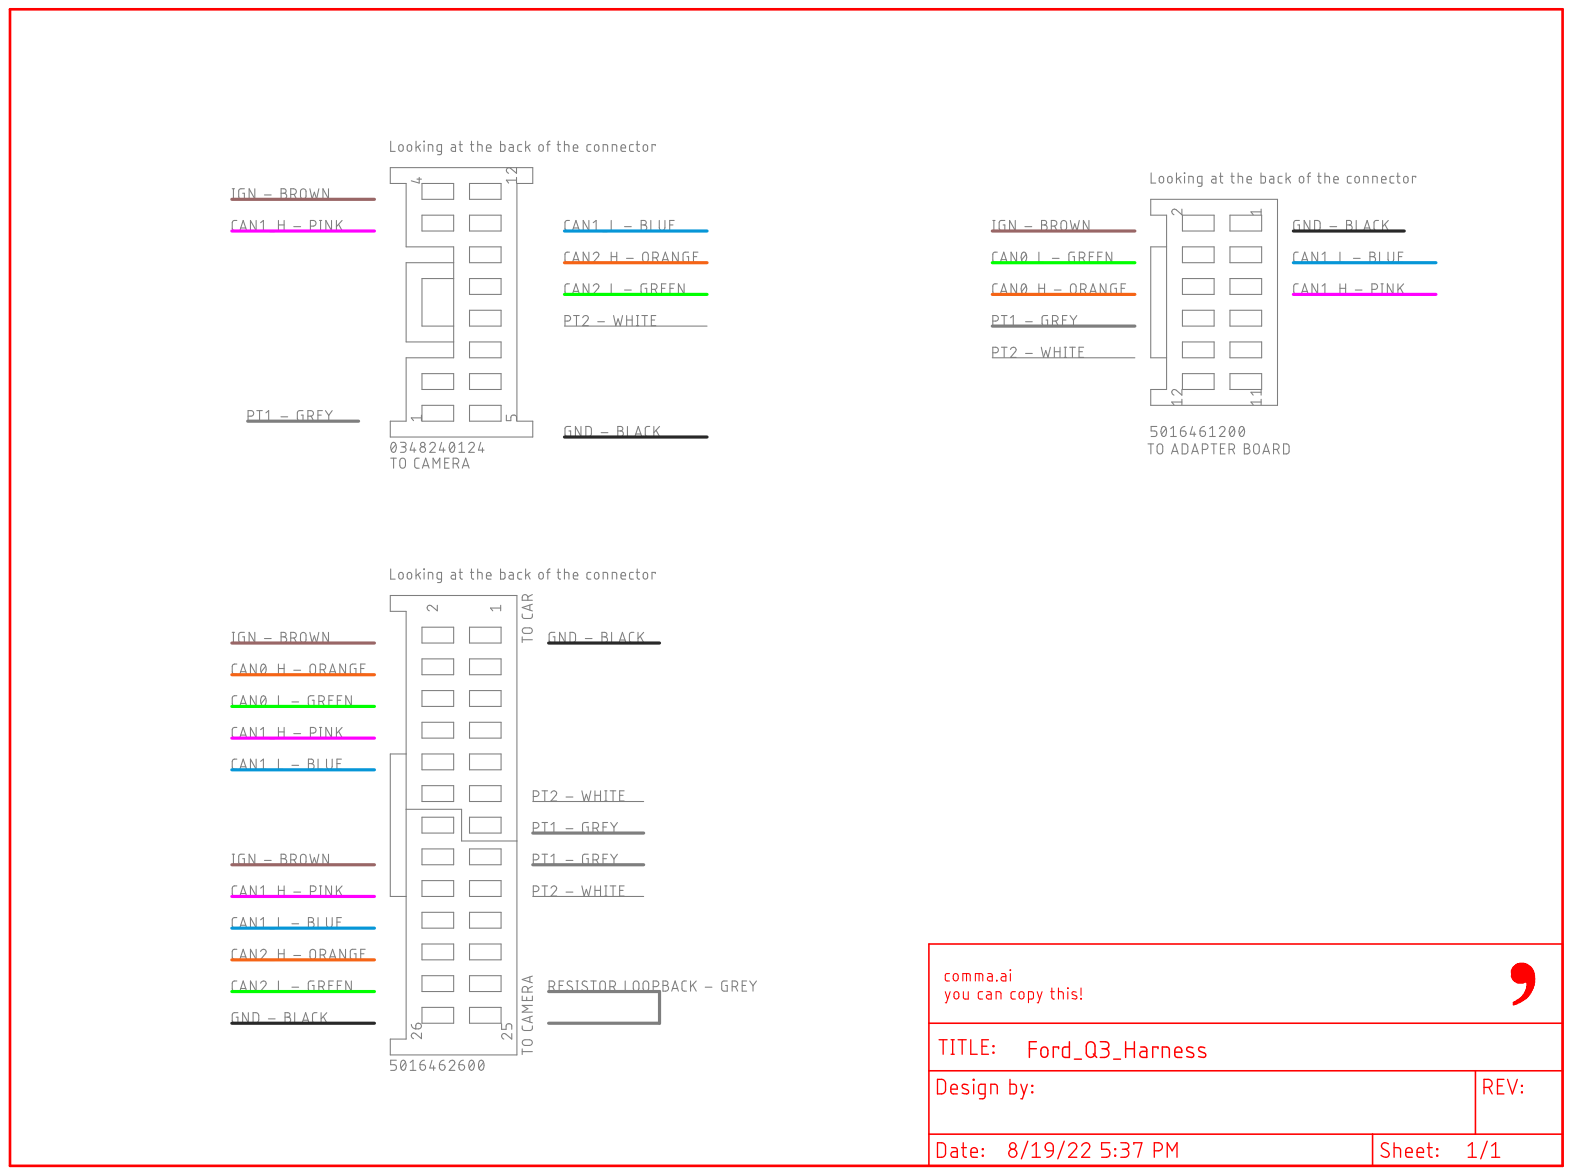
[picture p119: page 1]
