commaai/neo/car_harness/v1/Bolt_Harness.sch.pdf

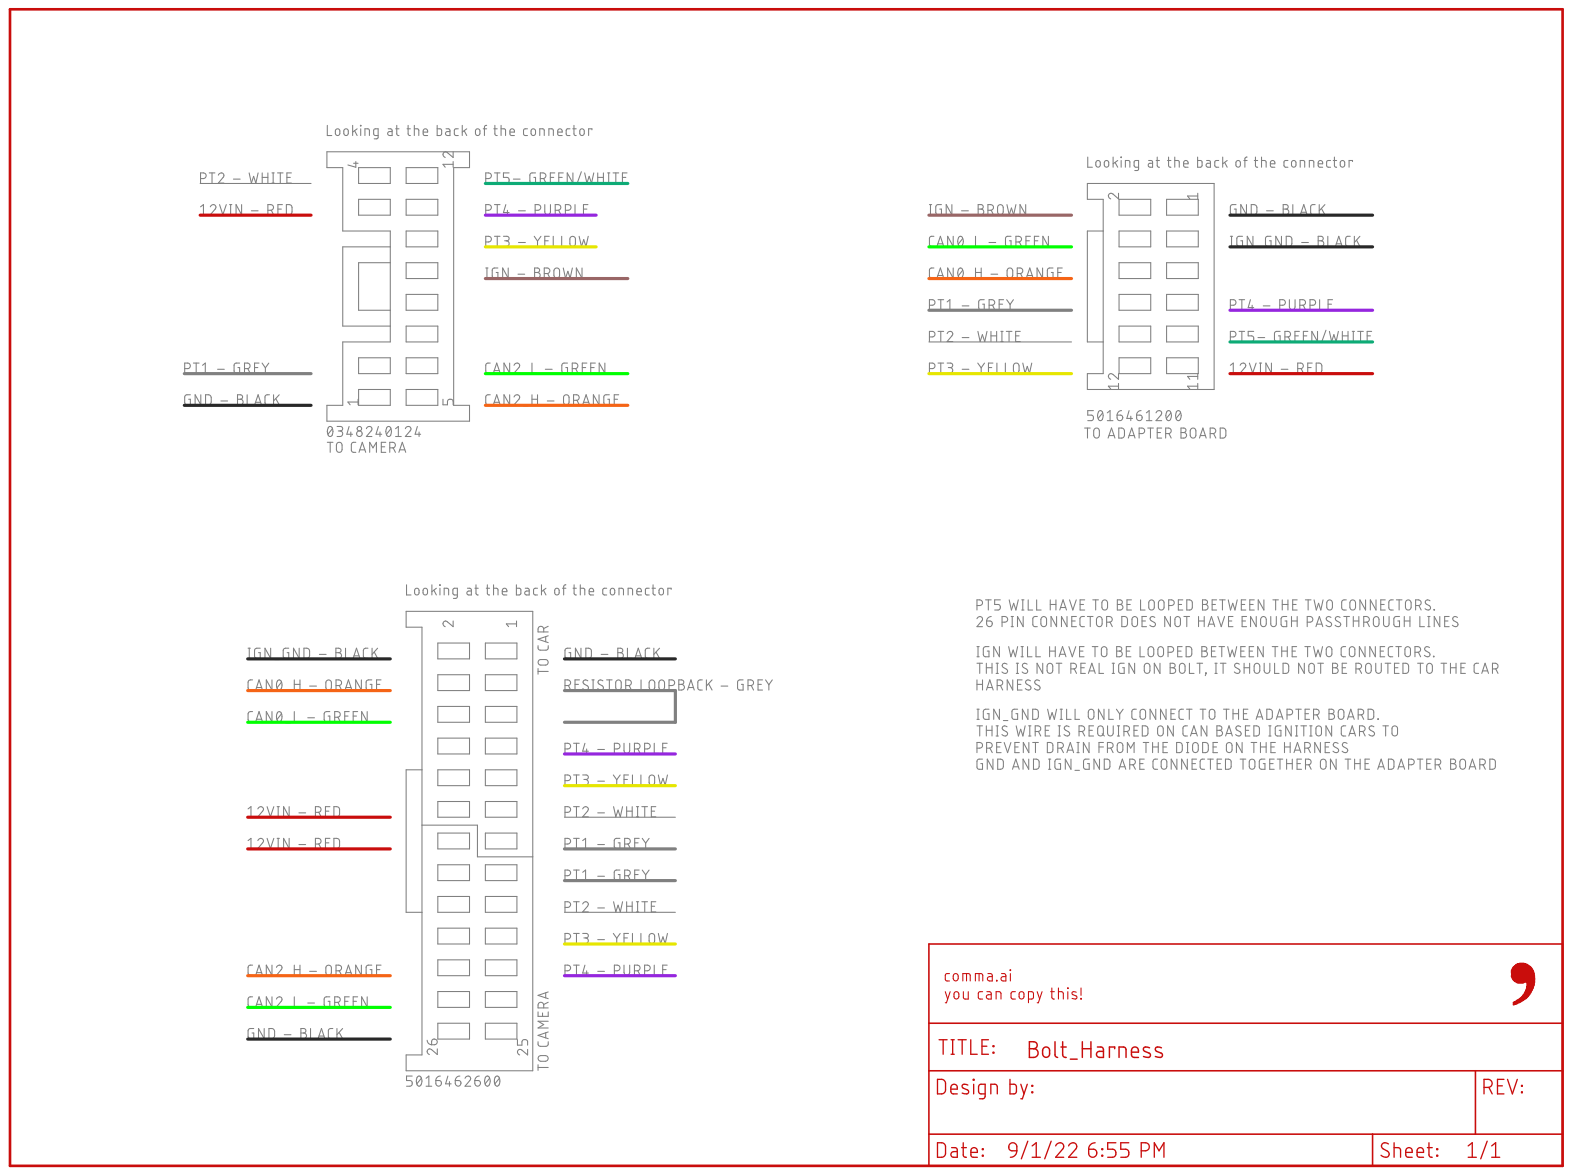
[picture p120: page 1]
