commaai/neo/car_harness/v1/Bosch_A_Harness.sch.pdf

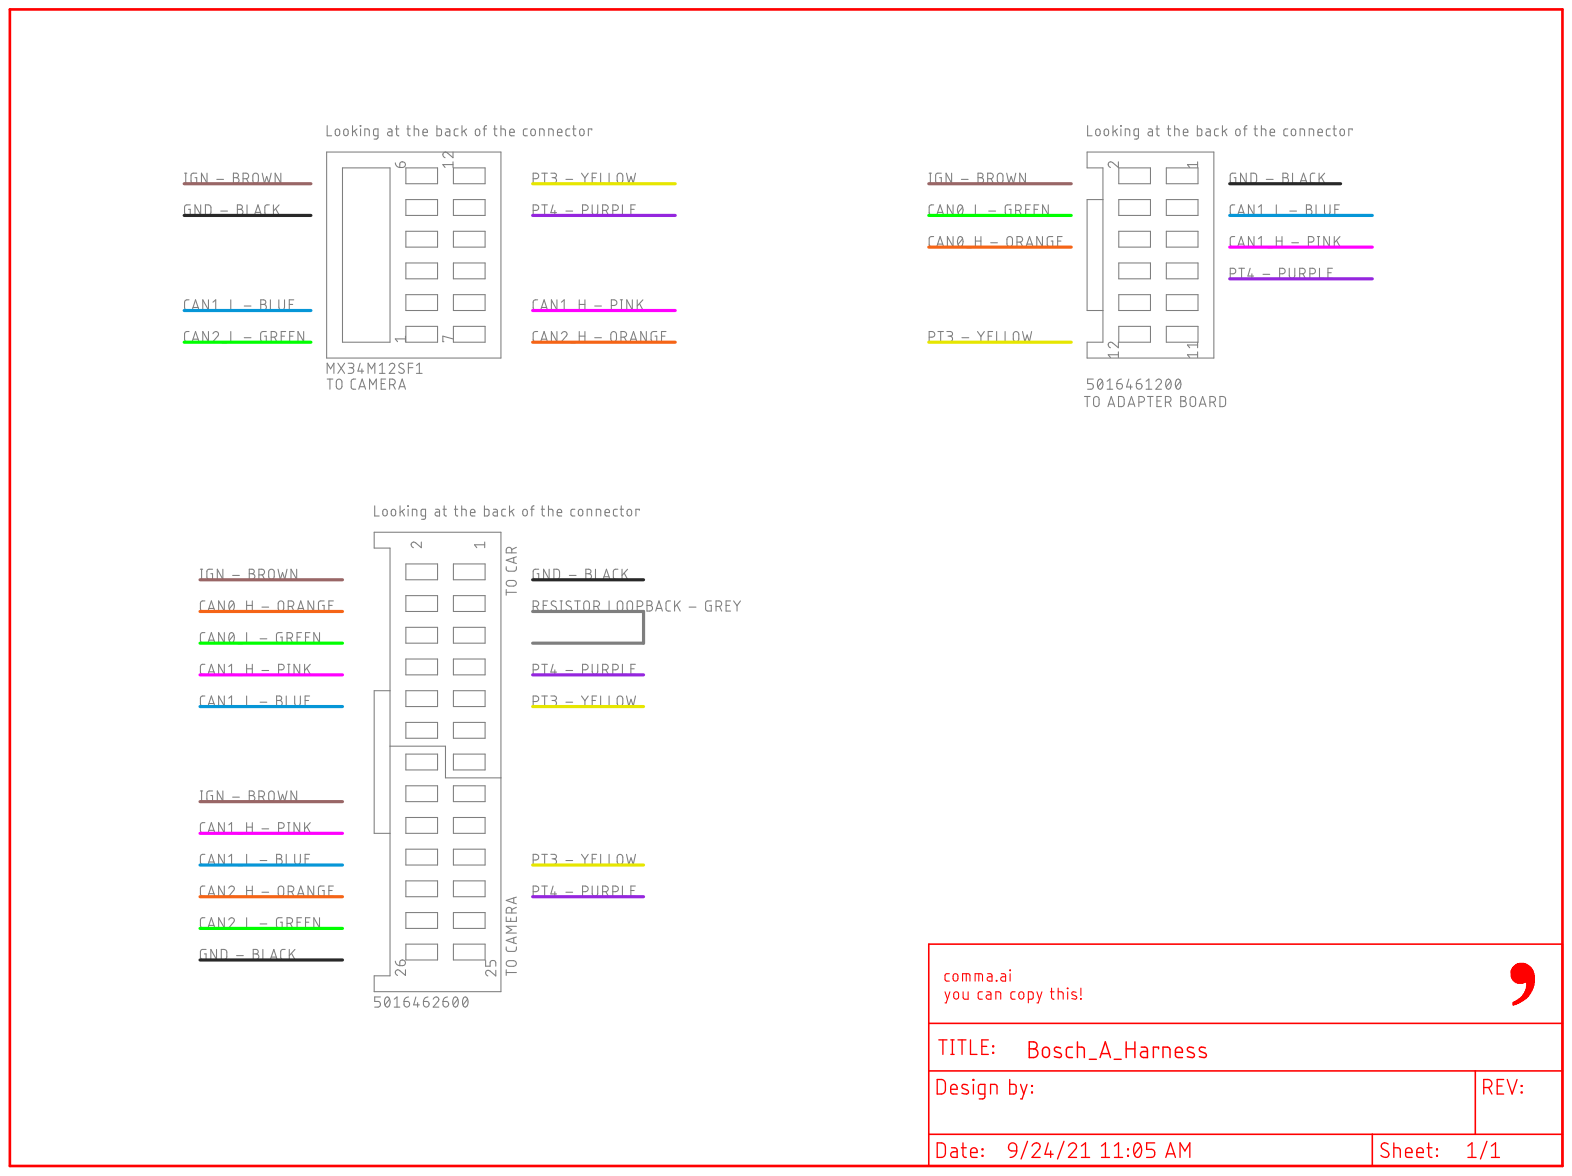
[picture p121: page 1]
