commaai/neo/car_harness/v1/Bosch_B_Harness.sch.pdf

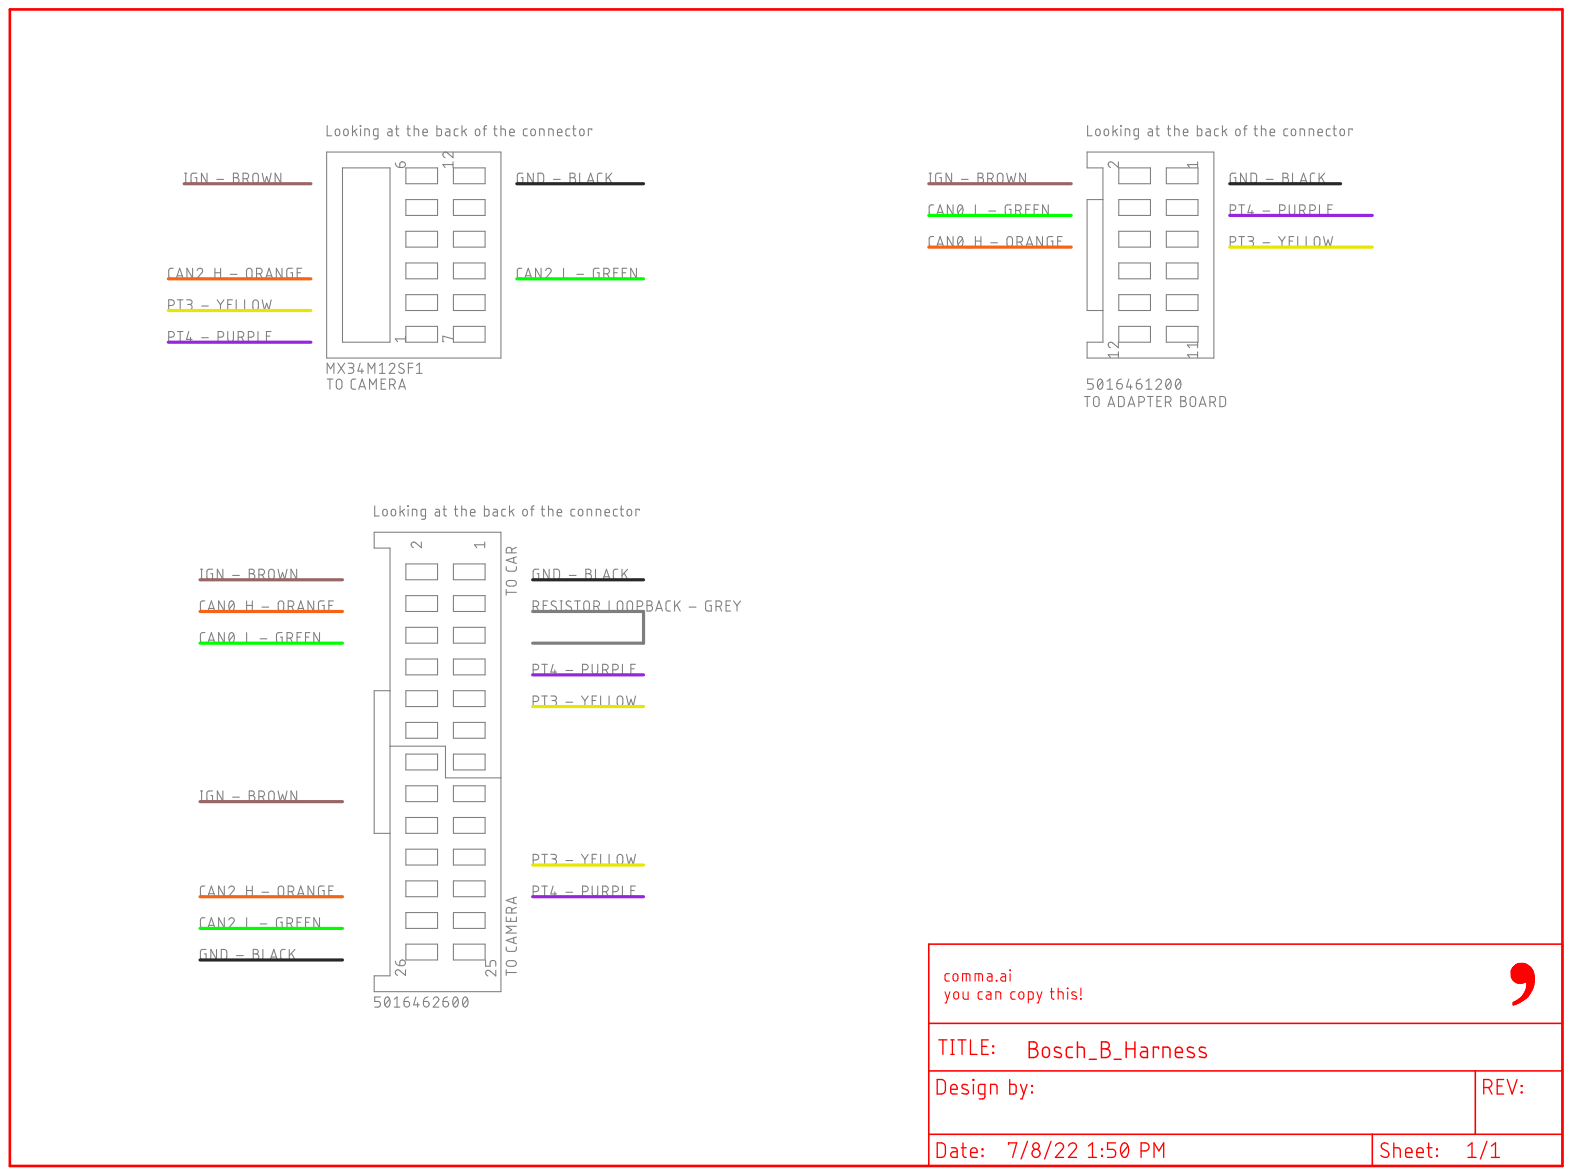
[picture p122: page 1]
