commaai/neo/car_harness/v1/EV6_Harness.sch.pdf

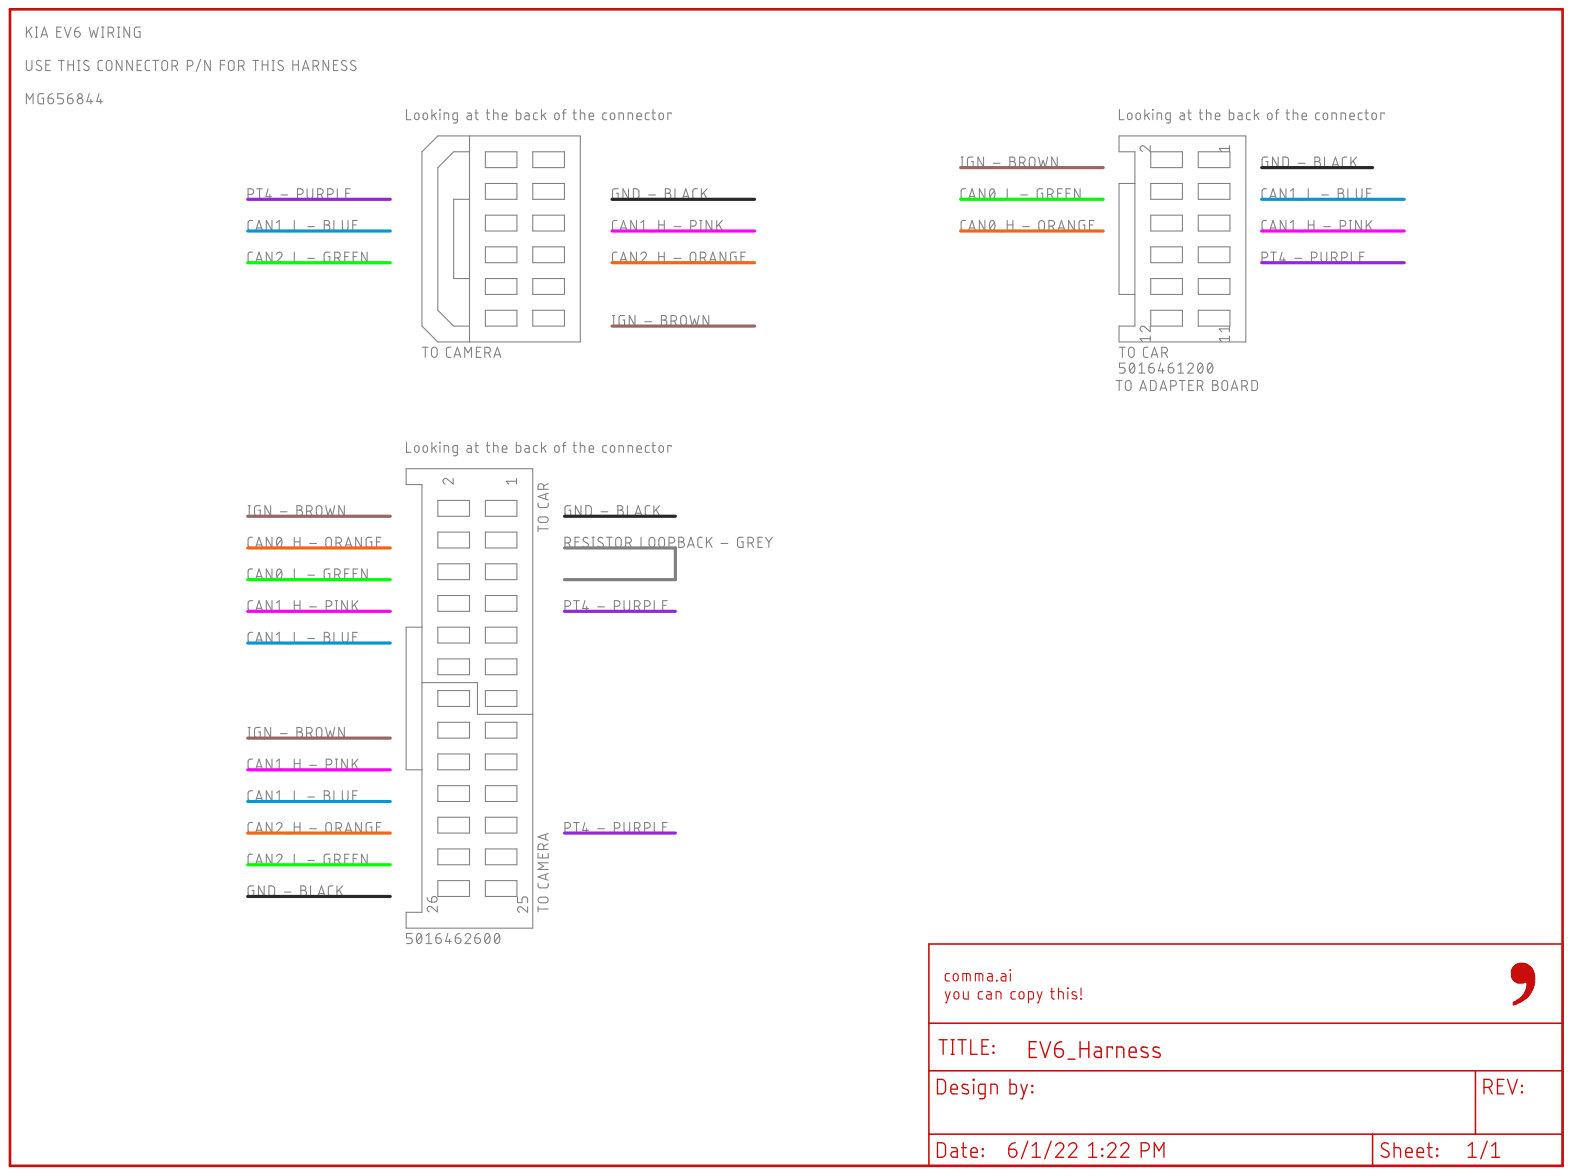
[picture p123: page 1]
