commaai/neo/car_harness/v1/Kona_Harness.sch .pdf

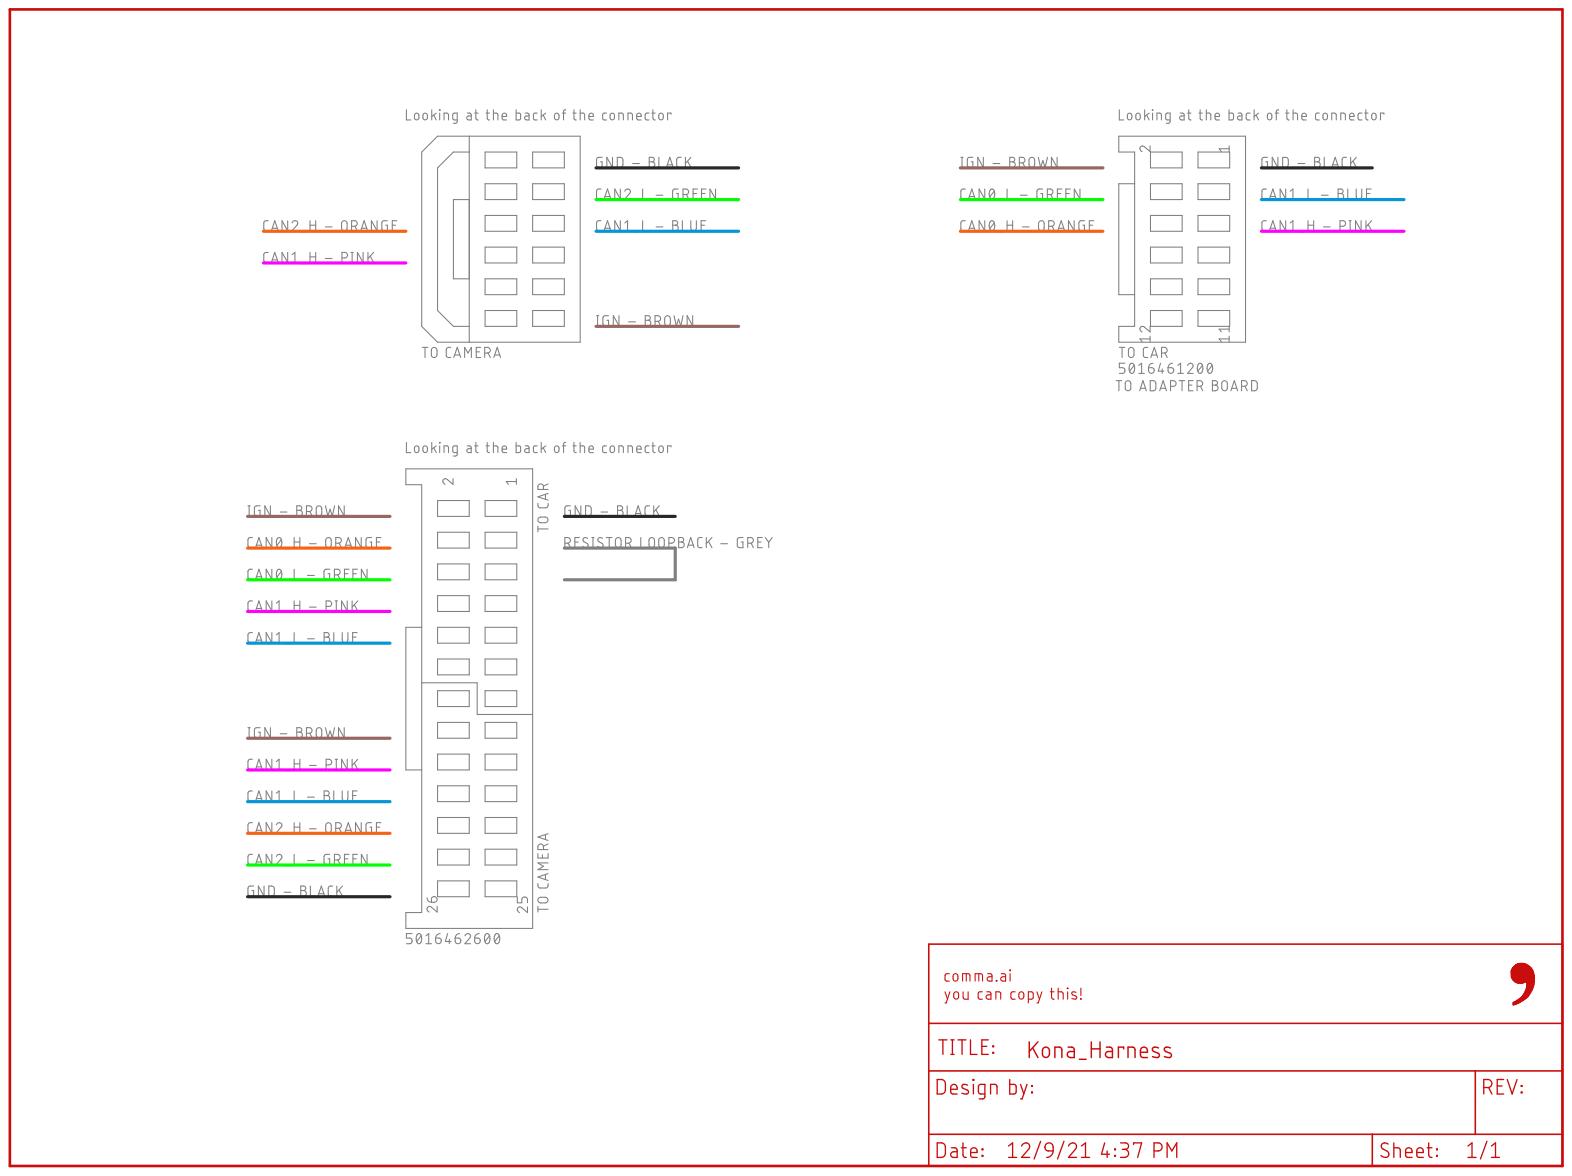
[picture p124: page 1]
