commaai/neo/car_harness/v1/Tesla_AP2+_Harness.sch.pdf

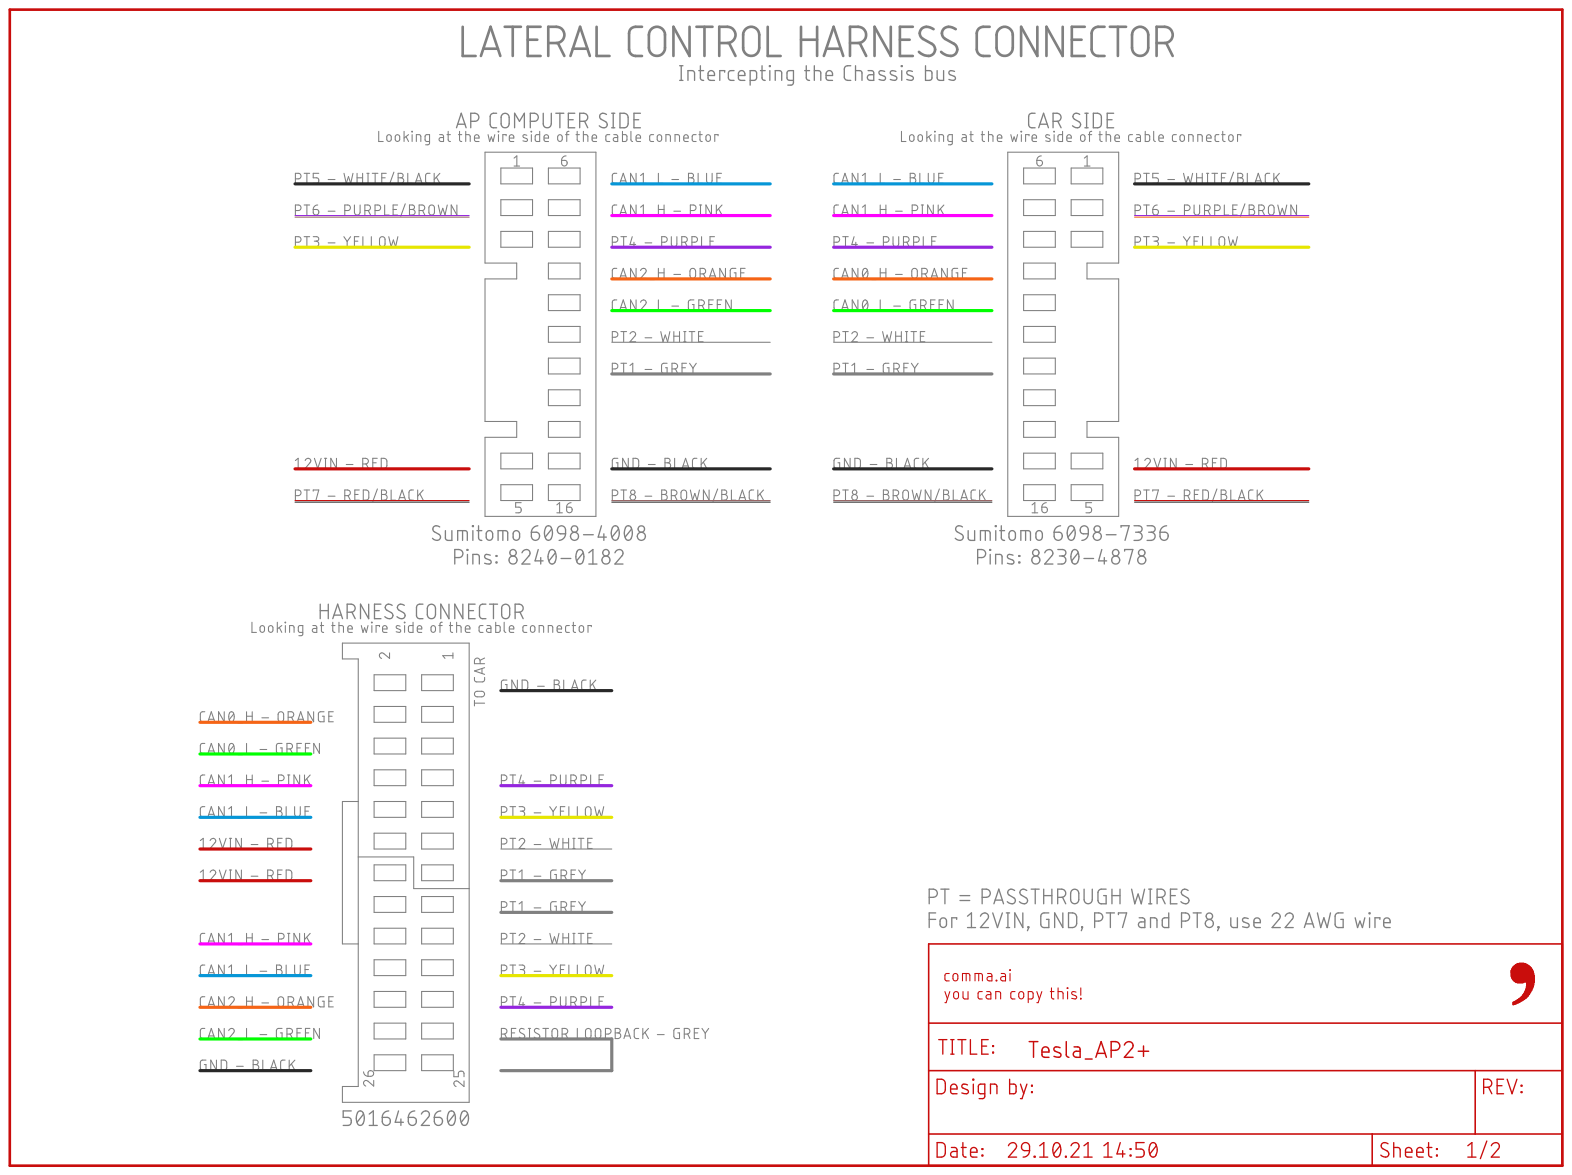
[picture p125: page 1]

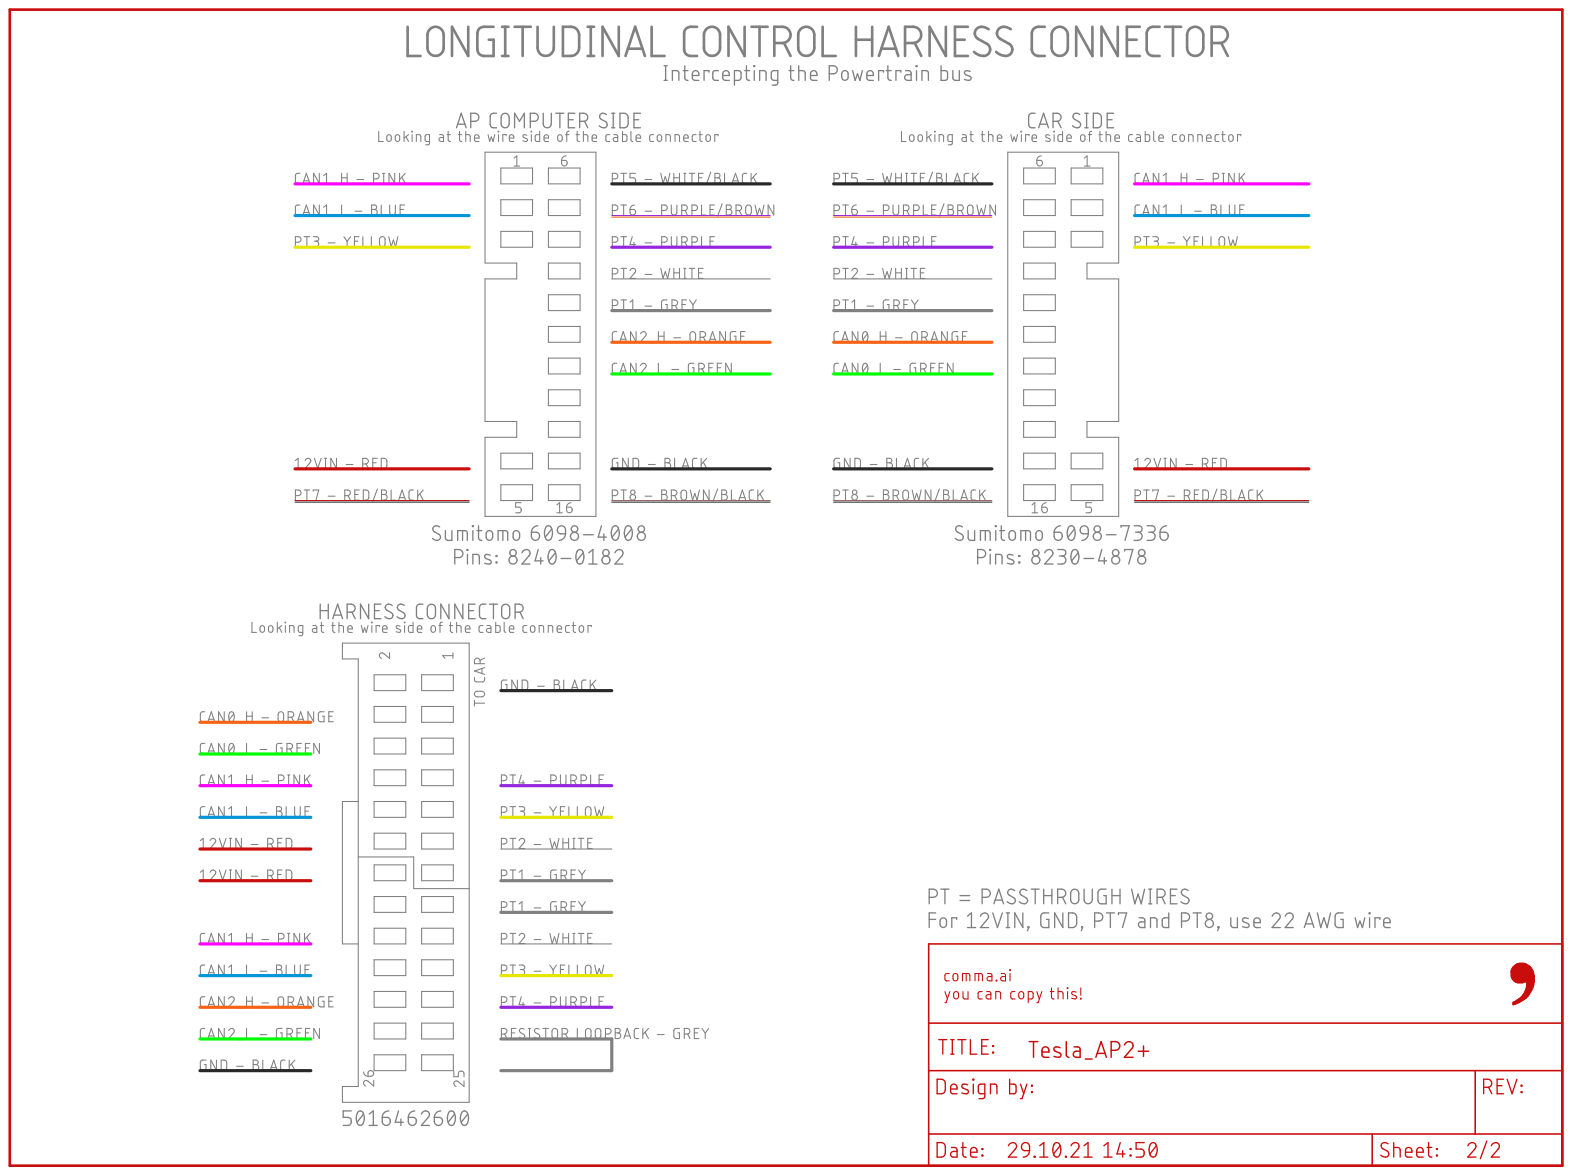
[picture p126: page 2]
