commaai/neo/car_harness/v1/J533_Harness.sch.pdf

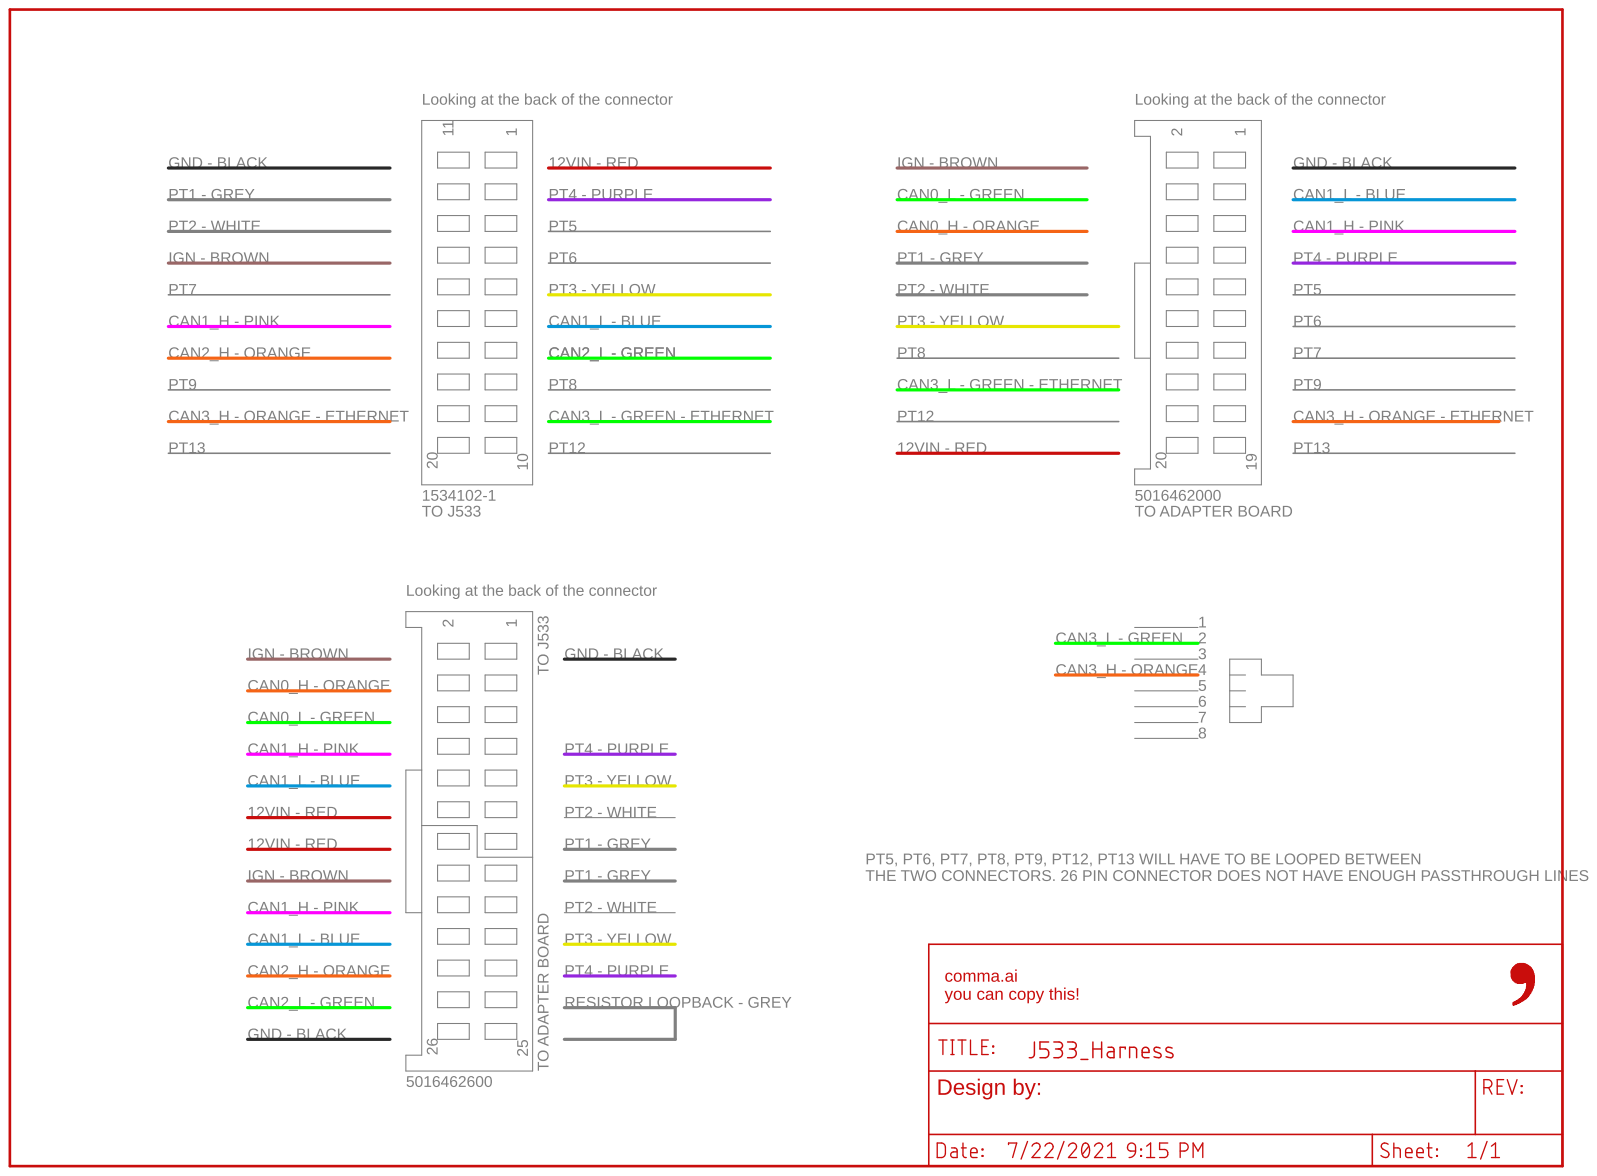
[picture p127: page 1]
