commaai/neo/car_harness/v1/Nissan_A_Harness.sch.pdf

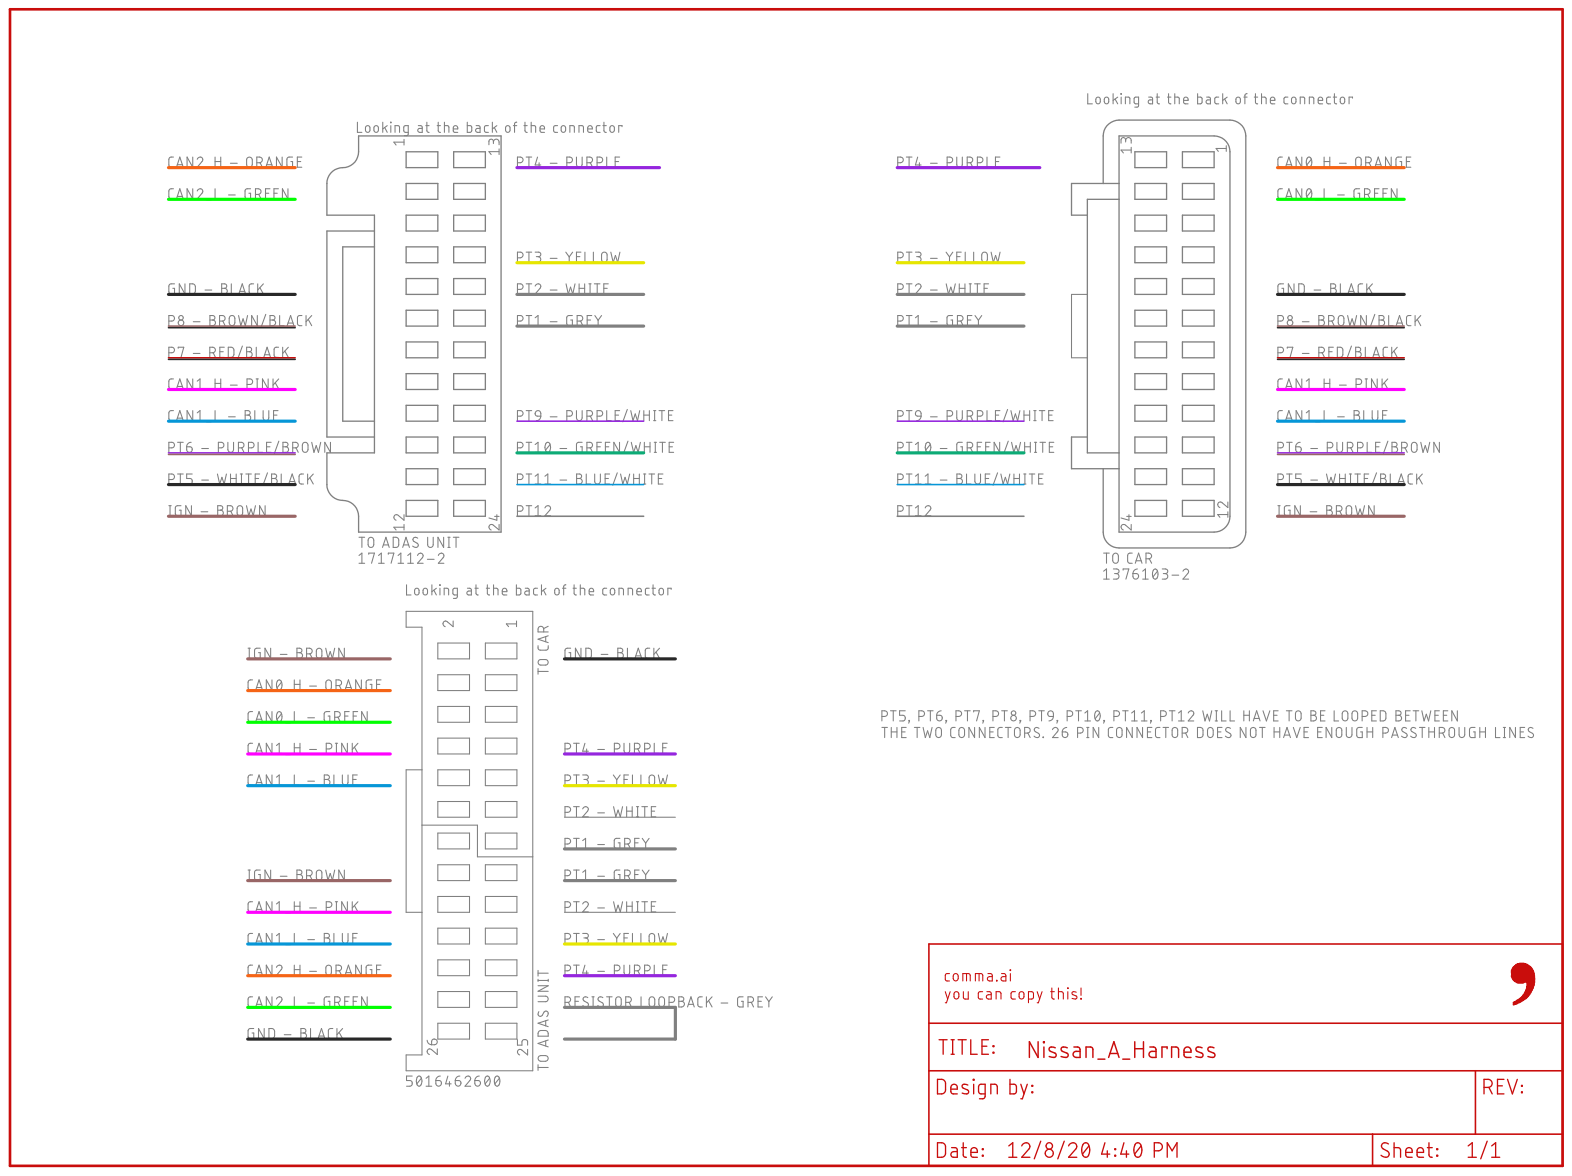
[picture p128: page 1]
