commaai/neo/car_harness/v1/Nissan_B_Harness.sch.pdf

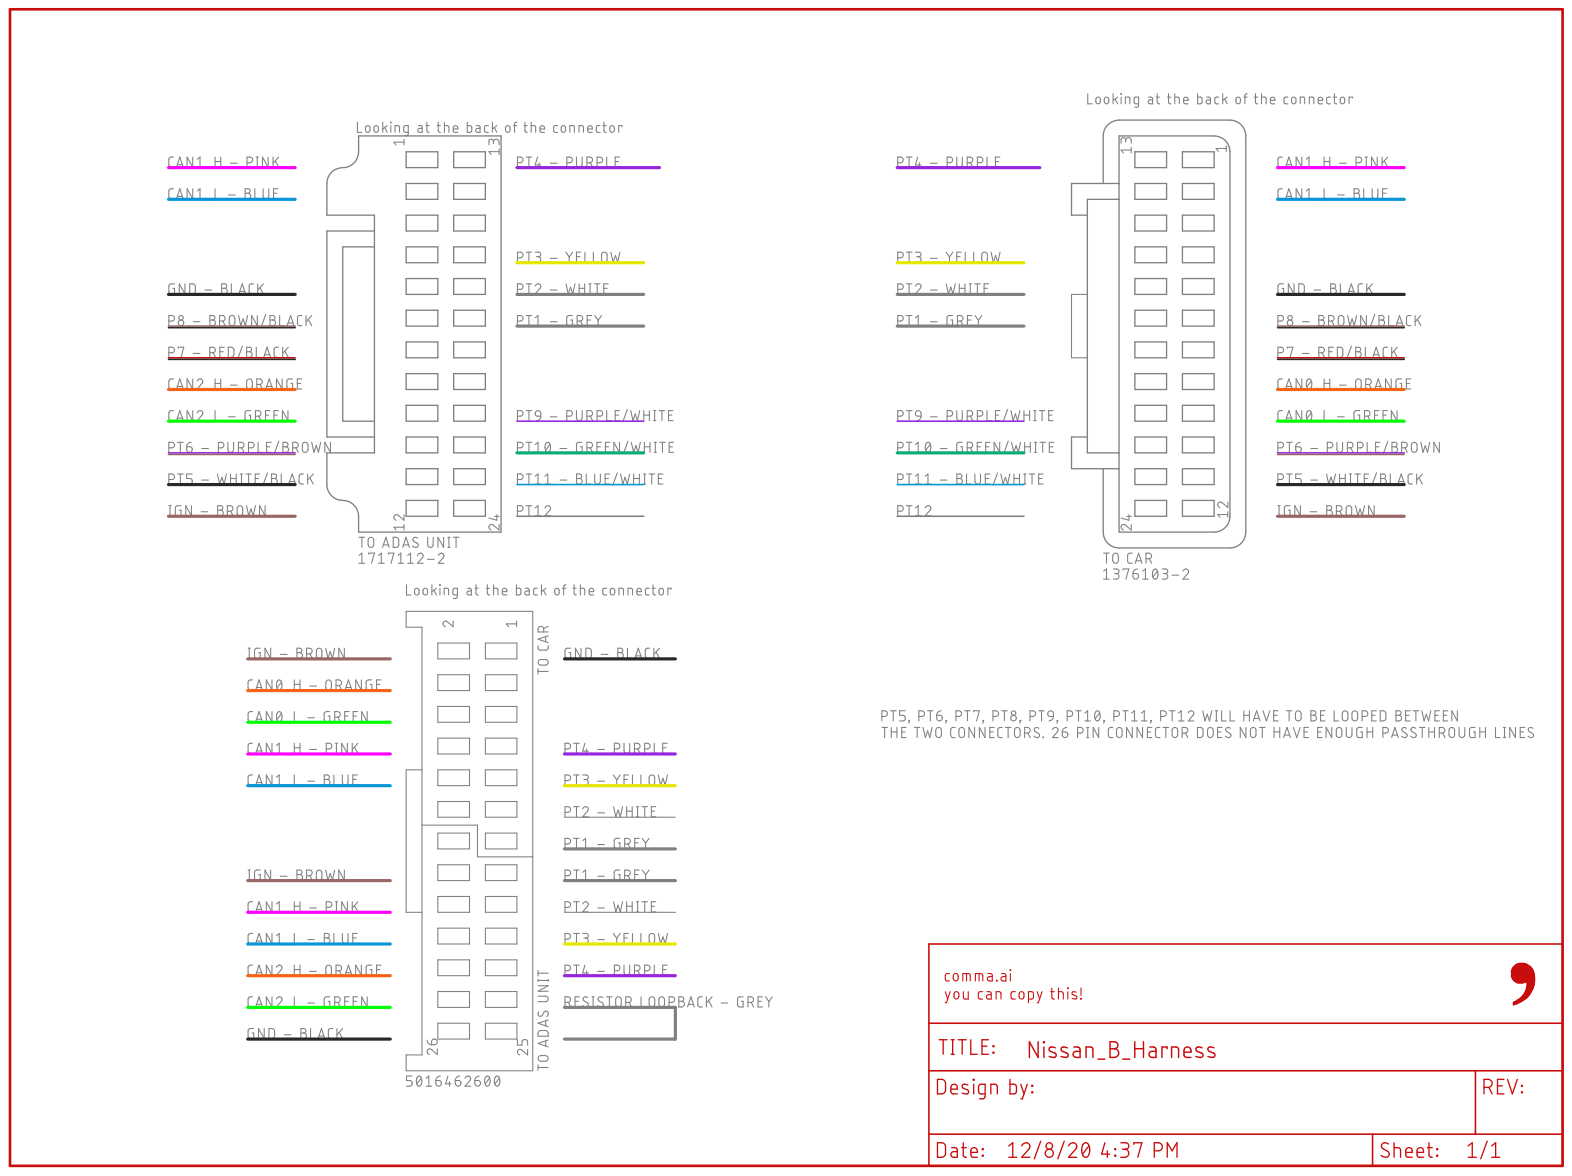
[picture p129: page 1]
